Sancte3D/AMBIENT/field-ambience-current/docs/hardware/KICAD_BLUEPRINT.md

# KiCad Blueprint — Field Ambience (idiot-proof, step by step)

**Stand: r18.40 (2026-06-21).** This is the practical "what do I click, where,
in which order" guide. It assumes you have never laid out a PCB. Read top to
bottom once, then use it as a checklist.

> **THE ONE THING YOU MUST UNDERSTAND FIRST**
>
> **You do NOT draw the schematic.** It is generated by a Python script
> (`kicad/generate_kicad_project.py`). All ~80 components, every wire, every
> net name, and every footprint assignment already exist. You never place a
> resistor or draw a wire by hand in the schematic editor.
>
> Your real job is only two things:
> 1. **Open the project and run ERC** (electrical rule check) — confirm the
>    generated schematic is clean.
> 2. **Do the PCB layout** — there is no `.kicad_pcb` yet. This is the actual
>    hand-work: place footprints, route copper, run DRC, export Gerbers.
>
> So when you wonder "where do I connect what" — it's already connected. This
> doc shows you how to *read/verify* the connections (so you trust them) and
> then how to *physically lay them out*.

---

## 0. Install + open (5 minutes)

1. Install **KiCad 9** (kicad.org/download). Not 7, not 8 — the generator
   writes the KiCad-9 file format (`KICAD_VERSION_TAG = "20231120"`).
2. (Only if you ever change parts) regenerate the schematic:
   ```bash
   cd field-ambience-current/kicad
   python3 generate_kicad_project.py
   ```
   You normally DON'T need this — the `.kicad_sch` files are already committed.
3. Open **`field-ambience-current/kicad/field_ambience.kicad_pro`** in KiCad
   (File → Open Project, pick the `.kicad_pro`).
4. The Project window shows the schematic (`.kicad_sch`) and an empty PCB slot.

---

## 1. First-time library setup (do once)

The project uses three kinds of footprints. Two come bundled in the repo and
are already wired via `kicad/fp-lib-table`; the rest are KiCad's standard
libraries that ship with KiCad 9.

| Library | Where | Already configured? |
|---|---|---|
| KiCad standard (Package_QFP, Resistor_SMD, …) | ships with KiCad 9 | ✅ via your global fp-lib-table |
| `field_ambience` (6 custom footprints) | `kicad/libraries/field_ambience.pretty/` | ✅ via project `fp-lib-table` (`${KIPRJMOD}` path) |
| Keyswitch (Kailh/stabilizer) | `kicad/libraries/keyswitch-kicad-library/` | ✅ via project `fp-lib-table` |

**What to click once:**
- **Preferences → Manage Symbol Libraries** → tab "Project Specific Libraries"
  → confirm nothing is red. If KiCad asks to migrate libraries, accept.
- **Preferences → Manage Footprint Libraries** → tab "Project Specific
  Libraries" → you should see `field_ambience` (actively used everywhere,
  incl. the cell keyswitch SW1–5 as of r18.75), plus `Switch_Keyboard_Hotswap_Kailh`
  and `Mounting_Keyboard_Stabilizer` (vendored but currently unused — r18.74's
  hot-swap-socket approach was replaced by direct-solder in r18.75; harmless
  to leave registered). If any path is red, the `${KIPRJMOD}` variable isn't
  resolving — reopen via the `.kicad_pro`, not the `.kicad_sch`.

---

## 2. Schematic phase — what to DO and what NOT to do

### DO NOT
- ❌ draw wires
- ❌ place components
- ❌ change resistor values in the GUI (change them in the generator + re-run)
- ❌ "fix" anything by editing the `.kicad_sch` directly — the next generator
   run overwrites it. The generator is the source of truth.

### DO
1. Open the root schematic. You'll see **8 hierarchical sheets** (double-click
   a sheet box to go in, breadcrumb at top to come back):
   `power_tree`, `stm32h743`, `lcd`, `mcp`, `encoder`, `audio`, `battery`.
2. **Tools → Update Symbols from Library** (refreshes R/C/L/LED/GND symbols to
   your installed KiCad-9 versions — harmless, recommended).
3. **Inspect → Electrical Rules Checker → Run ERC.**
4. Compare the result against
   [`ERC_DRC_CHECKLIST.md`](ERC_DRC_CHECKLIST.md):
   - **0 errors** required.
   - Only the *intended* warnings listed there are allowed (power-pin-not-driven
     on the +5V bridge labels, PB3/SWO not connected, single MIDI_TX label,
     MCP reserve pins). Anything else must be understood before layout.
5. If ERC is clean per the checklist → schematic phase is DONE. Move to §4.

> Why bother if it's generated? Because the generator's structural checks
> (paren balance, 100/100 pin connectivity, hier↔root crossref) are NOT the
> same as KiCad's electrical check. The GUI ERC is the gate before layout
> (`PCB_LAYOUT_STATUS.md` blocker **B3**). It has never been run in a GUI yet —
> you are the first to do it.

---

## 3. Connection reference (so you can SEE what's connected to what)

You don't wire these — this is just the map, so when you look at the schematic
or route the board you know what each net is. Full detail: `SPEC_v0.7.md §5`.
Parts + order links: `BOM_MASTER.md`.

### 3.1 Block diagram (signal flow)

```
        USB-C (J1) ──► PTC F1 ──► TVS ──► +5V rail ──► TPS61089 boost (U8)+L1
            │                                  │
            │ D+/D-/CC (ESD via D1)            ├──► AP7361C LDO (U5) ──► +3V3 rail
            │                                  │
       BQ24074 power-path charger (U7, r19.18 ADR-0023) ◄── F2 PTC ◄── battery (J9, LiPo)
                                               │
   ┌───────────────────────── +3V3 ───────────┴───────────────────────┐
   │                                                                    │
   STM32H743 (U1, LQFP-100)                                             │
   │  ├─ SAI1 (I²S) ──► PCM5102A DAC (U3) ──► PAM8403 amp (U4) ──► SPK L/R (J6/J7)
   │  │                                            └─ Line-Out jack (J8, mutes spk)
   │  ├─ SPI1 ──────► ST7789 LCD (J3 header)
   │  ├─ I²C1 ──┬──► MCP23017 (U2) ──► 10 buttons (5 cell + 5 modifier) + jack-detect
   │  │         └──► PCA9685 (U6) ──► 15 LEDs + LCD backlight FET (Q2)
   │  ├─ TIM1/2/3/4 QEI ──► 4 encoders (EN1-EN4)
   │  ├─ ADC ──► BAT_SENSE (cells are digital on the MCP23017 now — r18.73)
   │  ├─ USART2 ──► MIDI TX (J9, DNP for now)
   │  └─ USB-OTG-FS (PA11/PA12) + SWD (J4 Tag-Connect)
   └────────────────────────────────────────────────────────────────────┘
```

### 3.2 STM32H743 pin map (the 30 used GPIOs)

| Net | Pin | Port | Goes to |
|---|---|---|---|
| I2S_LRCK | 3 | PE4 | PCM5102A pin 15 |
| I2S_BCK | 4 | PE5 | PCM5102A pin 13 |
| I2S_DOUT | 5 | PE6 | PCM5102A pin 14 |
| LCD_SCK | 29 | PA5 | LCD SCL |
| LCD_MOSI | 31 | PA7 | LCD SDA |
| LCD_CS | 30 | PA6 | LCD CSn |
| LCD_DC | 32 | PC4 | LCD D/C |
| LCD_RES | 33 | PC5 | LCD reset |
| I2C_SCL | 92 | PB6 | MCP23017 + PCA9685 (+ 4.7 kΩ pull-up to +3V3) |
| I2C_SDA | 93 | PB7 | MCP23017 + PCA9685 (+ 4.7 kΩ pull-up to +3V3) |
| MCP_INT | 7 | PC13 | MCP23017 INTA |
| DRIVE_A/B | 22/23 | PA0/PA1 | EN1 (TIM2) |
| BRIGHT_A/B | 63/64 | PC6/PC7 | EN2 (TIM3) |
| DISPLAY_A/B | 59/60 | PD12/PD13 | EN3 (TIM4) |
| VOL_A/B | 67/68 | PA8/PA9 | EN4 (TIM1) |
| DRIVE/BRIGHT/DISPLAY_SW | 97/98/2 | PE0/PE1/PE3 | encoder push switches (EN4_SW on MCP GPB5) |
| CELL1..5_BTN | MCP23017 GPA0–4 | (over I²C) | 5 cell tactile switches SW1–5 → GND (r18.73; PC0/PC1/PA4/PB0/PB1 now free) |
| BAT_SENSE | 25 | PA3 | 100k/100k divider off battery (ADC) |
| AMP_nSHDN | 53 | PB14 | PAM8403 /SHDN (10 kΩ pull-down) |
| AMP_nMUTE | 54 | PB15 | PAM8403 /MUTE (10 kΩ pull-down) |
| STATUS_LED | 55 | PD8 | heartbeat LED |
| MIDI_TX | 86 | PD5 | TRS jack (DNP) |
| USB_DM/DP | 70/71 | PA11/PA12 | USB-C data via D1 ESD |
| SWDIO/SWCLK | 72/76 | PA13/PA14 | J4 SWD |
| HSE | 12/13 | PH0/PH1 | 8 MHz crystal Y1 + 2× 27 pF |
| NRST / BOOT0 | 14 / 94 | — | reset / boot (BOOT0 1 kΩ pull-down + button) |

**Power pins (just connect to rails — no logic):** VDD (11,27,50,75,100)→+3V3,
VSS (10,26,49,74)→GND, VBAT(6)→+3V3, VDDA(21)→+3V3 via ferrite, VREF+(20)→VDDA,
VSSA(19)→GND, VCAP1/2 (48,73)→2.2 µF each to GND.

### 3.3 The resistor/cap values you'll see (already placed by generator)

| Where | Value | Why |
|---|---|---|
| I²C pull-ups (2×) | 4.7 kΩ 0603 | SDA/SCL to +3V3 |
| LED ballast (15×) | 390 Ω 0603 | each LED, +5V anode → LED → PCA9685 sink |
| BAT_SENSE divider | 100 kΩ + 100 kΩ 0603 | halves battery V into ADC range |
| BOOT0 pull-down | 1 kΩ 0603 | boots to flash, button overrides |
| AMP /SHDN, /MUTE pull-downs | 10 kΩ 0603 | amp boots OFF + muted (pop-free) |
| ~~Hall RC (per cell)~~ | — | removed r18.73 — cells are digital switches on the MCP23017 |
| HSE load caps | 2× 27 pF C0G 0603 | crystal |
| VDD decoupling (per pin) | 4.7 µF 0805 + 100 nF 0603 | 1 pair per VDD pin |
| VDDA filter | ferrite BLM18AG601 + 1 µF + 100 nF | analog isolation |
| VCAP1/VCAP2 | 2.2 µF X5R 0603 each | internal SMPS bulk |
| C_BULK / C_BULK2 | 470 µF tantal + 100 µF MLCC | boost output bulk |
| I²S series term (if used) | 33 Ω 0603 | — |

You change these by editing the generator, not the GUI. They're listed so you
recognise them on the board.

---

## 4. Footprints — already assigned, just verify

Every symbol already has a footprint (the generator sets it). You don't assign
them. To confirm:

- **Tools → Assign Footprints** (CvPcb) — opens the symbol↔footprint list.
  Everything should already be filled. Spot-check the custom ones:

| Ref | Footprint | Library |
|---|---|---|
| U1 STM32 | `Package_QFP:LQFP-100_14x14mm_P0.5mm` | KiCad std |
| U8 boost | `field_ambience:Texas_VQFN-HR-11_2x2.5mm_P0.5mm_RNR0011A` | custom |
| L1 inductor | `field_ambience:L_Sunlord_SWPA6045` | custom |
| Y1 crystal | `field_ambience:Crystal_HC49-US-SMD_ABLS` | custom |
| J8 audio jack | `field_ambience:Jack_3.5mm_PJ-320D_SMT` | custom |
| SW1-5 cells (real keyswitch, direct-solder, r18.75) | `field_ambience:SW_KailhChoc_CPG1350_THT_2P` | pulled from LCSC/EasyEDA for C400229 via `easyeda2kicad`, incl. 3D STEP — same method as this repo's other custom footprints |
| SW6-10 modifiers | `field_ambience:SW_TC1212-7.3_THT_4P` | custom (HX B3F-4055, C36498965) |
| SW11/SW_BOOT | `field_ambience:SW_TS1088_SMD` | custom |
| J1 USB-C | `Connector_USB:USB_C_Receptacle_HRO_TYPE-C-31-M-12` | KiCad std |

Full table: `BOM_MASTER.md` and `PCB_FOOTPRINT_RISK_AUDIT.md`. The audit also
tells you which ones are *mechanically critical* (must match the enclosure) —
read §6 of that file before placing them.

---

## 5. Schematic → PCB (the transfer — this CREATES the empty board)

1. From the schematic editor: **Tools → Open PCB Editor** (or from the project
   window, double-click the `.kicad_pcb` slot — KiCad offers to create it).
2. In the PCB editor: **Tools → Update PCB from Schematic** (hotkey **F8**).
3. Dialog appears — leave defaults, click **Update PCB**. Now ALL footprints
   appear in a pile off to the side, with thin "ratsnest" lines showing every
   connection from the schematic. **This is your wiring made physical** — you
   never drew it, the netlist carries it over.
4. Click **Close**. You now have an unrouted board.

> Re-run F8 any time the schematic changes — it syncs new parts/nets without
> destroying your placement.

---

## 6. Board setup (do this BEFORE placing/routing) — Tools → Board Setup

### 6.1 Layer stack-up (SPEC §9)
- **File → Board Setup → Board Stackup → Physical Stackup**: set **4 layers**.
- Assign: **F.Cu = Signal**, **In1.Cu = GND** (solid pour), **In2.Cu = +5V**
  (power), **B.Cu = Signal**. Board thickness **1.6 mm**.

### 6.2 Design Rules (Board Setup → Design Rules → Constraints)
JLCPCB 4-layer econ capabilities:
- Min track width: **0.15 mm** (set clearance default 0.15 mm too)
- Min via: **0.3 mm drill / 0.45 mm diameter** (annular ≥ 0.075 mm)
- Min hole-to-hole: 0.5 mm

### 6.3 Net classes (Board Setup → Net Classes) — set track widths
| Class | Track width | Apply to |
|---|---|---|
| Default (signal) | 0.25 mm | everything |
| Power | 0.5 mm | +3V3 |
| HighCurrent | 0.8 mm | +5V, VBAT, boost SW node, speaker outputs |
| GND | use the pour, not tracks | — |

(The generator's `.kicad_pro` already sets `copper_line_width = 0.2` as the
editor default; the net classes above override per-net where current needs it.)

---

## 7. Placement + routing order (the actual layout work)

Place in this order — group by sub-circuit, keep loops short:

1. **Fixed/mechanical first** (these are constrained by the enclosure — see
   `PCB_FOOTPRINT_RISK_AUDIT.md §6` + `mechanical/coordinates/`):
   USB-C (board edge), audio jack (board edge), LCD header, the 5 cell switches
   (SW1–5) on the 19 mm grid, 5 modifier buttons (SW6–10), 4
   encoders, battery connector, mounting holes.
2. **Power section**: USB-C → F1 → TPS61089 + L1 + bulk caps. Keep the boost
   loop (U8 ↔ L1 ↔ C_OUT) as tight as possible — this is the #1 power rule
   (SPEC §5.1, TI datasheet §10). Then the LDO.
3. **MCU + decoupling**: STM32 in the middle, each VDD's 4.7 µF+100 nF pair
   *right next to its pin*. Crystal Y1 + its 2 caps as close to PH0/PH1 as
   possible with a guard.
4. **Audio**: PCM5102A close to the MCU's SAI pins, its decoupling < 5 mm,
   single-star GND between audio and digital, ferrite beads in the speaker
   lines (SPEC §5.1 audio-layout-constraints — read those 5 points).
5. **I/O**: MCP23017, PCA9685, LEDs near their buttons/cells.

**Then route:**
- **Pour GND on In1.Cu** (Place → Add Filled Zone → pick GND net, draw over
  whole board). Pour **+5V on In2.Cu**. Right-click a zone → **Fill All Zones**
  (hotkey **B**) after routing.
- Route power (thick) first, then clocks/I²S, then the rest. Use the net-class
  widths from §6.3.
- Right-click a track → **Properties** to change width; right-click a pad →
  **Highlight Net** to see where it goes.

---

## 8. Verify + export (the order-ready gate)

1. **Inspect → Design Rules Checker → Run DRC.** Target per
   `ERC_DRC_CHECKLIST.md`: **0 errors, 0 clearance/mechanical/routing
   warnings.** Unconnected nets = forgotten routing.
2. **3D view (Alt+3)**: check nothing collides, parts sit where the enclosure
   expects. Compare against `mechanical/3d_models/MANIFEST.md` heights.
3. **1:1 paper print** of the board outline + cutouts, hold the real
   USB-C/jack/encoder/cells against it (audit §11).
4. **Export Gerbers**: File → Fabrication Outputs → Gerbers + Drill files.
5. **BOM + CPL** for JLC assembly: File → Fabrication Outputs → BOM, and the
   Placement (CPL) file. Cross-check LCSC numbers against `BOM_MASTER.md`.
6. In JLCPCB's web uploader: load Gerbers, then BOM+CPL, then **walk the
   assembly preview part by part** — look for flipped pin-1 markers and any
   "footprint not found". Pay attention to the 6 custom footprints.

---

## 9. Cheat-sheet — right-click / hotkeys you'll actually use

**Schematic editor:**
- `E` — edit properties of selected item
- Inspect → Electrical Rules Checker — the ERC
- Tools → Update Symbols from Library — refresh std symbols
- Tools → Assign Footprints (CvPcb) — view symbol↔footprint map

**PCB editor:**
- `F8` — Update PCB from Schematic (sync after any schematic change)
- `X` — start routing a track from a pad
- `B` — fill all zones (GND/power pours)
- `E` — edit selected track/footprint properties (width, layer)
- `M` — move, `R` — rotate, `F` — flip to other side
- `D` — drag track keeping connections
- right-click pad/track → **Highlight Net** — trace a connection visually
- right-click → **Properties** — change track width / via size
- `Alt+3` — 3D viewer
- Inspect → Design Rules Checker — the DRC

---

## 10. What is NOT done yet (so you know the edges)

- **No `.kicad_pcb` exists** — §5 creates it; everything in §6–8 is greenfield.
- **GUI-ERC never run** — you are the first (blocker B3).
- **TPS61089 layout** needs the TI datasheet §10 study before routing (audit §7).
- **LCD header pin order** must be checked against the actual Waveshare module
  you receive — vendor batches vary (audit §11).
- **Enclosure CAD** isn't final, so the mechanical-critical X/Y positions in
  `mechanical/coordinates/` may still move — confirm before you commit to edge
  placements.

---

### Where the truth lives (don't trust this doc over these)
- Connections / values / pins → `kicad/generate_kicad_project.py` + `SPEC_v0.7.md §5`
- Parts / order links / footprints → `BOM_MASTER.md`
- Footprint risk + mechanical-critical list → `PCB_FOOTPRINT_RISK_AUDIT.md`
- ERC/DRC pass criteria → `docs/hardware/ERC_DRC_CHECKLIST.md`
- Current overall state → `PROJECT_STATUS.md`
