Sancte3D/AMBIENT/field-ambience-current/docs/hardware/MECHANICAL_REQUIREMENTS.md

# Mechanical Requirements — Gehäuse & PCB-Constraints

Diese Datei listet **alle mechanisch-fixierten Bauteile** mit ihren
Constraint-Maßen + Gehäuse-Anforderungen, damit das Case-CAD (3D-Print) und
das PCB-Layout gleichzeitig entstehen können, ohne sich gegenseitig zu blocken.

Adressat: PCB-Designer (Bauteilplatzierung Schritt 7 des PCB-Workflows) +
3D-CAD-Designer (Gehäuse-Modellierung). Beide brauchen die selben Maße.

> **Status:** PROPOSED — die Maße sind aus Datenblättern + bestehenden ADRs
> abgeleitet. **UNVERIFIED**-Markierungen wo eine Datenblatt-Quelle fehlt.
> Bevor die Mechanik final ist, müssen die UNVERIFIED-Items mit dem realen
> Bauteil in der Hand bestätigt werden (Anti-Guess, CLAUDE.md).

---

## 0. Globale Constraints

| Constraint | Wert | Quelle |
|---|---|---|
| Gerät handheld, 1-Hand-Bedienung | ja | PROJECT_STATUS §2 |
| Max. PCB-Außenmaße | **TBD — User entscheidet** | hängt am Gehäuse-Form-Faktor |
| Vorgeschlagen: ~120 × 80 mm (Stack-Mate-OP-1-Klasse) | Vorschlag | basiert auf 4 Encoder + 5 Cells + Display + Speakers passen müssen |
| PCB-Dicke | 1,6 mm | ADR-0018 (JLCPCB Default 4-Layer) |
| Layer-Stack | 4-Layer | ADR-0018 |
| Mounting (Schraube) | M3 × 4 Eckbohrungen, Ø 3,2 mm Drill | Standard, Gehäuse muss Pillars/Standoffs liefern |
| Gehäuse-Material | 3D-Print PLA/PETG (Single-Color OP-1-Look) | Cost-Trade-Off, kein Alu-CNC (Cost) |
| Bottom-Plate abnehmbar | ja, für Service-Bohrungen `SW11` (Reset) + `SW_BOOT` (DFU) + Akku-JST-Zugang | ADR-0008/Service-Strategie |

---

## 1.0 External / visible components — case-design inventory

Everything that appears on an **outer surface** of the enclosure — i.e. what the
case must provide a window / cutout / hole / grille / slot for. Placement of most
of these is **your design**; this is the *inventory*, not a layout.

**Headline counts:**

- **Touch controls: 15** → 4 encoders + 5 cell keys + 5 modifier buttons + 1 power switch
- **Display: 1** window
- **Indicator LEDs: 23** (light points needing egress) → 5 modifier + 10 cell + 8 VU-meter
- **Ports: 3** → USB-C + line-out + MIDI
- **Speakers: 2** grilles
- **Bottom service: 2 pinholes + battery access + 4 screws**

### TOP face (primary UI)

| Component | Count | What it's for | Case needs |
|---|---|---|---|
| Display (Waveshare 1.9″ LCD 170×320) | 1 | the screen — worlds, params, meters | window = active area + 0.5 mm/side; must show the full active area |
| Push-encoders (ALPS EC11) + 3D-print knobs Ø19–20 mm | 4 | global params + a push function each | 4 shaft holes; knobs sit ~10 mm above the top plate |
| Cell keys (Kailh Choc V1, direct-solder, real keyswitch, digital trigger) + 3D-print caps | 5 | the playable keys (digital on/off; r18.75, ADR-0013 superseded — real ~3mm keyswitch travel, distinct feel from the modifier buttons) | 5 keyswitches, 19 mm pitch; ~15×15 mm switch envelope each; caps clip onto the Choc V1 stem |
| Modifier buttons (HX B3F-4055 tactile) + caps | 5 | Shift / Hold / Drone / Generate / Clear — deliberately a smaller/plainer feel than the cells | 5 button holes; caps clip onto the square head |
| Modifier LEDs (mono) | 5 | per-button status (Shift=yellow, Hold=green, other 3 white) | 5 light points — translucent cap / lightpipe / window |
| Cell LEDs (2 per cell: yellow + green) | 10 | cell hold-status (base / shift) | 10 light points — glow the keycap or a window per cell |
| VU-meter LEDs (white, in a row) | 8 | live audio level (OP-1-style) | 8 light points / a light-bar window; row position = your choice |

### SIDE faces (edges)

| Component | Count | What it's for | Case needs |
|---|---|---|---|
| USB-C (J1) | 1 | charging + USB-DFU firmware flash | edge cutout for the receptacle |
| Line-out 3.5 mm (J8) | 1 | audio out to headphones / mixer | 3.5 mm hole; opposite edge from the switching regulators |
| MIDI-out 3.5 mm (J10) | 1 | MIDI out (TRS Type A) | 3.5 mm hole |
| Power slide switch (SW_PWR) | 1 | on/off, side-actuated ("off but still charges") | side slot + your own slider cap, same-axis sliding (cap takes the force). ⚠ r18.85: ALPS SSSS811101 — body only 1.4 mm tall, stem window z ≈ 0–1.4 mm above PCB → slot + cap finger must reach near board level (old MST was 2.3–3.8 mm) |
| Speaker grilles | 2 | the two speakers | 2× Ø25–35 mm open area + dust mesh; ≥50 mm apart; sealed ~5 cm³ chamber behind each (critical for sound). Top or side — your choice |

### BOTTOM face

| Component | Count | What it's for | Case needs |
|---|---|---|---|
| Service pinholes | 2 | Reset (SW11) + BOOT0 (SW_BOOT), paperclip access | 2× ~Ø2 mm pinholes |
| Battery access | 1 | LiPo pouch (52×39×10 mm) + JST disconnect | removable bottom piece or slot/door |
| Mounting screws | 4 | hold top + bottom together | 4 corner bosses/standoffs, M3 (Ø3.2 mm) |
| Status LED (optional) | ≤2 | power / charge indicator (heartbeat + charger) | optional lightpipe to the bottom plate |

> The LED **egress method** (translucent caps vs lightpipes vs windows) is a
> design choice — the firmware just drives the LEDs. Speaker placement (top vs
> side) and the exact row/grid positions are also yours; the PCB puts the
> emitters where your case wants the light/sound to exit.

---

## 1. Mechanisch-fixierte Bauteile (must-place-first)

Diese Bauteile **müssen** vor allen anderen platziert sein — sie sind durch das
Gehäuse oder die Bedienflächen positionell fest.

### 1.1 Display `LCD-Modul` (Waveshare 1.9″ 170×320 ST7789V2)

| Maß | Wert | Quelle |
|---|---|---|
| Modul-PCB-Außenmaße (LxBxH) | ≈ 47,6 × 23,4 × 5,2 mm | **UNVERIFIED** — Waveshare-Doku nochmal prüfen |
| Active Area (LxB) | ≈ 39,1 × 21,2 mm | Waveshare 1.9″-Spec |
| 8-Pin-Header-Position | Lange Seite, Pin-Pitch 2,54 mm | siehe `J3` Pinout im Walkthrough §6 |
| Pin-Reihenfolge (gegen J3) | **UNVERIFIED — gegen geliefertes Modul prüfen** vor finaler Layout-Bestätigung | r18.22 Note |
| Gehäuse-Fenster-Cutout | Active Area + ≤ 1 mm Toleranz pro Seite (LxB ≈ 41 × 23 mm) | Standard |
| Tiefe vom PCB | 5,2 mm Modul-Höhe + ~3 mm J3-Pin-Header → **min. 8 mm Vertical-Clearance** zwischen PCB-Top und Gehäuse-Front-Innenseite | Stack-Up |
| **Display für diesen PCB-Rev EINGEFROREN auf 1.9″** (r18.64, User „1,9 zoll reicht safe") | verwende die 1.9″-Maße oben | nicht layout-blockierend |
| **ADR-0015 PROPOSED:** Pivot auf 2.0″ 240×320 → **Rev-B** | Maße noch zu verifizieren | BOM UNVERIFIED, kein Blocker mehr |

### 1.2 USB-C Connector `J1` (TYPE-C-31-M-12)

| Maß | Wert | Quelle |
|---|---|---|
| Body (LxBxH) | ≈ 7,3 × 8,9 × 3,2 mm | Datasheet |
| Lage | **An Gehäuse-Kante** (kürzeste USB-Buchse mit D+/D- Spec USB 2.0) | Standard-Constraint |
| Cutout im Gehäuse | 9 × 4 mm rechteckig (Schienen-Toleranz +0,2 mm) | herstellertypisch |
| PCB-Edge-Abstand vom Connector-Anschlag | 0 mm — Buchse muss bündig oder leicht aus dem Gehäuse heraus | Steckbarkeit |
| Footprint | `Connector_USB:USB_C_Receptacle_HRO_TYPE-C-31-M-12` | BOM §3 |
| Cycles-Klasse | ~5k Insertion-Cycles | r18.19 (akzeptiert) |

### 1.3 3.5 mm Audio-Jack `J8` (PJ-320D, mit Insertion-Detect)

| Maß | Wert | Quelle |
|---|---|---|
| Body (LxBxH) | ≈ 14,5 × 6,1 × 5,1 mm | EasyEDA-CAD vendored r18.19 |
| Lage | An Gehäuse-Kante (gegenüber oder seitlich von USB-C) | Bedienbarkeit |
| Cutout | Ø 6,5 mm Kreisbohrung + 14 mm Body-Schlitz | Standard 3,5 mm Klinke |
| Footprint | `field_ambience:Jack_3.5mm_PJ-320D_SMT` (Custom) | BOM §4 |
| Insertion-Detect-Pin → MCP23017 GPIO | für Auto-Mute der Speaker beim Einstecken | ADR-0007 |

### 1.4 Encoder × 4 `EN1..EN4` (ALPS EC11E18244AU)

| Maß | Wert | Quelle |
|---|---|---|
| Body (BxHxT) | 12 × 12 × 7,5 mm (Body, ohne Schaft) | ALPS-Datasheet |
| Schaftlänge | 20 mm (Flat-Shaft, "20 mm" Suffix B4) | ALPS-Datasheet |
| Cutout im Gehäuse (Top-Plate) | Ø 7,3 mm pro Encoder (Standard) | herstellertypisch |
| Knopf-Höhe über Top-Plate | ~10 mm (3D-gedruckte Knöpfe Ø 19–20 mm × 8–10 mm) | BOM §6 r18.21 |
| Pitch zwischen Encodern | ≥ 22 mm Center-to-Center (Daumen passt zwischen 2 Knöpfen) | ergonomisch |
| Anordnung 4× nebeneinander | Bündel oben oder seitlich, je nach Gehäuse-Konzept | User-Entscheidung |
| Mounting | Through-Hole, 5,1 mm hohe Lötseite — PCB-Underside-Clearance | Datasheet |

### 1.5 Cell-Switches × 5 `SW1..SW5` (Kailh Choc V1, direct-solder, ADR-0013 abgelöst)

> **r18.73 (ADR-0013 abgelöst):** Cells wurden digital am MCP23017 (HiChord-
> Batch-4+-Weg). **r18.74 (User-UX-Korrektur):** r18.73 hatte die Cells auf
> **dasselbe kleine THT-Tactile wie die Modifier** gesetzt (HX B3F-4055) — das
> macht die spielbaren Cells ununterscheidbar von simplen Modifier-Knöpfen und
> zerstört das "Tastatur/Keyboard"-Spielgefühl. Cells bekamen einen Kailh-Choc-
> Hot-Swap-Socket für echtes Tastengefühl.
>
> **r18.75 (User-Nachfrage "wie wird das gelötet?"):** der Hot-Swap-Socket aus
> r18.74 hatte **keine saubere Hersteller-/LCSC-Teilenummer** und hätte eine
> nicht offensichtliche Klein-SMD-Handlöttechnik gebraucht. **Fix:** der Kailh-
> Choc-V1-Switch (**CPG135001D01**) wird jetzt **direkt auf die Platine
> gelötet** — 2 THT-Beinchen durch 2 Löcher, von hinten verlötet, exakt dieselbe
> Technik wie bei jedem anderen Button/Connector in diesem Design. Kein Socket,
> keine Spezialtechnik mehr — dafür ist der Switch jetzt fest verlötet (nicht
> mehr tauschbar). Footprint + 3D-STEP direkt von LCSC/EasyEDA für dieses exakte
> Teil gezogen (`easyeda2kicad --full --lcsc_id=C400229`), vendored als
> `field_ambience:SW_KailhChoc_CPG1350_THT_2P`.

| Maß | Wert | Quelle |
|---|---|---|
| Switch-Envelope (LxB) | **15 × 15 mm** (Kailh-Choc-Standard) | Kailh-Herstellerangabe (mehrfach bestätigt in öffentlichen Quellen) |
| Hub (Travel) | **~3 mm** echter mechanischer Hub (Choc-Klasse) | Kailh-Choc-Spec |
| Stem | V1 ~3,4 mm (proprietär) | Kailh-Herstellerangabe — Cap-Stem-Interface danach designen |
| Pitch zwischen Cells | 19 mm aktuell — **⚠ OFFEN für Aron:** User will später 2–3 cm lange Caps; das kollidiert bei dieser Teilung mit dem Nachbar-Cell wenn links-rechts orientiert (siehe `mechanical_coordinates.md` §3.4 für die zwei Lösungswege + verfügbaren Platz) | Industrial-Design / PCB-Layout (Aron) |
| Mounting | **Direkt-Lötung, THT** — 2 elektrische Pins + 3 unbestückte Mechanik-Loecher (Switch-eigene Pegs geben seitliche Stabilität ohne Plate); **Plate optional** für mehr Steifigkeit bei häufigem Spielen | Generator (mcp_sheet, GPA0–GPA4); Footprint `field_ambience:SW_KailhChoc_CPG1350_THT_2P` |
| Cap | 3D-Druck-Cap clippt auf den Choc-V1-Stem (Ziel: 2–3 cm lang, s.o.) | Custom-CAD (User) |
| Switch-Sourcing | LCSC **C400229** (CPG135001D01, rot/linear) — reale, verifizierte Listung. ⚠ **r18.78: alle 3 Choc-V1-Farben bei LCSC aktuell 0 Lagerbestand** (auch C400230 braun/tactile, C400231 weiß/klicky — alle real, nur temporär ausverkauft). Kein Blocker: Switch wird handgelötet (nicht JLC-SMT-Linie), daher nicht auf LCSC-Bestand angewiesen — jede Choc-V1-Farbe von jedem Vendor (Kailh direkt, KBDfans, NovelKeys, AliExpress) passt in denselben Footprint | Feel/Farbe = freie Wahl, keine Schematic-Einschränkung |

### 1.6 Modifier-Buttons × 5 `SW6..SW10` (HX 12×12×7.3TPFT-B)

> **r18.65-FIX:** Diese Tabelle führte fälschlich den **TS-1088** (3,9×2,9 mm
> Service-Taster aus §1.9) als Modifier-Button. Quelle der Wahrheit (Generator
> Z. 4111) verbaut für SW6–SW10 den **HX 12×12×7.3TPFT-B** (C36498966),
> Custom-Footprint `field_ambience:SW_HX_12x12x7.3_SMD-4P`. Höhe daher **7,3 mm**
> statt der alten falschen ~2 mm — relevant fürs Top-Plate-Clearance.

| Maß | Wert | Quelle |
|---|---|---|
| Switch-Body (LxBxH) | **11,8 × 11,8 × 7,3 mm** (vertikaler Plunger oben) | Footprint-descr + LCSC C36498966 |
| Höhe über PCB | **7,3 mm** (Plunger-Spitze) → Vertical-Clearance Top-Plate | Datasheet |
| Pad-Pattern / Keep-out | 4× 2,5×1,5 mm Pads auf 7 mm-Pitch (X+Y); 11,8×11,8 mm Body-Keep-out | Generator FP_NOTE Z. 4118 |
| Cutout im Gehäuse | Plunger-Ø **UNVERIFIED — DS prüfen**; bei 3D-Print-Cap: per Cap | Anti-Guess |
| Cap-Höhe (optional 3D-Print über Top-Plate) | User-CAD | User |
| Pitch | ≥ 16 mm Center-to-Center (12 mm Body + Fingerabstand) | ergonomisch |
| Lage | Top-Plate, oberhalb/neben den Cells | User-Entscheidung |
| LED daneben | je 1 Modifier-LED neben dem Button (Walkthrough §4) | — |

### 1.7 Speaker × 2 `J7` (PUI AS04008PS 8 Ω 40 mm)

| Maß | Wert | Quelle |
|---|---|---|
| Driver-Durchmesser | 40 mm | PUI-Datasheet |
| Driver-Tiefe | ~5 mm | PUI-Datasheet |
| Gehäuse-Schallaustritt (Grill-Pattern) | Ø 25–35 mm offener Bereich + Dust-Mesh (ADR-0007) | ADR-0007 |
| **Akustische Kammer pro Speaker** | **min. ~5 cm³ luftdicht** hinter jedem Driver, kritisch für "nicht Plastik-Spielzeug"-Sound | Walkthrough §3 |
| Pitch zwischen Speakern | Stereo-Spreizung, ≥ 50 mm Center-to-Center | psycho-akustisch |
| Anschluss | 2-Pin-Header pro Speaker (BTL-Pärchen) | BOM §4 |

### 1.8 LiPo-Akku 2000 mAh `LiPo-Pouch`

| Maß | Wert | Quelle |
|---|---|---|
| Pouch-Maße (LxBxH) | 50 × 37 × 9,4 mm | r18.21 Spec |
| Lage | **Bottom-Case-Slot**, NICHT auf der PCB | BOM §3 |
| JST-PH-Stecker `J_BAT` | im Inneren erreichbar (für Lagerung-Trennung, ADR-0016) | ADR-0016 |
| Slot-Maße (Gehäuse) | 52 × 39 × 10 mm minimum (Akku + Kabel-Knick-Reserve) | Pouch + 5 % |

### 1.9 Service-Buchten (Bottom-Plate)

| Element | Loch-Position | Bedeutung |
|---|---|---|
| `SW11` Reset | kleines Loch in Bottom-Plate (Ø ~2 mm), Büroklammer-Zugang | manueller MCU-Reset |
| `SW_BOOT` BOOT0 | gleiches Pattern, neben `SW11` | USB-DFU-Flash (Long-Press = Sleep ab ADR-0016) |
| LiPo-JST-Zugang | Slot oder herausnehmbares Bottom-Plate-Stück | Lagerungs-Trennung |
| Status-LED-Sichtbarkeit (`STATUS_LED`, ein PCB-LED am MCU) | optional Lichtleiter ins Bottom-Plate | Power-Indicator |

---

## 2. Layout-Order-Vorgabe (für PCB-Designer)

In dieser Reihenfolge platzieren. *Erst diese Liste durch, dann kommt die
restliche elektrische Platzierung* (ADR-0018 Routing-Regeln).

1. **Display `J3`** — Top-Center oder Top-Edge je nach Gehäuse-Konzept
2. **USB-C `J1`** — Kante (links oder rechts)
3. **3.5 mm Jack `J8`** — andere Kante als `J1`, weg von Switching-Reglern
4. **5 Cell-Switches SW1–5 (Kailh-Choc-V1, direkt-gelötet, digital)** — Mittelbereich,
   Standard-MX-Pitch 19 mm, optional Plate darüber
5. **5 Modifier-Buttons + 5 Modifier-LEDs** — Top-Plate-Pattern
6. **4 Encoder** — Top-Plate-Reihe
7. **Speaker-Header × 2** — Flanken, Schallaustritt-Gehäuse-Öffnungen drüber
8. **LiPo-JST `J_BAT`** — Innen, neben Bottom-Plate-Zugang
9. **Service-Buttons `SW11` + `SW_BOOT`** — Bottom-Plate-Side
10. **Mounting-Bohrungen × 4** — Eckpunkte, M3 × 3,2 mm

---

## 3. Was beim Gehäuse-CAD beachten

- **Speaker-Kammern** = der mit Abstand wichtigste Punkt fürs Klangerlebnis
  (Walkthrough §3). Plane-CAD-Wände um jeden Driver, luftdicht (max 5 cm³).
- **Encoder-Schaft** kommt ~10 mm über die Top-Plate raus → die Knöpfe (eigene
  3D-Prints, Ø 19–20 mm × 8–10 mm) sitzen darauf.
- **Display-Fenster** = Active-Area + 0,5 mm Toleranz pro Seite. Bezel-Look
  optional, aber Cutout MUSS Active-Area komplett zeigen — ein abgeschnittener
  Pixel-Rand ist hässlich.
- **Cell-Plate** = entweder eine 2. PCB als Plate (FR-4 1,5 mm, 14 × 14 mm
  Cutouts) oder direkt in den Gehäuse-Top-3D-Print gefräst.
- **Bezel + Front-Symmetrie**: User-Geschmack, aber Encoder-Knöpfe links neben
  Display, Cells unter Display sind ergonomisch ok.

---

## 3b. Thermik & Lüftung — **keine Lüftungsschlitze nötig**

Gesamt-Verlustleistung ~1,5–2,2 W über das ganze Board → sehr niedrige
Flächendichte, passiv über PCB + Gehäuse abführbar (Innentemp-Ziel < 50 °C,
SCHEMATIC_WALKTHROUGH). Vergleichbare Geräte (OP-1 Field & Co.) sind komplett
dicht. **Keine Schlitze** — bräche den Look + ließe Staub rein.

Wärme-Budget (real):

- **MCU** STM32H743 0,4–0,6 W (LQFP-100 ~1 W passiv → unkritisch, U1-Review).
- **LDO** AP7361C ~0,5–0,6 W (5V→3,3V-Drop × MCU-Strom) → **heißester Punkt**.
- **Charger** BQ24074 (r19.18): Power-Path-Linearstufe, worst case ~(5V−4,2V)×0,89A ≈ 0,7 W **nur beim Laden** (transient; QFN-EP braucht Kupferflaeche).
- **Boost** TPS61089 + L1 ~0,2–0,3 W nur im Akkubetrieb.

Layout-Vorgaben statt Vents:

1. **LDO**: Kupferfläche + Thermal-Vias drunter; nicht thermisch isolieren.
2. **Charger nicht neben/unter den Akku** — Gerät lädt im Aus weiter → kein
   Airflow im geschlossenen Gehäuse.
3. **LiPo thermisch von LDO/Charger/Boost trennen** (Abstand). Der eigentliche
   Punkt ist nicht „Chip überhitzt", sondern „Akku nicht mitheizen"
   (Lebensdauer + Sicherheit). Akku sitzt ohnehin im Bottom-Case-Slot (§1.8) →
   Hotspots oben halten.
4. Bonus: die 4-Layer-GND/Power-Planes (ADR-0018) wirken als Wärme-Spreader.
5. Falls je ein Hotspot zu warm wird: Thermal-Pad IC → Gehäuse-Innenwand
   (Gehäuse als Heatsink) — dichter + eleganter als Schlitze.

---

## 4. UNVERIFIED-Liste (zu klären vor PCB-Bestellung)

1. **PCB-Außenmaße** — User-Entscheidung treffen
2. **LCD-Modul-Pin-Order** (Waveshare-Vendor-Variation) gegen tatsächlich
   geliefertes Modul (PCB_FOOTPRINT_RISK_AUDIT §6)
3. **2.0″-Display-Pivot-Maße** falls ADR-0015 D1 angenommen wird
4. **Encoder-Pitch + Knopf-Design** — abhängig vom Layout-Konzept
5. **Akustik-Kammer-Volumen** — empirisch im 3D-Druck-Prototyp ermitteln,
   nicht aus Datasheet (Driver-Performance hängt vom konkreten Plastikteil ab)

---

## 5. Related

- ADR-0011 — Enclosure-Thickness
- ADR-0013 — Cell-Magnetic-Hall (Position-Constraint Hall ↔ Magnet)
- ADR-0015 — 2.0″-Display-Pivot (PROPOSED, betrifft Position-Maße)
- ADR-0016 — Power & Sleep (Service-Buchten + JST-Zugang)
- ADR-0018 — PCB Layer-Stack (4-Layer, 1,6 mm)
- SCHEMATIC_WALKTHROUGH.md — Bauteile-Liste + Refdesigns + Funktion
- `PCB_FOOTPRINT_RISK_AUDIT.md` — alle MECH_CRITICAL-Footprints + offene
  Verifikationen
- KICAD_BLUEPRINT.md — Layout-Workflow-Anleitung
