Sancte3D/AMBIENT/field-ambience-current/docs/hardware/AI_READY_SCHEMATIC_STANDARD.md

# Rule: AI-Ready PCB Schematic Standard

**Status: BINDING (r18.41, 2026-06-21).** Applies to every create / review /
modify action on any PCB schematic in this repo. Referenced as a hard rule
from the repo-root `CLAUDE.md` so it loads into every session.

When creating, reviewing, or modifying any PCB schematic, always structure it
so that both a human engineer and an AI system can understand it without
guessing.

## Core Rule

The schematic must be treated as **machine-readable design data**, not only as
a visual drawing. Every component, net, sheet, symbol, footprint, and
functional block must be explicit, named consistently, and traceable.

> In THIS project the schematic is generated by
> `kicad/generate_kicad_project.py`. "Modifying the schematic" therefore means
> **editing the generator**, never hand-editing `.kicad_sch`. All standards
> below are enforced in the generator's per-component / per-net code.

## Scope — don't over-detail; nail the buildable core

The goal is a schematic that can actually be **built** and understood, not a
maximally annotated one. Prioritise accordingly:

**MUST-HAVE for every part / net (the schematic is not buildable without these):**
1. **Correct reference designator + descriptive name**
2. **Value** (R/C/L value, or the part's function)
3. **Footprint** (the exact one for the real package)
4. **Connectivity** — what connects to what, with which pin (this is the whole
   point: anyone, human or AI, must be able to read where each net goes)

**WHERE SENSIBLE (add when it matters for that part, skip the noise):**
- Full metadata (MPN, supplier PN, ratings, tolerance, lifecycle, datasheet)
  → essential on ICs / connectors / power parts; minimal on jellybean passives.
- Title-block author/notes, dedicated test points, exhaustive NC annotation
  → useful, not blockers. Add for critical nets, don't drown the sheet.

So: a 10 kΩ 0603 needs name + value + footprint + where its two ends connect —
not a paragraph. An IC or connector needs the full treatment (pinout verified,
package exact, orientation clear).

## Required Standards

### 1. Clean functional blocks
Split the schematic into logical sections, each with a clear title + purpose:
Power Input & Regulation · MCU / Processor Core · Audio / Sensor / Interface ·
Communication Interfaces · Display / UI Controls · Debug / Programming ·
Connectors · Mechanical / Mounting.

### 2. Consistent net naming
- Descriptive names, not random pin names: `3V3_IO`, `5V_USB`, `VBAT`,
  `MCU_RESET_N`, `SPI_MOSI`, `SPI_MISO`, `SPI_SCK`, `DISPLAY_CS`, `ENC_A`,
  `ENC_B`, `AUDIO_L_OUT`, `AUDIO_R_OUT`.
- **`_N` suffix for active-low** (e.g. `AMP_SHDN_N`, not `nSHDN`).
- **`_P` / `_N` for differential pairs.**
- No spaces, slashes, unclear abbreviations, or inconsistent capitalisation.

### 3. Complete component metadata
Each component includes, where possible: Manufacturer Part Number ·
Manufacturer Name · Supplier Part Number (LCSC / DigiKey / Mouser) · Package ·
Footprint · Value · Voltage / current / power rating · Tolerance (where
relevant) · Lifecycle status (if known) · Datasheet link / source reference.

### 4. Verified symbol-to-footprint mapping
Never assume a footprint is correct just because it exists. For every critical
component: check symbol pin numbers vs datasheet; check footprint pad numbers
vs datasheet; check polarity / pin 1 / orientation / notch / diode direction /
connector orientation; check the exact package variant (not "roughly"); if
JLC/LCSC assembly is intended, verify the exact LCSC part and exact footprint
map to the same physical package.

### 5. Standard, unique reference designators
`R` resistor · `C` capacitor · `U` IC · `J` connector · `L` inductor ·
`D` diode · `Q` transistor/MOSFET · `TP` test point · `Y` crystal/oscillator ·
`FB` ferrite bead · `SW`/`S` switch/button. Every designator unique and stable
across revisions.

### 6. Labels instead of long wires
Signal flow left→right; power top→bottom; related parts close together; long
crossing wires replaced with net labels; no visual spaghetti.

### 7. Title blocks + revision context
Every sheet: project name · sheet title · sheet number · revision · date ·
author/reviewer · short change notes if relevant.

### 8. Mark all intentional no-connects
No pin ambiguous. Unused IC pins marked NC only if the datasheet allows.
Unused inputs tied high/low where required. Enable, boot, reset, mode,
address, config pins always explicitly handled.

### 9. Explicit power design
Always show: input voltage range · power rails · regulators · required
input/output caps from datasheet · decoupling caps near ICs · current
capacity · protection circuits where needed · ground domains if analog /
digital / power ground are separated.

### 10. Test + debug access
Useful test points + programming/debug headers: `TP_3V3`, `TP_GND`,
`TP_RESET`, `TP_I2C_SCL`, `TP_I2C_SDA`, `SWDIO`, `SWCLK`, `UART_TX`, `UART_RX`.

## Claude Behavior Rule

When reviewing a schematic, do not only check if it "looks correct." Check if
it is **AI-readable, manufacturable, and verifiable.** For every issue report:
**what is wrong · why it matters · what could fail** (PCB layout, JLC
assembly, firmware, or debugging) **· how to fix it · severity** (critical /
important / minor).

## Do Not Guess

If a footprint, pinout, datasheet, package, polarity, connector orientation,
or supplier part cannot be verified, mark it exactly:

```
UNVERIFIED — NEEDS HUMAN CHECK
```

Never pretend a footprint is safe unless symbol, datasheet, package, and
footprint have been matched directly.

---

## Current project compliance snapshot (r18.41)

Honest mapping of this standard onto the repo as it stands. ✅ meets · 🟡
partial / gap · 🔴 missing.

| # | Standard | State | Notes / gap |
|---|---|---|---|
| 1 | Functional blocks | ✅ | 8 hierarchical sheets (power_tree, stm32h743, lcd, mcp, encoder, audio, battery + root). Each is a titled block. |
| 2 | Net naming | 🟡 | Mostly descriptive (`I2S_LRCK`, `LCD_SCK`, `CELL1_SENSE`). **Gap: active-low uses `nSHDN`/`nMUTE` prefix instead of the `_N` suffix this standard mandates.** Also `NRST` has no separator. Fix = rename in generator to `AMP_SHDN_N`, `AMP_MUTE_N`, `MCU_RESET_N`. Low risk (cosmetic + consistency), do on next generator pass. |
| 3 | Component metadata | ✅ | Generator sets MPN + Manufacturer + LCSC + Footprint + Value per part; `BOM_MASTER.md` is the sourcing view. Ratings/tolerance present on critical parts, sparse on jellybean passives (acceptable). |
| 4 | Symbol↔footprint verified | 🟡 | `PCB_FOOTPRINT_RISK_AUDIT.md` classifies every part and flags what still needs check. **9 PACKAGE_SAFE ICs need a one-pass GUI-ERC pin-map check; not yet done (no KiCad GUI in this env).** Those carry the equivalent of UNVERIFIED until that pass. |
| 5 | Reference designators | ✅ | Standard prefixes, generator assigns deterministically + uniquely. |
| 6 | Labels not spaghetti | ✅ | Hierarchical sheets + net labels by construction; generator places, not freehand. |
| 7 | Title blocks + revision | 🟡 | Sheets are titled; **explicit per-sheet title-block revision/date/author fields not all populated.** Add to generator's sheet headers. |
| 8 | No-connects explicit | 🟡 | Reserve pins carry intentional dangling labels (documented in `ERC_DRC_CHECKLIST.md`); BOOT0/NRST/EN handled. **Full NC audit is part of the pending GUI-ERC.** |
| 9 | Power design explicit | ✅ | Power tree sheet: USB-C → F1 → TPS61089 + L1 → LDO; per-pin decoupling; VDDA ferrite; protection (PTC, TVS, ESD). Ground-domain star point specified (SPEC §5.1). |
| 10 | Test/debug access | 🟡 | SWD via J4 Tag-Connect (`SWDIO`/`SWCLK`) present. **Dedicated `TP_*` test points (3V3/GND/RESET/I2C) not yet placed.** Add as 1 mm Cu test pads in the generator before layout. |

**Open standard-driven actions** (folded into the engine/PCB backlog):
- Rename active-low nets to `_N` suffix (std #2) — generator edit.
- Populate per-sheet title-block revision/date/author (std #7).
- Add `TP_3V3 / TP_GND / TP_RESET / TP_I2C_SCL / TP_I2C_SDA` test pads (std #10).
- Close the GUI-ERC pin-map + NC audit (std #4, #8) — the existing layout
  blocker B3, needs KiCad GUI (user-side).

These are tracked here rather than fixed blind; #2, #7, #10 are safe generator
edits and can be batched into the next schematic regeneration.

---

### Where the truth lives
- Net names / pins / values → `kicad/generate_kicad_project.py` + `SPEC_v0.7.md §5`
- Parts / metadata / supplier → `BOM_MASTER.md`
- Symbol↔footprint risk + UNVERIFIED list → `PCB_FOOTPRINT_RISK_AUDIT.md`
- ERC/DRC pass criteria → `docs/hardware/ERC_DRC_CHECKLIST.md`
- Step-by-step layout workflow → `docs/hardware/KICAD_BLUEPRINT.md`
