Sancte3D/AMBIENT/field-ambience-current/PCB_LAYOUT_STATUS.md

# PCB-Layout-Status — Field Ambience

**Stand: 2026-06-11 (v0.7-r18.9)**

## Kurzfassung

**Es existiert KEIN `.kicad_pcb`. Keine Gerber, keine BOM/CPL-Exports, keine Bestellung.** Der Schaltplan ist auf STM32H743 migriert (r18.5) und in r18.6 mit allen verfügbaren öffentlichen Datenblatt-Quellen verifiziert. Layout (= NATIVE_PORT_PLAN Step 13 **Phase 6**) ist bewusst noch nicht gestartet: davor stehen **GUI-ERC + die Pinmap-/Power-Konsistenz-Fixes** (das Phase-5-Profiling-Gate ist per ADR-0005 gestrichen, s.u. — alter Stand korrigiert).

## Was fertig ist

### r18.5 (Schematic-Migration)
- 8 Sheets generiert, paren-balanced, 100/100 STM32-Pins angebunden, Hier↔Root-Crossref 7/7 PASS
- STM32H743VIT6-Symbol gegen offizielle KiCad-Lib + DS12110 verifiziert (52/52 belegte Pins)
- Komplette Support-Schaltung (HSE, VCAP, VDD-Bank, VDDA-Filter, BOOT0/NRST, SWD, BAT-Teiler, Status-LED)
- LCD-Sheet mit ST7789 + Backlight-Pfad (PCA9685 → 2N7002)

### r18.6 (Engineering-Verifikation, dieser Commit)
- 🟢 **B-LDO geschlossen**: Symbol/Verdrahtung/Variante auf **AP7361C-33Y5-13** umgestellt — User-verifiziertes SOT-89-5-Pinout (1=EN, 2=GND, 3=ADJ/NC, 4=IN, 5=OUT) aus Diodes-DS via mouser.de/datasheet/3/175/1/AP7361.pdf. Die r18.5-Annahme war FALSCH (hätte IN/OUT/EN vertauscht). LCSC **C460397**. Falsche Kandidatur C150719 verworfen (= SOT-223, falsches Package). Cin/Cout 4.7 µF X5R 0603 (DS-empfohlen).
- 🟢 **B-F1 geschlossen**: TPS61089RNR-Pinout im Symbol stimmt mit TI Pin-Functions Table 6-1 (Rev C) überein (1=FSW, 2=VCC, 3=FB, 4=COMP, 5=GND, 6=VOUT, 7=EN, 8=ILIM, 9=VIN, 10=BOOT, 11=SW). Footprint-Name auf RNR0011A 2.0×2.5 mm VQFN-HR umgestellt. Falsches RNSR-PDF → `datasheets/legacy/`.
- 🟢 **B-F2 teilweise geschlossen**: Encoder ist EC11J1525402, **LCSC C209762** (JLCPCB-verifiziert), SMD 15/30 mit Push-Switch. Status **NRND** (ALPS markiert „Not Recommended for New Designs") — als `Status`-Property + ADR-Hinweis. Prototype-OK, Serie braucht eigene Entscheidung.
- 🟢 **B-SW12 geschlossen**: Custom-Footprint `field_ambience:SW_HX_12x12x7.3_SMD-4P` (`libraries/field_ambience.pretty/`), basierend auf User-verifizierten LCSC-Daten (C36498966: SMD-4P, 11.8×11.8 mm, 7.3 mm Höhe, SPST, 250 gf, 12 V/50 mA, 100 k Zyklen). 5 Symbole jetzt mit korrektem FP. `fp-lib-table` erweitert.
- 🟢 **B-TBD geschlossen**: 4× TBD-VERIFY-Caps gefüllt — VCAP `C24539`, VDD-Bulk `C45783`, HSE-22 pF C0G `C1804`, 2N7002 `C8545`. Alle mit `VERIFY-STOCK`-Property statt blanker LCSC-Nr.
- 🟢 **MIDI geklärt**: nicht „fehlend" sondern OFFENE DESIGN-ENTSCHEIDUNG (5 Achsen) — ADR-0004. Generator-Text-Note im STM32-Sheet aktualisiert.
- 🟢 **ERC/DRC-Checkliste**: `docs/hardware/ERC_DRC_CHECKLIST.md` mit bewussten Warnungen + Manufacturing-Gates.

## Verbleibende Blocker (r18.7: Phase-5-Gate gestrichen)

| # | Sev | Was | Was genau zu tun |
|---|---|---|---|
| B3 | 🟠 | KiCad-GUI-ERC | Einmal in KiCad 9 öffnen, ERC laufen lassen (kicad-cli aktuell nicht in der Umgebung verfügbar). Erwartete Warnungen / verbotene Warnungen siehe ERC_DRC_CHECKLIST.md |
| **SCH-1** | 🟠 | **Power-Aus beim Aufbau einzeichnen** | `U_PWR`+`SW_PWR`+`R_PWR_PD`+`C_PWR_SW`. **Pin-Ebene-Drop-in-Spec in ADR-0016** (VIN/VOUT/ON/Reroute komplett) + `SW_PWR`-Footprint `field_ambience:SW_MST-12D18_SlideSwitch_RA` im Repo. ~10 min einzeichnen + ERC. (Noch nicht im alten Generator.) |
| ~~SCH-2~~ | ✅ | ~~Button SMD→THT~~ | **RESOLVED r18.68:** Generator + `jlc_bom.csv` nutzen jetzt **C2845240 (THT)** + Footprint `field_ambience:SW_TC1212-7.3_THT_4P` (Pads 1,1 = Top-Kante, 2,2 = Bottom-Kante, per HX-Konvention). Pad-Gruppierung bei GUI-ERC bestätigen |
| ~~B-FP~~ | ✅ | ~~Footprint-Land-Pattern-Verifikation~~ | **r18.14: 0 offene Punkte** (EC11J-Blocker via Teil-Retire ADR-0012 gelöst, TS-1088-FP EasyEDA-verifiziert) — Details FP_VERIFY_LOG.md |
| ~~SRC~~ | ✅ | ~~Sourcing-IDs~~ | **Alle 58 LCSC verifiziert, NO-LCSC-Liste leer** (r18.68). MIDI-220Ω=**C22962**, TPS22918=**C131941** (war fälschlich C68913), Button=**C2845240**, Slide=**C49023766**, Header=C124375/C124383 |
| ~~ADR-0004~~ | ✅ | ~~MIDI-Design~~ | **RESOLVED r18.67:** MIDI-Out als 3,5-mm-TRS **J10** implementiert (Type A, 3,3 V/CA-033), im Schaltbild verdrahtet (MIDI_TX/PD5 → 2× 220 Ω → Tip/Ring) |
| Mech | 🟠 | Mechanical Coordinates Update | `../mechanical/coordinates/mechanical_coordinates.md` reflektiert noch Pico-Ära; vor Layout-Start für STM32-LQFP-100 + neue Frontpanel-Komponenten neu fixieren |
| ~~GATE~~ | ~~🔴~~ | ~~Phase-5-Profiling~~ | **ADR-0005: übersprungen** (2026-06-11). Layout darf vor Profiling starten; Firmware-Migration läuft parallel |
| GATE | 🟢 | Phase 6 Layout | nach Gate 2+3 sauber. Stack-Up Sig/GND/+5V/Sig (SPEC §9), JLC-4-Lagen-Profil |

## Verifikations-Log

- 2026-06-11 r18.5: Struktur-Validierung PASS (paren-balance 10/10, 100/100 MCU-Pins, Crossref 7/7)
- 2026-06-11 r18.6: nach LDO-Pinout-Korrektur und Footprint-/MPN-Updates: alle Skript-Checks wiederholt, PASS
- 2026-06-11 r18.9: Cell-FSR-ADC (5 Pins) + 15-LED-Topologie: alle Skript-Checks PASS (100/100 Pins, 15 LEDs, Crossref 7/7)

## Manufacturing-Readiness

Vorher (r18.5): 2.5/10. Jetzt (r18.7): **5.5/10** — Schematic ist nicht nur strukturell, sondern jetzt auch elektrisch verifiziert (LDO-Bestücker-Killer ist weg). Der Weg auf 7: GUI-ERC + Encoder-FP (Custom) + Mechanical-Update. Auf 9-10: Layout + DRC + JLC.
