Sancte3D/AMBIENT/field-ambience-current/kicad/audio.kicad_sch

## KiCad design field-ambience-current/kicad/audio.kicad_sch (2026-07-21)

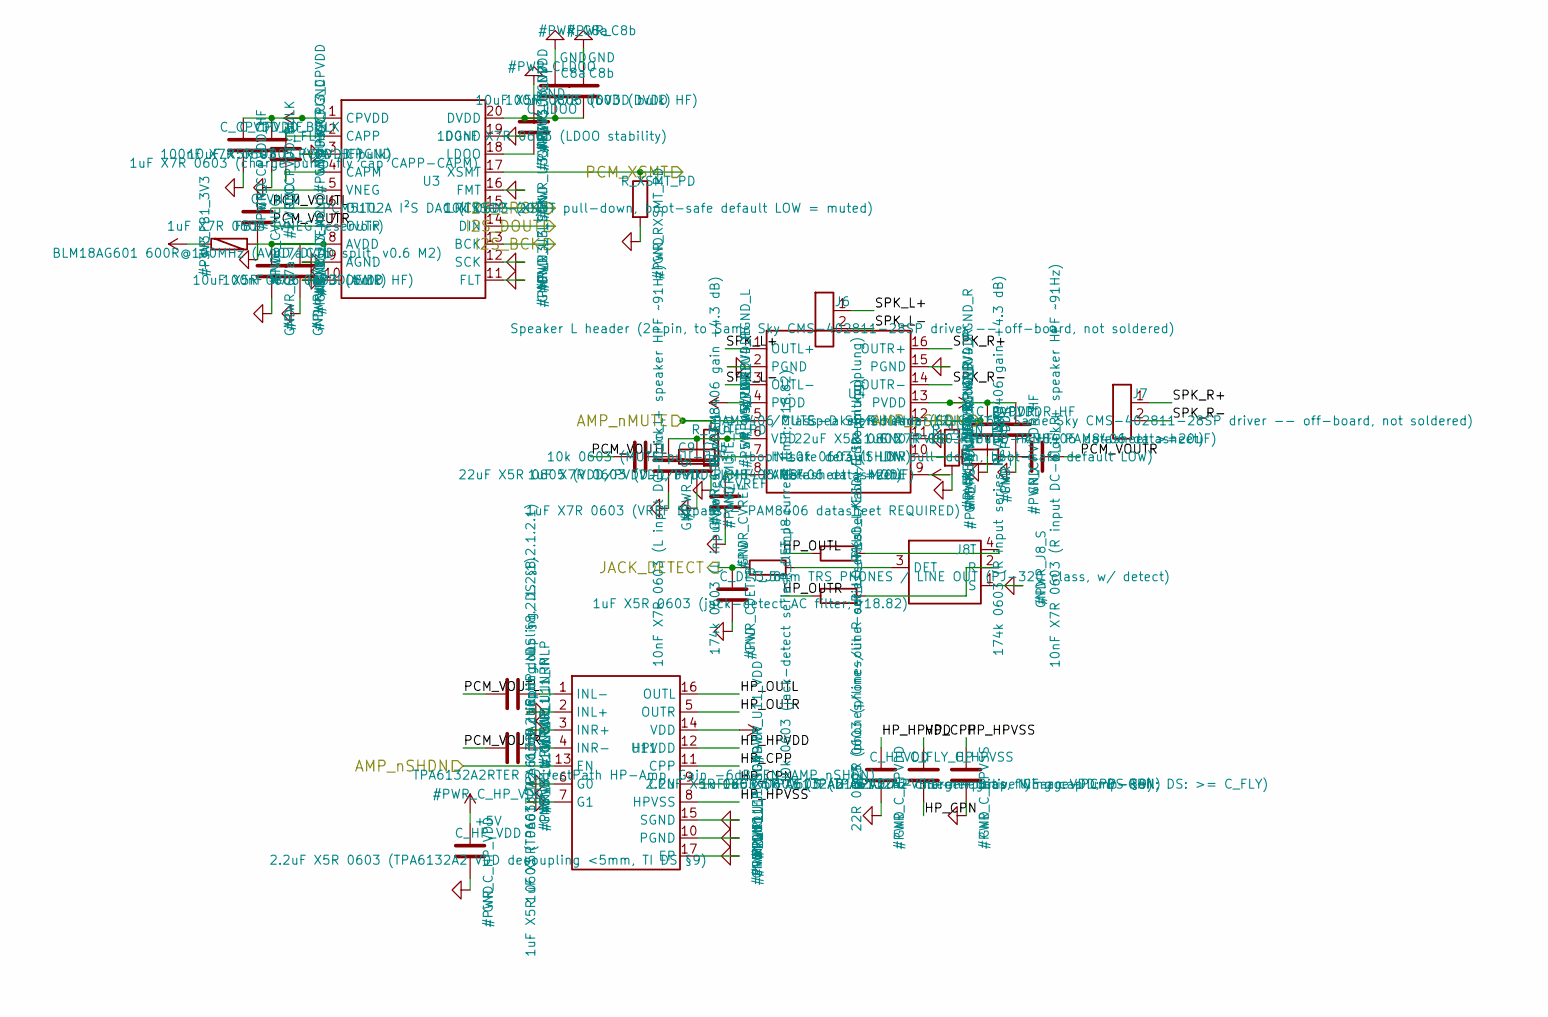
[picture p8: schematic audio.kicad_sch]

Parts:
C7a: 10uF X5R 0805 (AVDD bulk); C_0805_2012Metric; MPN CL21A106KAYNNNE; LCSC C15850
C7b: 100nF X7R 0603 (AVDD HF); C_0603_1608Metric; MPN CC0603KRX7R9BB104; LCSC C14663
C8a: 10uF X5R 0805 (DVDD bulk); C_0805_2012Metric; MPN CL21A106KAYNNNE; LCSC C15850
C8b: 100nF X7R 0603 (DVDD HF); C_0603_1608Metric; MPN CC0603KRX7R9BB104; LCSC C14663
C9: 22uF X5R 0805 (VDD/PVDD-L bulk, PAM8406 datasheet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; C_0805_2012Metric; MPN CL21A226MAQNNNE; LCSC C45783
C9b: 1uF X7R 0603 (VDD/PVDD-L HF, PAM8406 datasheet); C_0603_1608Metric; MPN CL10A105KB8NNNC; LCSC C15849
C_CPVDD_BULK: 10uF X5R 0805 (CPVDD bulk); C_0805_2012Metric; MPN CL21A106KAYNNNE; LCSC C15850
C_CPVDD_HF: 100nF X7R 0603 (CPVDD HF); C_0603_1608Metric; MPN CC0603KRX7R9BB104; LCSC C14663
C_DET_J8: 1uF X5R 0603 (jack-detect AC filter; r18.82); C_0603_1608Metric; MPN CL10A105KB8NNNC; LCSC C15849
C_FLY: 1uF X7R 0603 (charge pump fly cap CAPP-CAPM); C_0603_1608Metric; MPN CL10A105KB8NNNC; LCSC C15849
C_FLY_HP: 1uF X5R 0603 (TPA6132A2 charge-pump flying cap CP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; C_0603_1608Metric; MPN CL10A105KB8NNNC; LCSC C15849
C_HPVDD: 2.2uF X5R 0603 (TPA6132A2 HPVDD — interner Bias, 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; C_0603_1608Metric; MPN CL10A225KP8NNNC; LCSC C1607
C_HPVSS: 1uF X5R 0603 (TPA6132A2 HPVSS — negative Charge-P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; C_0603_1608Metric; MPN CL10A105KB8NNNC; LCSC C15849
C_HP_INL: 1uF X5R 0603 (TPA6132A2 input coupling, DS §8.2.1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; C_0603_1608Metric; MPN CL10A105KB8NNNC; LCSC C15849
C_HP_INR: 1uF X5R 0603 (TPA6132A2 input coupling, DS §8.2.1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; C_0603_1608Metric; MPN CL10A105KB8NNNC; LCSC C15849
C_HP_VDD: 2.2uF X5R 0603 (TPA6132A2 VDD decoupling <5mm, TI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; C_0603_1608Metric; MPN CL10A225KP8NNNC; LCSC C1607
C_LDOO: 100nF X7R 0603 (LDOO stability); C_0603_1608Metric; MPN CC0603KRX7R9BB104; LCSC C14663
C_PVDDR: 22uF X5R 0805 (PVDD-R bulk, PAM8406 datasheet >=2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; C_0805_2012Metric; MPN CL21A226MAQNNNE; LCSC C45783
C_PVDDR_HF: 1uF X7R 0603 (PVDD-R HF, PAM8406 datasheet); C_0603_1608Metric; MPN CL10A105KB8NNNC; LCSC C15849
C_VNEG: 1uF X7R 0603 (VNEG reservoir); C_0603_1608Metric; MPN CL10A105KB8NNNC; LCSC C15849
C_VREF: 1uF X7R 0603 (VREF bypass - PAM8406 datasheet REQ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; C_0603_1608Metric; MPN CL10A105KB8NNNC; LCSC C15849
C_in_L: 10nF X7R 0603 (L input DC-block + speaker HPF ~91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; C_0603_1608Metric; MPN 0603B103K500NT; LCSC C57112
C_in_R: 10nF X7R 0603 (R input DC-block + speaker HPF ~91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; C_0603_1608Metric; MPN 0603B103K500NT; LCSC C57112
FB1: BLM18AG601 600R@100MHz (AVDD/DVDD split, v0.6 M2); L_0603_1608Metric; MPN BLM18AG601SN1D; LCSC C19330
J6: Speaker L header (2-pin, to Same Sky CMS-402811-2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; PinHeader_1x02_P2.54mm_Vertical; MPN 1x2 2.54mm pin header (the on-board con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; LCSC C124375
J7: Speaker R header (2-pin, to Same Sky CMS-402811-2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; PinHeader_1x02_P2.54mm_Vertical; MPN 1x2 2.54mm pin header (the on-board con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; LCSC C124375
J8: 3.5mm TRS PHONES / LINE OUT (PJ-320 class, w/ det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; Jack_3.5mm_PJ-320D_SMT; MPN PJ-320D (3.5mm TRS w/ switch); LCSC C431535
R_DET_J8: 10k 0603 (jack-detect series, clamp-current limit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; R_0603_1608Metric; MPN 0603WAF1002T5E; LCSC C25804
R_LO_L: 22R 0603 (phones/line-out L series — Kabel/ESD-En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; R_0603_1608Metric; MPN 0603WAF220JT5E; LCSC C23345
R_LO_R: 22R 0603 (phones/line-out R series — Kabel/ESD-En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; R_0603_1608Metric; MPN 0603WAF220JT5E; LCSC C23345
R_MUTE_PD: 10k 0603 (MUTE pull-down, boot-safe default LOW); R_0603_1608Metric; MPN 0603WAF1002T5E; LCSC C25804
R_SHDN_PD: 10k 0603 (SHDN pull-down, boot-safe default LOW); R_0603_1608Metric; MPN 0603WAF1002T5E; LCSC C25804
R_VOL_L: 174k 0603 (L input series RI, PAM8406 gain +4.3 d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; R_0603_1608Metric; MPN 0603WAF1743T5E; LCSC C22890
R_VOL_R: 174k 0603 (R input series RI, PAM8406 gain +4.3 d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; R_0603_1608Metric; MPN 0603WAF1743T5E; LCSC C22890
R_XSMT_PD: 10k 0603 (XSMT pull-down, boot-safe default LOW =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; R_0603_1608Metric; MPN 0603WAF1002T5E; LCSC C25804
U3: PCM5102A I²S DAC (TSSOP-20); TSSOP-20_4.4x6.5mm_P0.65mm; MPN PCM5102APWR; LCSC C107671
U4: PAM8406 Class-D Stereo Amp (SOIC-16); SOIC-16_3.9x9.9mm_P1.27mm; MPN PAM8406DR; LCSC C86270
U11: TPA6132A2RTER (DirectPath HP-Amp, Gain -6dB, EN=A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; QFN-16-1EP_3x3mm_P0.5mm_EP1.7x1.7mm; MPN TPA6132A2RTER; LCSC C69901

Connections:
+3V3: C8a.1, C8b.1, C_CPVDD_BULK.1, C_CPVDD_HF.1, FB1.2, U3.1 (CPVDD), U3.20 (DVDD)
+5V: C9.1, C9b.1, C_HP_VDD.1, C_PVDDR.1, C_PVDDR_HF.1, U4.4 (PVDD), U4.6 (VDD), U4.9 (MODE), U4.13 (PVDD), U11.14 (VDD)
AMP_nMUTE: R_MUTE_PD.1, U4.5 (/MUTE)
AMP_nSHDN: R_SHDN_PD.1, U4.12 (/SHDN), U11.13 (EN)
GND: C7a.2, C7b.2, C8a.2, C8b.2, C9.2, C9b.2, C_CPVDD_BULK.2, C_CPVDD_HF.2, C_DET_J8.2, C_HPVDD.2, C_HPVSS.2, C_HP_VDD.2, C_LDOO.2, C_PVDDR.2, C_PVDDR_HF.2, C_VNEG.2, C_VREF.2, J8.1 (S), R_MUTE_PD.2, R_SHDN_PD.2, R_XSMT_PD.2, U3.3 (CPGND), U3.9 (AGND), U3.10 (DEMP), U3.11 (FLT), U3.12 (SCK), U3.16 (FMT), U3.19 (DGND), U4.2 (PGND), U4.11 (GND), U4.15 (PGND), U11.2 (INL+), U11.3 (INR+), U11.6 (G0), U11.7 (G1), U11.10 (PGND), U11.15 (SGND), U11.17 (EP)
HP_CPN: C_FLY_HP.2, U11.9 (CPN)
HP_CPP: C_FLY_HP.1, U11.11 (CPP)
HP_HPVDD: C_HPVDD.1, U11.12 (HPVDD)
HP_HPVSS: C_HPVSS.1, U11.8 (HPVSS)
HP_OUTL: R_LO_L.1, U11.16 (OUTL)
HP_OUTR: R_LO_R.1, U11.5 (OUTR)
I2S_BCK: U3.13 (BCK)
I2S_DOUT: U3.14 (DIN)
I2S_LRCK: U3.15 (LRCK)
JACK_DETECT: C_DET_J8.1, R_DET_J8.1
unnamed: C7a.1, C7b.1, FB1.1, U3.8 (AVDD)
unnamed: C_FLY.1, U3.2 (CAPP)
unnamed: C_FLY.2, U3.4 (CAPM)
unnamed: C_HP_INL.2, U11.1 (INL-)
unnamed: C_HP_INR.2, U11.4 (INR-)
unnamed: C_LDOO.1, U3.18 (LDOO)
unnamed: C_VNEG.1, U3.5 (VNEG)
unnamed: C_VREF.1, U4.8 (VREF)
unnamed: C_in_L.2, R_VOL_L.1
unnamed: C_in_R.1, R_VOL_R.2
unnamed: J8.2 (R), R_LO_R.2
unnamed: J8.3 (DET), R_DET_J8.2
unnamed: J8.4 (T), R_LO_L.2
unnamed: R_VOL_L.2, U4.7 (INL)
unnamed: R_VOL_R.1, U4.10 (INR)
PCM_VOUTL: C_HP_INL.1, C_in_L.1, U3.6 (OUTL)
PCM_VOUTR: C_HP_INR.1, C_in_R.2, U3.7 (OUTR)
PCM_XSMT: R_XSMT_PD.1, U3.17 (XSMT)
SPK_L+: J6.1, U4.1 (OUTL+)
SPK_L-: J6.2, U4.3 (OUTL-)
SPK_R+: J7.1, U4.16 (OUTR+)
SPK_R-: J7.2, U4.14 (OUTR-)
