Sancte3D/AMBIENT/field-ambience-current/kicad/battery.kicad_sch

## KiCad design field-ambience-current/kicad/battery.kicad_sch (2026-07-21)

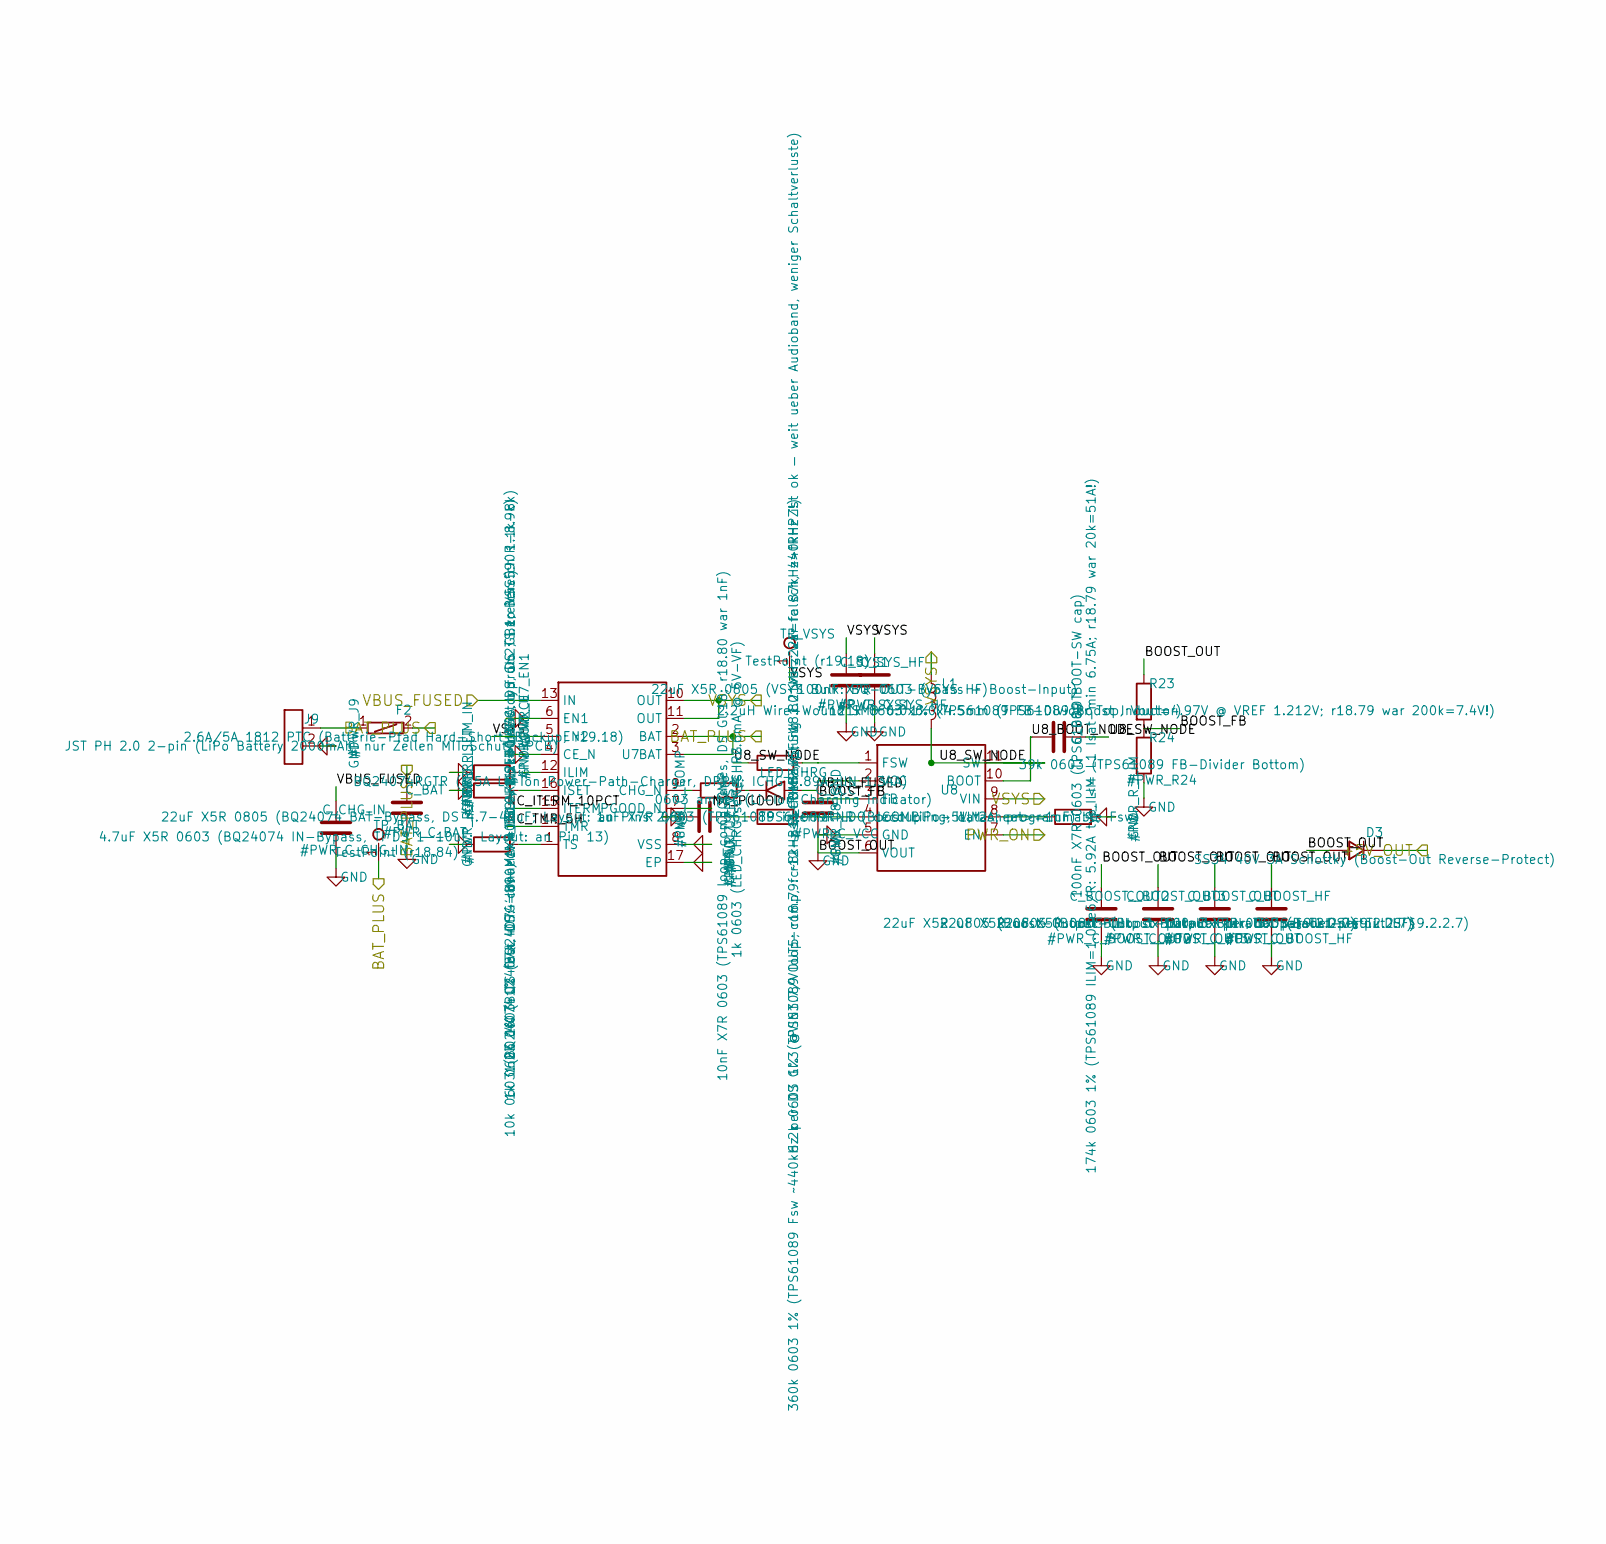
[picture p9: schematic battery.kicad_sch]

Parts:
C_BAT: 22uF X5R 0805 (BQ24074 BAT-Bypass, DS 4.7-47uF; L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; C_0805_2012Metric; MPN CL21A226MAQNNNE; LCSC C45783
C_BOOST_HF: 100nF X7R 0603 (Boost-Output HF); C_0603_1608Metric; MPN CC0603KRX7R9BB104; LCSC C14663
C_BOOST_OUT, C_BOOST_OUT2, C_BOOST_OUT3: 22uF X5R 0805 (Boost-Output Bulk, 3x parallel per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; C_0805_2012Metric; MPN CL21A226MAQNNNE; LCSC C45783
C_BOOT: 100nF X7R 0603 (TPS61089 BOOT-SW cap); C_0603_1608Metric; MPN CC0603KRX7R9BB104; LCSC C14663
C_CHG_IN: 4.7uF X5R 0603 (BQ24074 IN-Bypass, TI DS 1-10uF; 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; C_0603_1608Metric; MPN GRM188R61A475KE15D; LCSC C46653
C_COMP: 10nF X7R 0603 (TPS61089 loop-comp series, DS Gl.1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; C_0603_1608Metric; MPN 0603B103K500NT; LCSC C57112
C_SYS1: 22uF X5R 0805 (VSYS Bulk: BQ-OUT-Bypass + Boost-I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; C_0805_2012Metric; MPN CL21A226MAQNNNE; LCSC C45783
C_SYS_HF: 100nF X7R 0603 (VSYS HF); C_0603_1608Metric; MPN CC0603KRX7R9BB104; LCSC C14663
C_VCC: 1uF X7R 0603 (TPS61089 internal LDO decoupling, d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; C_0603_1608Metric; MPN CL10A105KB8NNNC; LCSC C15849
D3: SS34 40V 3A Schottky (Boost-Out Reverse-Protect); D_SMA; MPN SS34; LCSC C8678
F2: 2.6A/5A 1812 PTC (Batterie-Pfad Hard-Short-Backup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; Fuse_1812_4532Metric; MPN SMD1812P260TF/16; LCSC C438899
J9: JST PH 2.0 2-pin (LiPo Battery 2000mAh, nur Zelle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; JST_PH_S2B-PH-SM4-TB_1x02-1MP_P2.00mm_Horizontal; MPN S2B-PH-SM4-TB(LF)(SN); LCSC C295747
L1: 2.2uH Wire-Wound SMD 6.0x6.0x4.5mm (TPS61089 Boos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; L_Sunlord_SWPA6045; MPN SWPA6045S2R2NT; LCSC C36500
LED_CHRG: 0603 amber (Li-Ion Charging indicator); LED_0603_1608Metric; MPN XL-1608UOC-06; LCSC C965800
R23: 121k 0603 1% (TPS61089 FB-Divider Top, Vout=4.97V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; R_0603_1608Metric; MPN 0603WAF1213T5E; LCSC C25809
R24: 39k 0603 (TPS61089 FB-Divider Bottom); R_0603_1608Metric; MPN 0603WAF3902T5E; LCSC C23153
R_CHRG: 1k 0603 (LED_CHRG series, ~2.6mA @ 5V-VF); R_0603_1608Metric; MPN 0603WAF1001T5E; LCSC C21190
R_COMP: 6.2k 0603 1% (TPS61089 loop-comp, fc~8kHz<=fRHPZ/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; R_0603_1608Metric; MPN 0603WAF6201T5E; LCSC C4260
R_FSW: 360k 0603 1% (TPS61089 Fsw ~440kHz per DS Gl.3 @V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; R_0603_1608Metric; MPN 0603WAF3603T5E; LCSC C23146
R_ILIM: 174k 0603 1% (TPS61089 ILIM=1.03e6/R: 5.92A typ, 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; R_0603_1608Metric; MPN 0603WAF1743T5E; LCSC C22890
R_ILIM_IN: 1.2k 0603 1% (BQ24074 IIN-MAX=1610/1.2k=1.34A typ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; R_0603_1608Metric; MPN RC0603FR-071K2L; LCSC C114605
R_ISET: 1k 0603 1% (BQ24074 ICHG=890/1k=0.89A typ ≈0.45C,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; R_0603_1608Metric; MPN 0603WAF1001T5E; LCSC C21190
R_TS: 10k 0603 (BQ24074 TS fest, DS: 'connect a 10-k fi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; R_0603_1608Metric; MPN 0603WAF1002T5E; LCSC C25804
TP_BAT: TestPoint (r18.84); TestPoint_Pad_D1.5mm
TP_VSYS: TestPoint (r19.18); TestPoint_Pad_D1.5mm
U7: BQ24074RGTR (1.5A Li-Ion Power-Path-Charger, DPPM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; QFN-16-1EP_3x3mm_P0.5mm_EP1.7x1.7mm; MPN BQ24074RGTR; LCSC C54313
U8: TPS61089RNR (Boost LiPo→5V, 2A, programmable Fsw); Texas_VQFN-HR-11_2x2.5mm_P0.5mm_RNR0011A; MPN TPS61089RNR; LCSC C165129

Connections:
+5V_OUT: D3.1 (K)
BAT_PLUS: C_BAT.1, F2.2, TP_BAT.1, U7.2 (BAT), U7.3 (BAT)
BOOST_FB: R23.2, R24.1, U8.3 (FB)
BOOST_OUT: C_BOOST_HF.1, C_BOOST_OUT.1, C_BOOST_OUT2.1, C_BOOST_OUT3.1, D3.2 (A), R23.1, U8.6 (VOUT)
GND: C_BAT.2, C_BOOST_HF.2, C_BOOST_OUT.2, C_BOOST_OUT2.2, C_BOOST_OUT3.2, C_CHG_IN.2, C_COMP.1, C_SYS1.2, C_SYS_HF.2, C_VCC.2, J9.2, R24.2, R_ILIM.2, R_ILIM_IN.1, R_ISET.1, R_TS.1, U7.4 (CE_N), U7.6 (EN1), U7.8 (VSS), U7.17 (EP), U8.5 (GND)
NC_ITERM_10PCT: U7.15 (ITERM)
NC_PGOOD: U7.7 (PGOOD_N)
NC_TMR_5H: U7.14 (TMR)
unnamed: C_COMP.2, R_COMP.1
unnamed: C_VCC.1, U8.2 (VCC)
unnamed: F2.1, J9.1
unnamed: LED_CHRG.1 (K), R_CHRG.2
unnamed: R_CHRG.1, U7.9 (CHG_N)
unnamed: R_COMP.2, U8.4 (COMP)
unnamed: R_FSW.2, U8.1 (FSW)
unnamed: R_ILIM.1, U8.8 (ILIM)
unnamed: R_ILIM_IN.2, U7.12 (ILIM)
unnamed: R_ISET.2, U7.16 (ISET)
unnamed: R_TS.2, U7.1 (TS)
PWR_ON: U8.7 (EN)
U8_BOOT_NODE: C_BOOT.1, U8.10 (BOOT)
U8_SW_NODE: C_BOOT.2, L1.2, R_FSW.1, U8.11 (SW)
VBUS_FUSED: C_CHG_IN.1, LED_CHRG.2 (A), U7.13 (IN)
VSYS: C_SYS1.1, C_SYS_HF.1, L1.1, TP_VSYS.1, U7.5 (EN2), U7.10 (OUT), U7.11 (OUT), U8.9 (VIN)
