Sancte3D/AMBIENT/field-ambience-current/kicad/encoder.kicad_sch

## KiCad design field-ambience-current/kicad/encoder.kicad_sch (2026-07-21)

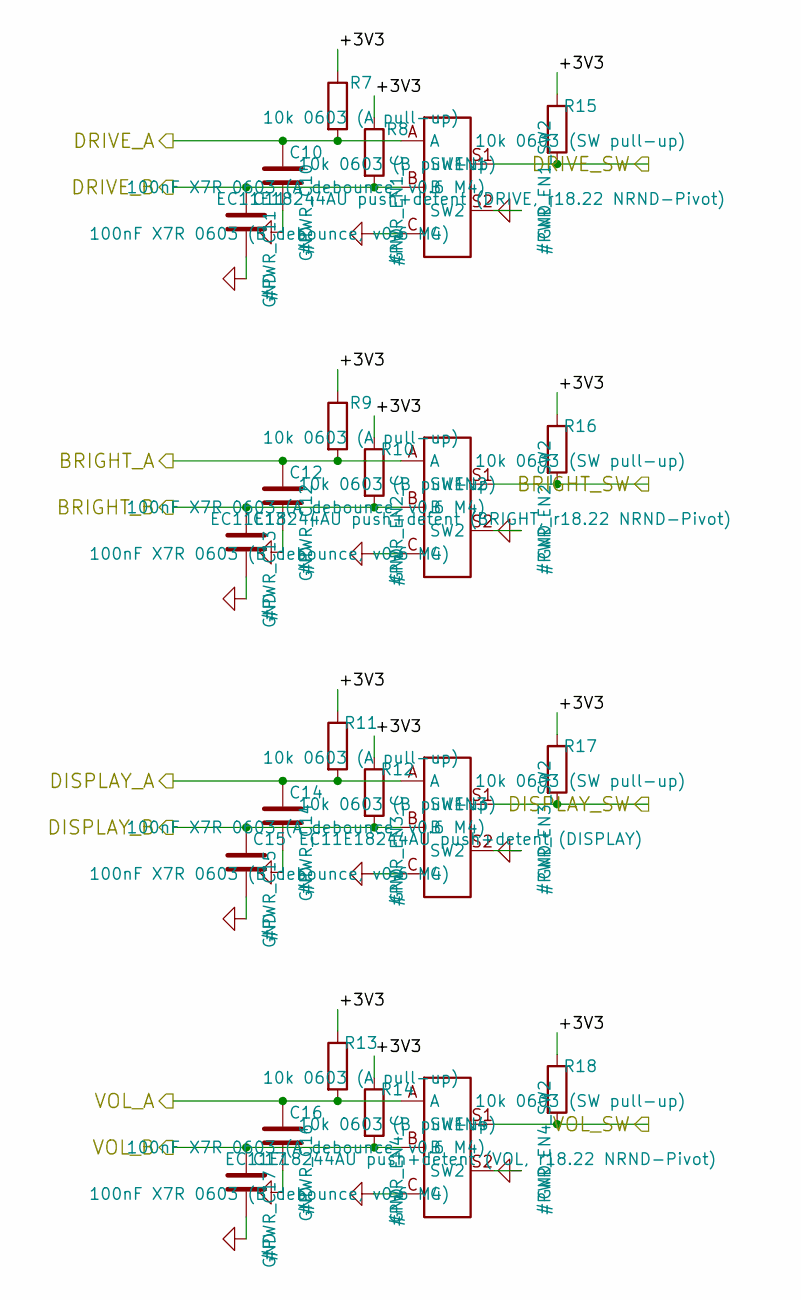
[picture p10: schematic encoder.kicad_sch]

Parts:
C10, C12, C14, C16: 100nF X7R 0603 (A debounce, v0.6 M4); C_0603_1608Metric; MPN CC0603KRX7R9BB104; LCSC C14663
C11, C13, C15, C17: 100nF X7R 0603 (B debounce, v0.6 M4); C_0603_1608Metric; MPN CC0603KRX7R9BB104; LCSC C14663
EN1: EC11E18244AU push+detent (DRIVE, r18.22 NRND-Pivo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; RotaryEncoder_Alps_EC11E-Switch_Vertical_H20mm; MPN EC11E18244AU (ALPS EC11E, 18 Pulse, 36 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; LCSC C202365
EN2: EC11E18244AU push+detent (BRIGHT, r18.22 NRND-Piv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; RotaryEncoder_Alps_EC11E-Switch_Vertical_H20mm; MPN EC11E18244AU (ALPS EC11E, 18 Pulse, 36 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; LCSC C202365
EN3: EC11E18244AU push+detent (DISPLAY); RotaryEncoder_Alps_EC11E-Switch_Vertical_H20mm; MPN EC11E18244AU (ALPS EC11E, 18 Pulse, 36 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; LCSC C202365
EN4: EC11E18244AU push+detent (VOL, r18.22 NRND-Pivot); RotaryEncoder_Alps_EC11E-Switch_Vertical_H20mm; MPN EC11E18244AU (ALPS EC11E, 18 Pulse, 36 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; LCSC C202365
R7, R9, R11, R13: 10k 0603 (A pull-up); R_0603_1608Metric; MPN 0603WAF1002T5E; LCSC C25804
R8, R10, R12, R14: 10k 0603 (B pull-up); R_0603_1608Metric; MPN 0603WAF1002T5E; LCSC C25804
R15, R16, R17, R18: 10k 0603 (SW pull-up); R_0603_1608Metric; MPN 0603WAF1002T5E; LCSC C25804

Connections:
+3V3: R7.1, R8.1, R9.1, R10.1, R11.1, R12.1, R13.1, R14.1, R15.1, R16.1, R17.1, R18.1
BRIGHT_A: C12.1, EN2.A, R9.2
BRIGHT_B: C13.1, EN2.B, R10.2
BRIGHT_SW: EN2.S1 (SW1), R16.2
DISPLAY_A: C14.1, EN3.A, R11.2
DISPLAY_B: C15.1, EN3.B, R12.2
DISPLAY_SW: EN3.S1 (SW1), R17.2
DRIVE_A: C10.1, EN1.A, R7.2
DRIVE_B: C11.1, EN1.B, R8.2
DRIVE_SW: EN1.S1 (SW1), R15.2
GND: C10.2, C11.2, C12.2, C13.2, C14.2, C15.2, C16.2, C17.2, EN1.C, EN1.S2 (SW2), EN2.C, EN2.S2 (SW2), EN3.C, EN3.S2 (SW2), EN4.C, EN4.S2 (SW2)
VOL_A: C16.1, EN4.A, R13.2
VOL_B: C17.1, EN4.B, R14.2
VOL_SW: EN4.S1 (SW1), R18.2
