Sancte3D/AMBIENT/field-ambience-current/kicad/lcd.kicad_sch

## KiCad design field-ambience-current/kicad/lcd.kicad_sch (2026-07-21)

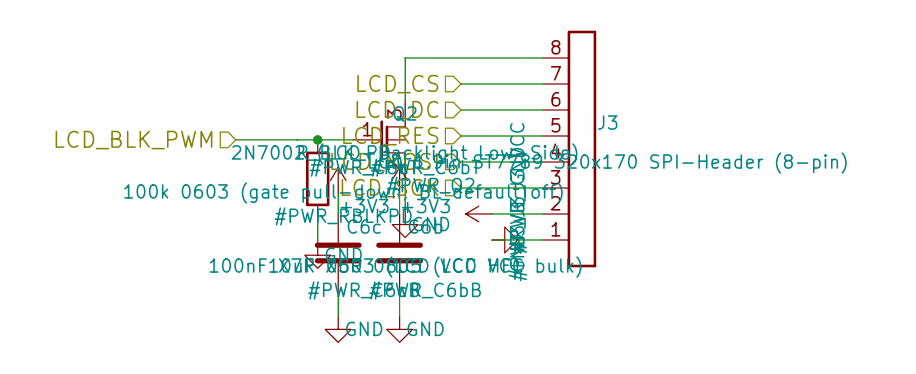
[picture p11: schematic lcd.kicad_sch]

Parts:
C6b: 10uF X5R 0805 (LCD VCC bulk); C_0805_2012Metric; MPN CL21A106KAYNNNE; LCSC C15850
C6c: 100nF X7R 0603 (LCD VCC HF); C_0603_1608Metric; MPN CC0603KRX7R9BB104; LCSC C14663
J3: LCD 1.9in ST7789 320x170 SPI-Header (8-pin); PinHeader_1x08_P2.54mm_Vertical; MPN 1x8 2.54mm pin header (the on-board con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; LCSC C124383
Q2: 2N7002 (LCD-Backlight Low-Side); SOT-23; MPN 2N7002,215; LCSC C8545
R_BLK_PD: 100k 0603 (gate pull-down, BL default off); R_0603_1608Metric; MPN 0603WAF1002T5E; LCSC C25804

Connections:
+3V3: C6b.1, C6c.1, J3.2
GND: C6b.2, C6c.2, J3.1, Q2.2 (S), R_BLK_PD.2
LCD_BLK_PWM: Q2.1 (G), R_BLK_PD.1
LCD_CS: J3.7
LCD_DC: J3.6
LCD_MOSI: J3.4
LCD_RES: J3.5
LCD_SCK: J3.3
unnamed: J3.8, Q2.3 (D)
