Sancte3D/AMBIENT/field-ambience-current/kicad/mcp.kicad_sch

## KiCad design field-ambience-current/kicad/mcp.kicad_sch (2026-07-21)

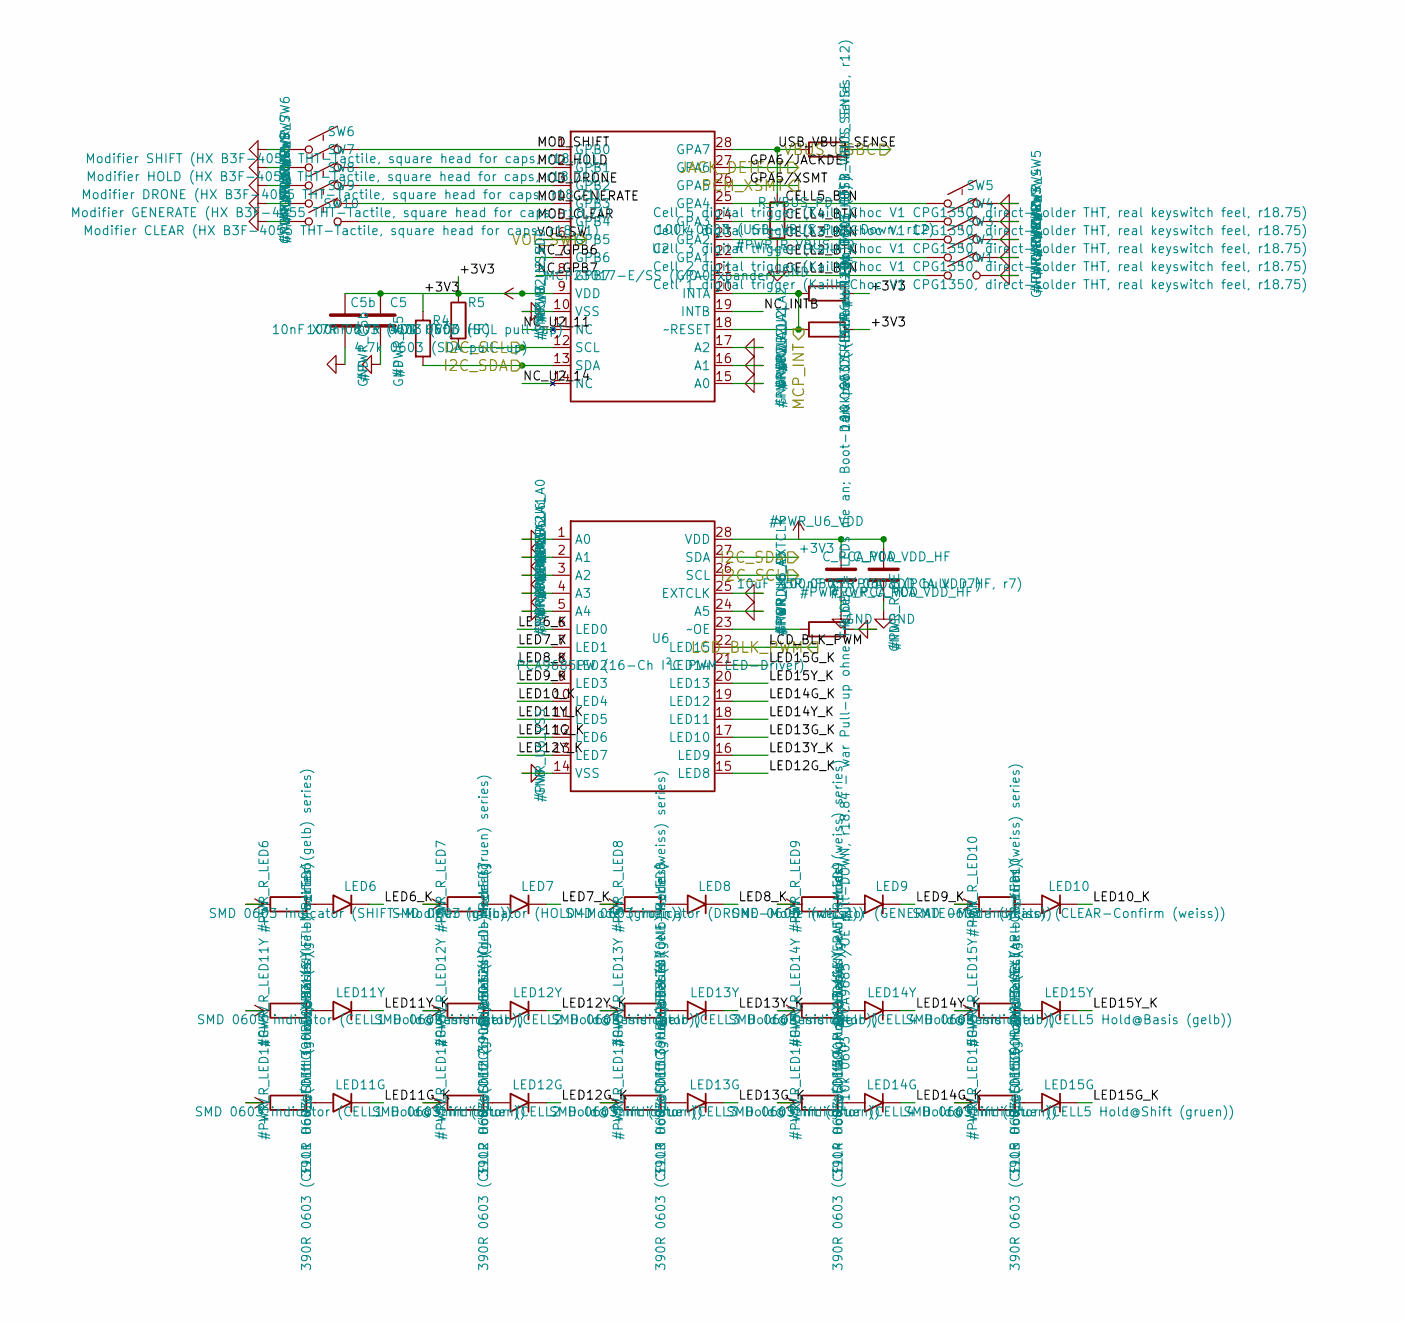
[picture p12: schematic mcp.kicad_sch]

Parts:
C5: 100nF X7R 0603 (VDD HF); C_0603_1608Metric; MPN CC0603KRX7R9BB104; LCSC C14663
C5b: 10nF X7R 0603 (VDD HF²); C_0603_1608Metric; MPN 0603B103K500NT; LCSC C57112
C_PCA_VDD: 10uF X5R 0805 (PCA VDD bulk, r7); C_0805_2012Metric; MPN CL21A106KAYNNNE; LCSC C15850
C_PCA_VDD_HF: 100nF X7R 0603 (PCA VDD HF, r7); C_0603_1608Metric; MPN CC0603KRX7R9BB104; LCSC C14663
LED6: SMD 0603 indicator (SHIFT-Modifier (gelb)); LED_0603_1608Metric; MPN KT-0603Y (Hubei KENTO, yellow 0603, Vf 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; LCSC C2287
LED7: SMD 0603 indicator (HOLD-Mode (gruen)); LED_0603_1608Metric; MPN KT-0603G (Hubei KENTO, pure green 525nm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; LCSC C12624
LED8: SMD 0603 indicator (DRONE-Mode (weiss)); LED_0603_1608Metric; MPN XL-1608UWC-04 (warm-white 0603); LCSC C965808
LED9: SMD 0603 indicator (GENERATE-Mode (weiss)); LED_0603_1608Metric; MPN XL-1608UWC-04 (warm-white 0603); LCSC C965808
LED10: SMD 0603 indicator (CLEAR-Confirm (weiss)); LED_0603_1608Metric; MPN XL-1608UWC-04 (warm-white 0603); LCSC C965808
LED11G: SMD 0603 indicator (CELL1 Hold@Shift (gruen)); LED_0603_1608Metric; MPN KT-0603G (Hubei KENTO, pure green 525nm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; LCSC C12624
LED11Y: SMD 0603 indicator (CELL1 Hold@Basis (gelb)); LED_0603_1608Metric; MPN KT-0603Y (Hubei KENTO, yellow 0603, Vf 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; LCSC C2287
LED12G: SMD 0603 indicator (CELL2 Hold@Shift (gruen)); LED_0603_1608Metric; MPN KT-0603G (Hubei KENTO, pure green 525nm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; LCSC C12624
LED12Y: SMD 0603 indicator (CELL2 Hold@Basis (gelb)); LED_0603_1608Metric; MPN KT-0603Y (Hubei KENTO, yellow 0603, Vf 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; LCSC C2287
LED13G: SMD 0603 indicator (CELL3 Hold@Shift (gruen)); LED_0603_1608Metric; MPN KT-0603G (Hubei KENTO, pure green 525nm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; LCSC C12624
LED13Y: SMD 0603 indicator (CELL3 Hold@Basis (gelb)); LED_0603_1608Metric; MPN KT-0603Y (Hubei KENTO, yellow 0603, Vf 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; LCSC C2287
LED14G: SMD 0603 indicator (CELL4 Hold@Shift (gruen)); LED_0603_1608Metric; MPN KT-0603G (Hubei KENTO, pure green 525nm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; LCSC C12624
LED14Y: SMD 0603 indicator (CELL4 Hold@Basis (gelb)); LED_0603_1608Metric; MPN KT-0603Y (Hubei KENTO, yellow 0603, Vf 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; LCSC C2287
LED15G: SMD 0603 indicator (CELL5 Hold@Shift (gruen)); LED_0603_1608Metric; MPN KT-0603G (Hubei KENTO, pure green 525nm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; LCSC C12624
LED15Y: SMD 0603 indicator (CELL5 Hold@Basis (gelb)); LED_0603_1608Metric; MPN KT-0603Y (Hubei KENTO, yellow 0603, Vf 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; LCSC C2287
R4: 4.7k 0603 (SDA pull-up); R_0603_1608Metric; MPN 0603WAF4701T5E; LCSC C23162
R5: 4.7k 0603 (SCL pull-up); R_0603_1608Metric; MPN 0603WAF4701T5E; LCSC C23162
R6: 10k 0603 (RESET pull-up); R_0603_1608Metric; MPN 0603WAF1002T5E; LCSC C25804
R20: 10k 0603 (INTA pull-up, v0.6 H3); R_0603_1608Metric; MPN 0603WAF1002T5E; LCSC C25804
R_LED6: 390R 0603 (SHIFT-Modifier (gelb) series); R_0603_1608Metric; MPN 0603WAF3900T5E; LCSC C23151
R_LED7: 390R 0603 (HOLD-Mode (gruen) series); R_0603_1608Metric; MPN 0603WAF3900T5E; LCSC C23151
R_LED8: 390R 0603 (DRONE-Mode (weiss) series); R_0603_1608Metric; MPN 0603WAF3900T5E; LCSC C23151
R_LED9: 390R 0603 (GENERATE-Mode (weiss) series); R_0603_1608Metric; MPN 0603WAF3900T5E; LCSC C23151
R_LED10: 390R 0603 (CLEAR-Confirm (weiss) series); R_0603_1608Metric; MPN 0603WAF3900T5E; LCSC C23151
R_LED11G: 390R 0603 (CELL1 Hold@Shift (gruen) series); R_0603_1608Metric; MPN 0603WAF3900T5E; LCSC C23151
R_LED11Y: 390R 0603 (CELL1 Hold@Basis (gelb) series); R_0603_1608Metric; MPN 0603WAF3900T5E; LCSC C23151
R_LED12G: 390R 0603 (CELL2 Hold@Shift (gruen) series); R_0603_1608Metric; MPN 0603WAF3900T5E; LCSC C23151
R_LED12Y: 390R 0603 (CELL2 Hold@Basis (gelb) series); R_0603_1608Metric; MPN 0603WAF3900T5E; LCSC C23151
R_LED13G: 390R 0603 (CELL3 Hold@Shift (gruen) series); R_0603_1608Metric; MPN 0603WAF3900T5E; LCSC C23151
R_LED13Y: 390R 0603 (CELL3 Hold@Basis (gelb) series); R_0603_1608Metric; MPN 0603WAF3900T5E; LCSC C23151
R_LED14G: 390R 0603 (CELL4 Hold@Shift (gruen) series); R_0603_1608Metric; MPN 0603WAF3900T5E; LCSC C23151
R_LED14Y: 390R 0603 (CELL4 Hold@Basis (gelb) series); R_0603_1608Metric; MPN 0603WAF3900T5E; LCSC C23151
R_LED15G: 390R 0603 (CELL5 Hold@Shift (gruen) series); R_0603_1608Metric; MPN 0603WAF3900T5E; LCSC C23151
R_LED15Y: 390R 0603 (CELL5 Hold@Basis (gelb) series); R_0603_1608Metric; MPN 0603WAF3900T5E; LCSC C23151
R_OE: 10k 0603 (PCA9685 /OE pull-DOWN, r18.84 — war Pul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; R_0603_1608Metric; MPN 0603WAF1002T5E; LCSC C25804
R_VBUS_PD: 100k 0603 (USB-VBUS Pull-Down, r12); R_0603_1608Metric; MPN 0603WAF1003T5E; LCSC C25803
R_VBUS_SENSE: 10k 0603 (USB-VBUS Series, r12); R_0603_1608Metric; MPN 0603WAF1002T5E; LCSC C25804
SW1: Cell 1 digital trigger (Kailh Choc V1 CPG1350, di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; SW_KailhChoc_CPG1350_THT_2P; MPN CPG135001D01 (Kailh Choc V1, red/linear); LCSC C400229
SW2: Cell 2 digital trigger (Kailh Choc V1 CPG1350, di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; SW_KailhChoc_CPG1350_THT_2P; MPN CPG135001D01 (Kailh Choc V1, red/linear); LCSC C400229
SW3: Cell 3 digital trigger (Kailh Choc V1 CPG1350, di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; SW_KailhChoc_CPG1350_THT_2P; MPN CPG135001D01 (Kailh Choc V1, red/linear); LCSC C400229
SW4: Cell 4 digital trigger (Kailh Choc V1 CPG1350, di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; SW_KailhChoc_CPG1350_THT_2P; MPN CPG135001D01 (Kailh Choc V1, red/linear); LCSC C400229
SW5: Cell 5 digital trigger (Kailh Choc V1 CPG1350, di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; SW_KailhChoc_CPG1350_THT_2P; MPN CPG135001D01 (Kailh Choc V1, red/linear); LCSC C400229
SW6: Modifier SHIFT (HX B3F-4055 THT-Tactile, square h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; SW_TC1212-7.3_THT_4P; MPN HX B3F-4055-Y; LCSC C36498965
SW7: Modifier HOLD (HX B3F-4055 THT-Tactile, square he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; SW_TC1212-7.3_THT_4P; MPN HX B3F-4055-Y; LCSC C36498965
SW8: Modifier DRONE (HX B3F-4055 THT-Tactile, square h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; SW_TC1212-7.3_THT_4P; MPN HX B3F-4055-Y; LCSC C36498965
SW9: Modifier GENERATE (HX B3F-4055 THT-Tactile, squar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; SW_TC1212-7.3_THT_4P; MPN HX B3F-4055-Y; LCSC C36498965
SW10: Modifier CLEAR (HX B3F-4055 THT-Tactile, square h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; SW_TC1212-7.3_THT_4P; MPN HX B3F-4055-Y; LCSC C36498965
U2: MCP23017-E/SS (I/O-Expander); SSOP-28_5.3x10.2mm_P0.65mm; MPN MCP23017-E/SS; LCSC C506653
U6: PCA9685PW (16-Ch I²C PWM LED-Driver); TSSOP-28_4.4x9.7mm_P0.65mm; MPN PCA9685PW,118; LCSC C2678753

Connections:
+3V3: C5.1, C5b.1, C_PCA_VDD.1, C_PCA_VDD_HF.1, R4.1, R5.1, R6.2, R20.2, U2.9 (VDD), U6.28 (VDD)
+5V: R_LED6.1, R_LED7.1, R_LED8.1, R_LED9.1, R_LED10.1, R_LED11G.1, R_LED11Y.1, R_LED12G.1, R_LED12Y.1, R_LED13G.1, R_LED13Y.1, R_LED14G.1, R_LED14Y.1, R_LED15G.1, R_LED15Y.1
CELL1_BTN: SW1.1, U2.21 (GPA0)
CELL2_BTN: SW2.1, U2.22 (GPA1)
CELL3_BTN: SW3.1, U2.23 (GPA2)
CELL4_BTN: SW4.1, U2.24 (GPA3)
CELL5_BTN: SW5.1, U2.25 (GPA4)
GND: C5.2, C5b.2, C_PCA_VDD.2, C_PCA_VDD_HF.2, R_OE.2, R_VBUS_PD.2, SW1.2, SW2.2, SW3.2, SW4.2, SW5.2, SW6.1, SW7.1, SW8.1, SW9.1, SW10.1, U2.10 (VSS), U2.15 (A0), U2.16 (A1), U2.17 (A2), U6.1 (A0), U6.2 (A1), U6.3 (A2), U6.4 (A3), U6.5 (A4), U6.14 (VSS), U6.24 (A5), U6.25 (EXTCLK)
GPA5/XSMT: U2.26 (GPA5)
GPA6/JACKDET: U2.27 (GPA6)
I2C_SCL: R5.2, U2.12 (SCL), U6.26 (SCL)
I2C_SDA: R4.2, U2.13 (SDA), U6.27 (SDA)
LCD_BLK_PWM: U6.22 (LED15)
LED6_K: LED6.1 (K), U6.6 (LED0)
LED7_K: LED7.1 (K), U6.7 (LED1)
LED8_K: LED8.1 (K), U6.8 (LED2)
LED9_K: LED9.1 (K), U6.9 (LED3)
LED10_K: LED10.1 (K), U6.10 (LED4)
LED11G_K: LED11G.1 (K), U6.12 (LED6)
LED11Y_K: LED11Y.1 (K), U6.11 (LED5)
LED12G_K: LED12G.1 (K), U6.15 (LED8)
LED12Y_K: LED12Y.1 (K), U6.13 (LED7)
LED13G_K: LED13G.1 (K), U6.17 (LED10)
LED13Y_K: LED13Y.1 (K), U6.16 (LED9)
LED14G_K: LED14G.1 (K), U6.19 (LED12)
LED14Y_K: LED14Y.1 (K), U6.18 (LED11)
LED15G_K: LED15G.1 (K), U6.21 (LED14)
LED15Y_K: LED15Y.1 (K), U6.20 (LED13)
MCP_INT: R20.1, U2.20 (INTA)
MOD_CLEAR: SW10.2, U2.5 (GPB4)
MOD_DRONE: SW8.2, U2.3 (GPB2)
MOD_GENERATE: SW9.2, U2.4 (GPB3)
MOD_HOLD: SW7.2, U2.2 (GPB1)
MOD_SHIFT: SW6.2, U2.1 (GPB0)
NC_GPB6: U2.7 (GPB6)
NC_GPB7: U2.8 (GPB7)
NC_INTB: U2.19 (INTB)
NC_U2_11: U2.11 (NC)
NC_U2_14: U2.14 (NC)
unnamed: LED6.2 (A), R_LED6.2
unnamed: LED7.2 (A), R_LED7.2
unnamed: LED8.2 (A), R_LED8.2
unnamed: LED9.2 (A), R_LED9.2
unnamed: LED10.2 (A), R_LED10.2
unnamed: LED11G.2 (A), R_LED11G.2
unnamed: LED11Y.2 (A), R_LED11Y.2
unnamed: LED12G.2 (A), R_LED12G.2
unnamed: LED12Y.2 (A), R_LED12Y.2
unnamed: LED13G.2 (A), R_LED13G.2
unnamed: LED13Y.2 (A), R_LED13Y.2
unnamed: LED14G.2 (A), R_LED14G.2
unnamed: LED14Y.2 (A), R_LED14Y.2
unnamed: LED15G.2 (A), R_LED15G.2
unnamed: LED15Y.2 (A), R_LED15Y.2
unnamed: R6.1, U2.18 (~RESET)
unnamed: R_OE.1, U6.23 (~OE)
USB_VBUS_SENSE: R_VBUS_PD.1, R_VBUS_SENSE.1, U2.28 (GPA7)
VBUS_USBC: R_VBUS_SENSE.2
VOL_SW: U2.6 (GPB5)
