Sancte3D/AMBIENT/field-ambience-current/kicad/power_tree.kicad_sch

## KiCad design field-ambience-current/kicad/power_tree.kicad_sch (2026-07-21)

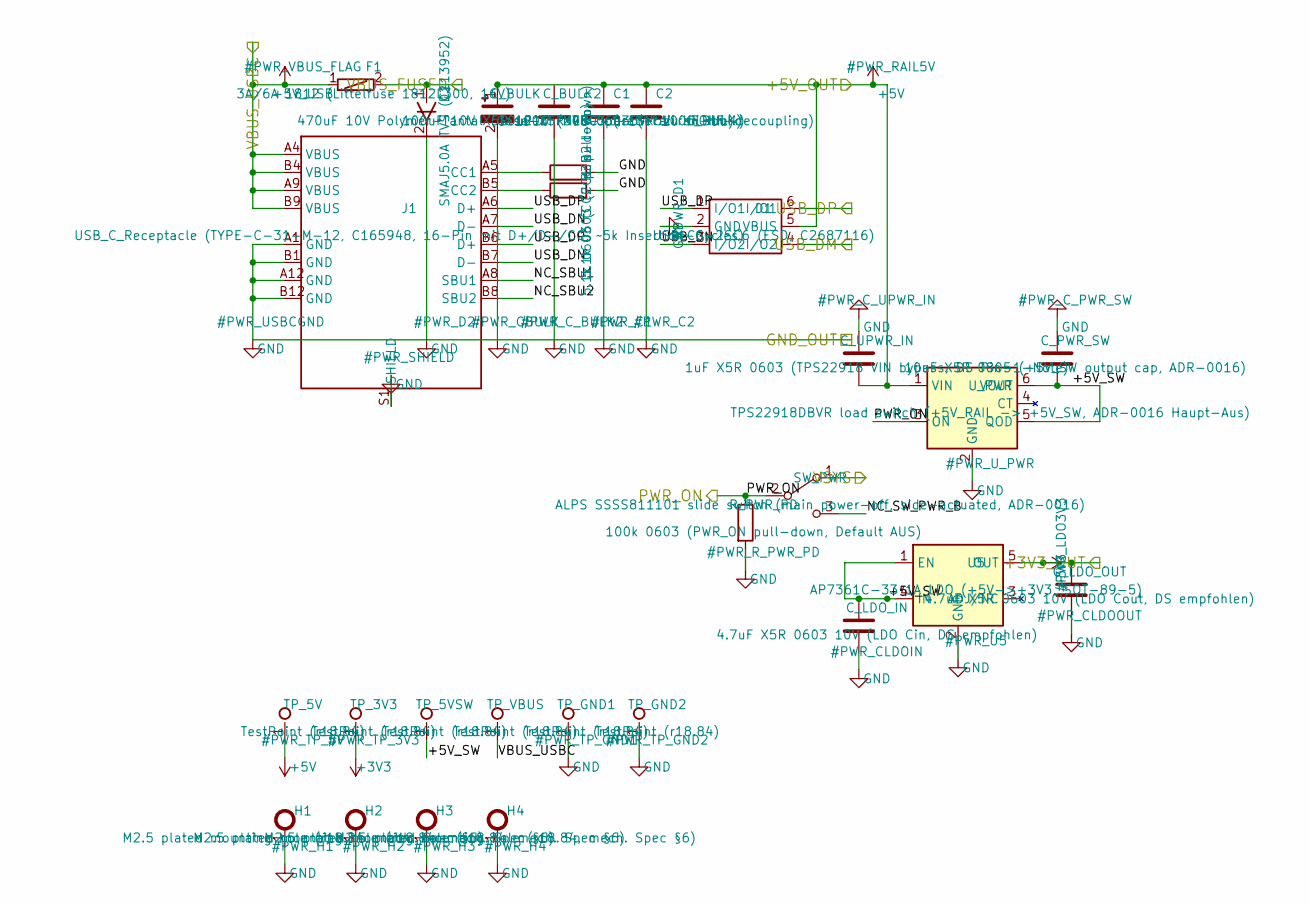
[picture p13: schematic power_tree.kicad_sch]

Parts:
C1: 10uF X5R 0805 (+5V rail HF-bulk); C_0805_2012Metric; MPN CL21A106KAYNNNE (Samsung, 25V X5R); LCSC C15850
C2: 100nF X7R 0603 (+5V rail HF-decoupling); C_0603_1608Metric; MPN CC0603KRX7R9BB104 (Yageo, 50V X7R); LCSC C14663
C_BULK: 470uF 10V Polymer-Tantal (Case-E 7343-43, ESR 100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; CP_Tantalum_Case-E_EIA-7343-43_Reflow; MPN TPSE477K010R0100 (Kyocera AVX, Polymer-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; LCSC C444831
C_BULK2: 100uF 10V X5R 1210 (MLCC parallel zu C_BULK); C_1210_3225Metric; MPN CL32A107MPVNNNE (Samsung, 100uF 10V X5R); LCSC C23742
C_LDO_IN: 4.7uF X5R 0603 10V (LDO Cin, DS empfohlen); C_0603_1608Metric; MPN GRM188R61A475KE15D; LCSC C46653
C_LDO_OUT: 4.7uF X5R 0603 10V (LDO Cout, DS empfohlen); C_0603_1608Metric; MPN GRM188R61A475KE15D; LCSC C46653
C_PWR_SW: 10uF X5R 0805 (+5V_SW output cap, ADR-0016); C_0805_2012Metric; MPN CL21A106KAYNNNE; LCSC C15850
C_UPWR_IN: 1uF X5R 0603 (TPS22918 VIN bypass, DS Pin-1-Note); C_0603_1608Metric; MPN CL10A105KB8NNNC; LCSC C15849
D1: USBLC6-2SC6 (ESD, C2687116); SOT-23-6; MPN USBLC6-2SC6; LCSC C2687116
D2: SMAJ5.0A TVS (C113952); D_SMA; MPN SMAJ5.0A; LCSC C113952
F1: 3A/6A 1812 (Littelfuse 1812L300, 16V); Fuse_1812_4532Metric; MPN 1812L300/16GR; LCSC C18198349
H1, H2, H3, H4: M2.5 plated mounting hole (r18.84, mech. Spec §6); MountingHole_2.7mm_M2.5_Pad
J1: USB_C_Receptacle (TYPE-C-31-M-12, C165948, 16-Pin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; USB_C_Receptacle_HRO_TYPE-C-31-M-12; MPN TYPE-C-31-M-12; LCSC C165948
R2: 5.1k 0603 (CC1 pull-down); R_0603_1608Metric; MPN 0603WAF5101T5E; LCSC C23186
R3: 5.1k 0603 (CC2 pull-down); R_0603_1608Metric; MPN 0603WAF5101T5E; LCSC C23186
R_PWR_PD: 100k 0603 (PWR_ON pull-down, Default AUS); R_0603_1608Metric; MPN 0603WAF1003T5E; LCSC C25803
SW_PWR: ALPS SSSS811101 slide switch (main power-off, sid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; SW_ALPS-SSSS811101_SlideSwitch_SMD; MPN SSSS811101; LCSC C109335
TP_3V3, TP_5V, TP_5VSW: TestPoint (r18.84); TestPoint_Pad_D1.5mm
TP_GND1, TP_GND2: TestPoint (r18.84); TestPoint_Pad_D1.5mm
TP_VBUS: TestPoint (r18.84); TestPoint_Pad_D1.5mm
U5: AP7361C-33 1A LDO (+5V->+3V3, SOT-89-5); SOT-89-5; MPN AP7361C-33Y5-13; LCSC C460397
U_PWR: TPS22918DBVR load switch (+5V_RAIL -> +5V_SW, ADR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; SOT-23-6; MPN TPS22918DBVR; LCSC C131941

Connections:
+3V3: C_LDO_OUT.1, TP_3V3.1, U5.5 (OUT)
+5V: C1.1, C2.1, C_BULK.1, C_UPWR_IN.1, D1.5 (VBUS), TP_5V.1, U_PWR.1 (VIN)
+5V_SW: C_LDO_IN.1, C_PWR_SW.1, TP_5VSW.1, U5.1 (EN), U5.4 (IN), U_PWR.5 (QOD), U_PWR.6 (VOUT)
+5V_USB: F1.1, J1.A4 (VBUS), J1.A9 (VBUS), J1.B4 (VBUS), J1.B9 (VBUS)
GND: C1.2, C2.2, C_BULK.2, C_BULK2.2, C_LDO_IN.2, C_LDO_OUT.2, C_PWR_SW.2, C_UPWR_IN.2, D1.2 (GND), D2.2 (A), H1.1, H2.1, H3.1, H4.1, J1.A1 (GND), J1.A12 (GND), J1.B1 (GND), J1.B12 (GND), J1.S1 (SHIELD), R2.2, R3.2, R_PWR_PD.2, TP_GND1.1, TP_GND2.1, U5.2 (GND), U_PWR.2 (GND)
NC_SBU1: J1.A8 (SBU1)
NC_SBU2: J1.B8 (SBU2)
NC_SW_PWR_B: SW_PWR.3 (B)
unnamed: J1.A5 (CC1), R2.1
unnamed: J1.B5 (CC2), R3.1
PWR_ON: R_PWR_PD.1, SW_PWR.2 (COM), U_PWR.3 (ON)
USB_DM: D1.4 (I/O2)
USB_DN: D1.3 (I/O2), J1.A7 (D-), J1.B7 (D-)
USB_DP: D1.1 (I/O1), D1.6 (I/O1), J1.A6 (D+), J1.B6 (D+)
VBUS_FUSED: D2.1 (K), F1.2
VBUS_USBC: TP_VBUS.1
VSYS: SW_PWR.1 (A)
