Sancte3D/AMBIENT/field-ambience-current/kicad/stm32h743.kicad_sch

## KiCad design field-ambience-current/kicad/stm32h743.kicad_sch (2026-07-21)

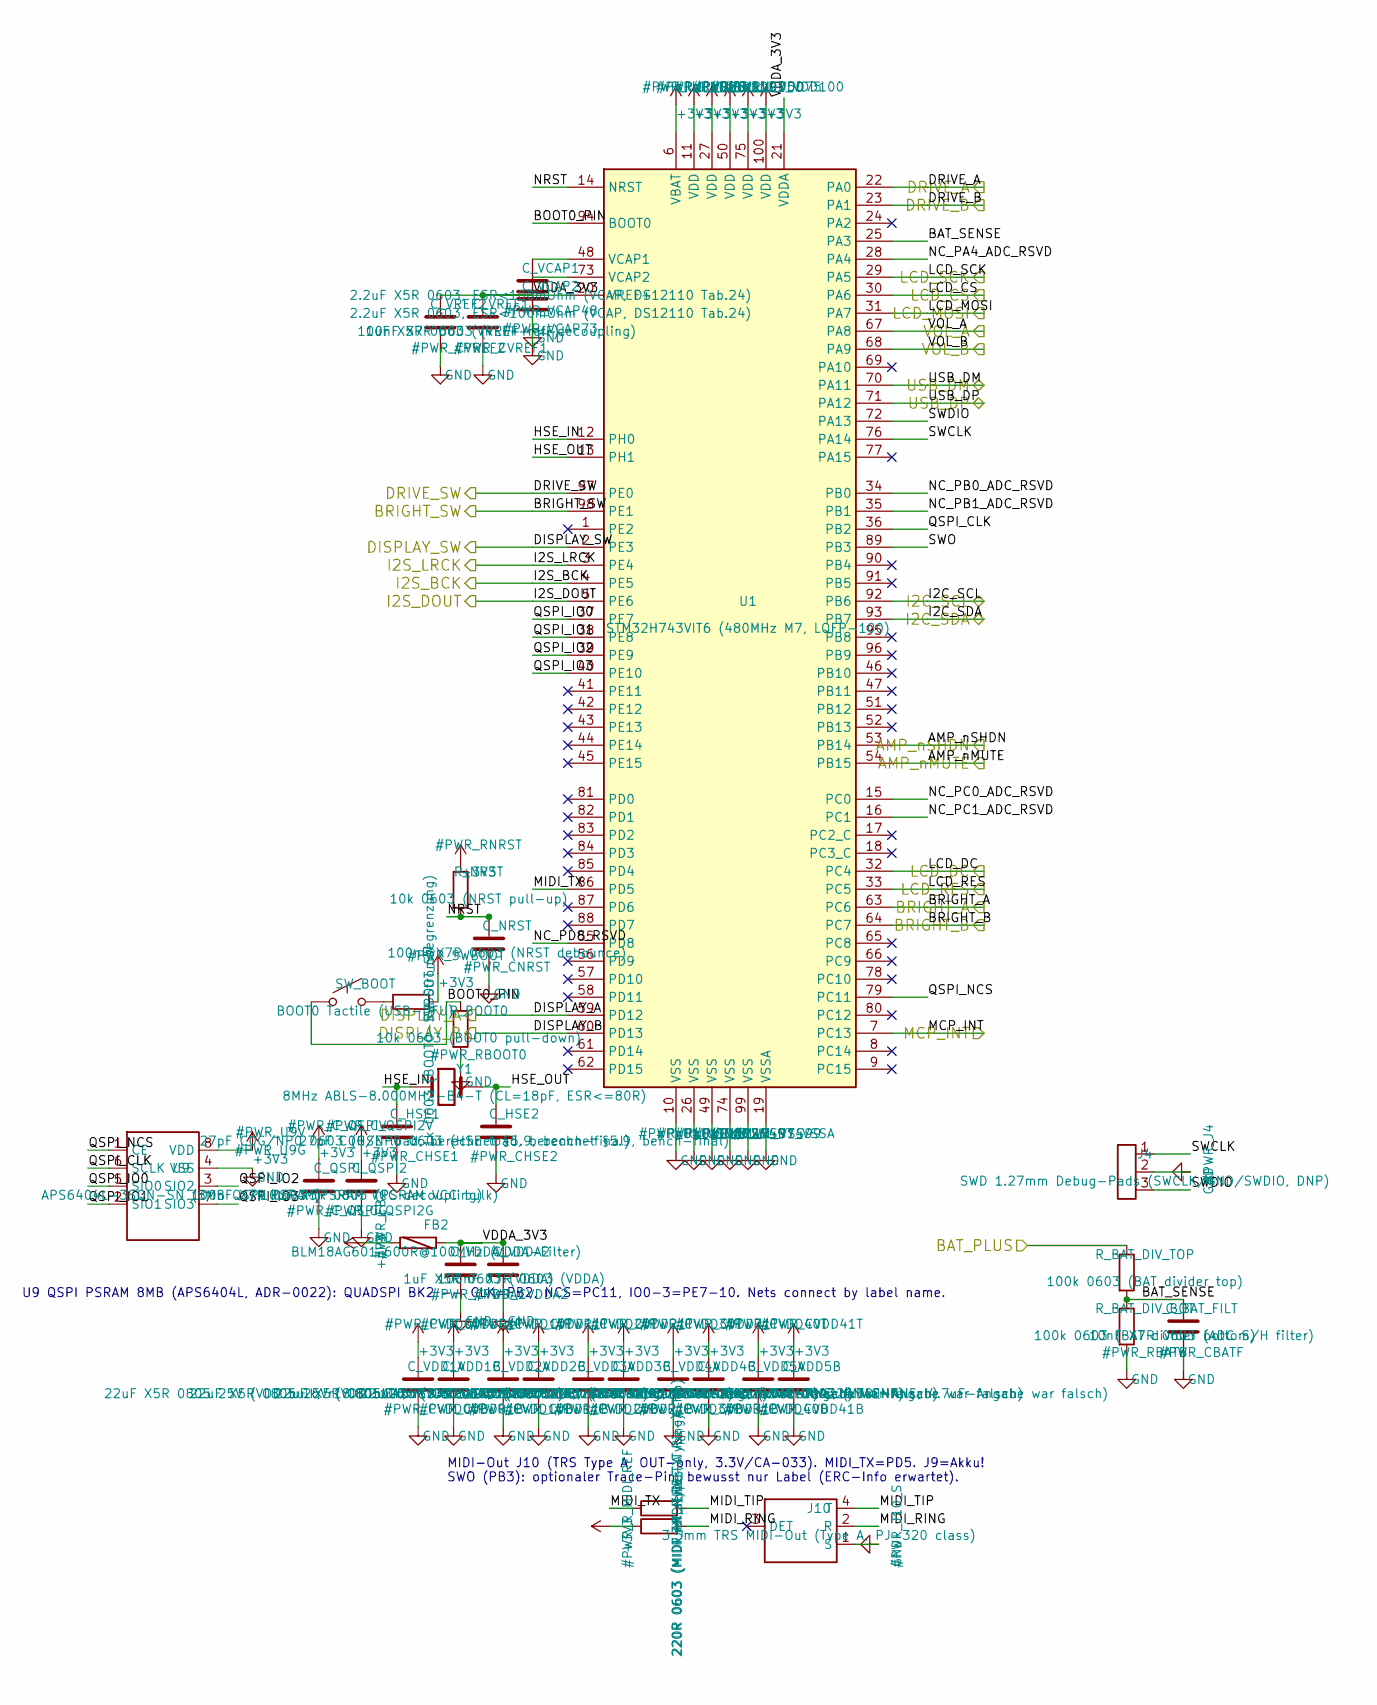
[picture p14: schematic stm32h743.kicad_sch]

Parts:
C_BAT_FILT: 10nF X7R 0603 (ADC S/H filter); C_0603_1608Metric; MPN 0603B103K500NT; LCSC C57112
C_HSE1, C_HSE2: 27pF C0G/NP0 0603 (HSE load, berechnet §5.9, benc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; C_0603_1608Metric; MPN CC0603JRNPO9BN270; LCSC C107045
C_NRST: 100nF X7R 0603 (NRST debounce); C_0603_1608Metric; MPN CC0603KRX7R9BB104; LCSC C14663
C_QSPI: 100nF X7R 0603 (PSRAM VCC decoupling); C_0603_1608Metric; MPN CC0603KRX7R9BB104; LCSC C14663
C_QSPI2: 10uF X5R 0805 (PSRAM VCC bulk); C_0805_2012Metric; MPN CL21A106KAYNNNE; LCSC C15850
C_VCAP1, C_VCAP2: 2.2uF X5R 0603, ESR<100mOhm (VCAP, DS12110 Tab.24); C_0603_1608Metric; MPN CL10A225KO8NNNC; LCSC C23630
C_VDD1A, C_VDD2A, C_VDD3A, C_VDD4A, C_VDD5A: 22uF X5R 0805 25V (VDD bulk; r18.80: C45783=CL21A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; C_0805_2012Metric; MPN CL21A226MAQNNNE; LCSC C45783
C_VDD1B, C_VDD2B, C_VDD3B, C_VDD4B, C_VDD5B: 100nF X7R 0603 (VDD HF); C_0603_1608Metric; MPN CC0603KRX7R9BB104; LCSC C14663
C_VDDA1: 1uF X5R 0603 (VDDA); C_0603_1608Metric; MPN CL10A105KB8NNNC; LCSC C15849
C_VDDA2: 100nF X7R 0603 (VDDA); C_0603_1608Metric; MPN CC0603KRX7R9BB104; LCSC C14663
C_VREF1: 1uF X5R 0603 (VREF+ ref-decoupling); C_0603_1608Metric; MPN CL10A105KB8NNNC; LCSC C15849
C_VREF2: 100nF X7R 0603 (VREF+ HF); C_0603_1608Metric; MPN CC0603KRX7R9BB104; LCSC C14663
FB2: BLM18AG601 600R@100MHz (VDDA-Filter); L_0603_1608Metric; MPN BLM18AG601SN1D; LCSC C19330
J4: SWD 1.27mm Debug-Pads (SWCLK/GND/SWDIO, DNP); PinHeader_1x03_P1.27mm_Vertical
J10: 3.5mm TRS MIDI-Out (Type A, PJ-320 class); Jack_3.5mm_PJ-320D_SMT; MPN PJ-320D (3.5mm TRS w/ switch); LCSC C431535
R_BAT_DIV_BOT: 100k 0603 (BAT divider bottom); R_0603_1608Metric; MPN 0603WAF1002T5E; LCSC C25804
R_BAT_DIV_TOP: 100k 0603 (BAT divider top); R_0603_1608Metric; MPN 0603WAF1002T5E; LCSC C25804
R_BOOT0: 10k 0603 (BOOT0 pull-down); R_0603_1608Metric; MPN 0603WAF1002T5E; LCSC C25804
R_BOOT_SW: 1k 0603 (BOOT0-SW Strombegrenzung); R_0603_1608Metric; MPN 0603WAF1001T5E; LCSC C21190
R_MIDI_REF: 220R 0603 (MIDI ref, Type-A Ring); R_0603_1608Metric; MPN 0603WAF2200T5E (220R 0603); LCSC C22962
R_MIDI_TX: 220R 0603 (MIDI TX series, Type-A Tip); R_0603_1608Metric; MPN 0603WAF2200T5E (220R 0603); LCSC C22962
R_NRST: 10k 0603 (NRST pull-up); R_0603_1608Metric; MPN 0603WAF1002T5E; LCSC C25804
SW_BOOT: BOOT0 Tactile (USB-DFU); SW_TS1088_SMD; MPN TS-1088-AR02016; LCSC C720477
U1: STM32H743VIT6 (480MHz M7, LQFP-100); LQFP-100_14x14mm_P0.5mm; MPN STM32H743VIT6; LCSC C114409
U9: APS6404L-3SQN-SN (8MB QSPI PSRAM); SOIC-8_3.9x4.9mm_P1.27mm; MPN APS6404L-3SQN-SN; LCSC C3028887
Y1: 8MHz ABLS-8.000MHZ-B4-T (CL=18pF, ESR<=80R); Crystal_HC49-US-SMD_ABLS; MPN ABLS-8.000MHZ-B4-T; LCSC C596838

Connections:
+3V3: C_QSPI.1, C_QSPI2.1, C_VDD1A.1, C_VDD1B.1, C_VDD2A.1, C_VDD2B.1, C_VDD3A.1, C_VDD3B.1, C_VDD4A.1, C_VDD4B.1, C_VDD5A.1, C_VDD5B.1, FB2.1, R_BOOT_SW.2, R_MIDI_REF.1, R_NRST.1, U1.6 (VBAT), U1.11 (VDD), U1.27 (VDD), U1.50 (VDD), U1.75 (VDD), U1.100 (VDD), U9.8 (VDD)
AMP_nMUTE: U1.54 (PB15)
AMP_nSHDN: U1.53 (PB14)
BAT_PLUS: R_BAT_DIV_TOP.1
BAT_SENSE: C_BAT_FILT.1, R_BAT_DIV_BOT.1, R_BAT_DIV_TOP.2, U1.25 (PA3)
BOOT0_PIN: R_BOOT0.1, SW_BOOT.1, U1.94 (BOOT0)
BRIGHT_A: U1.63 (PC6)
BRIGHT_B: U1.64 (PC7)
BRIGHT_SW: U1.98 (PE1)
DISPLAY_A: U1.59 (PD12)
DISPLAY_B: U1.60 (PD13)
DISPLAY_SW: U1.2 (PE3)
DRIVE_A: U1.22 (PA0)
DRIVE_B: U1.23 (PA1)
DRIVE_SW: U1.97 (PE0)
GND: C_BAT_FILT.2, C_HSE1.2, C_HSE2.2, C_NRST.2, C_QSPI.2, C_QSPI2.2, C_VCAP1.2, C_VCAP2.2, C_VDD1A.2, C_VDD1B.2, C_VDD2A.2, C_VDD2B.2, C_VDD3A.2, C_VDD3B.2, C_VDD4A.2, C_VDD4B.2, C_VDD5A.2, C_VDD5B.2, C_VDDA1.2, C_VDDA2.2, C_VREF1.2, C_VREF2.2, J4.2, J10.1 (S), R_BAT_DIV_BOT.2, R_BOOT0.2, U1.10 (VSS), U1.19 (VSSA), U1.26 (VSS), U1.49 (VSS), U1.74 (VSS), U1.99 (VSS), U9.4 (VSS)
HSE_IN: C_HSE1.1, U1.12 (PH0), Y1.1
HSE_OUT: C_HSE2.1, U1.13 (PH1), Y1.2
I2C_SCL: U1.92 (PB6)
I2C_SDA: U1.93 (PB7)
I2S_BCK: U1.4 (PE5)
I2S_DOUT: U1.5 (PE6)
I2S_LRCK: U1.3 (PE4)
LCD_CS: U1.30 (PA6)
LCD_DC: U1.32 (PC4)
LCD_MOSI: U1.31 (PA7)
LCD_RES: U1.33 (PC5)
LCD_SCK: U1.29 (PA5)
MCP_INT: U1.7 (PC13)
MIDI_RING: J10.2 (R), R_MIDI_REF.2
MIDI_TIP: J10.4 (T), R_MIDI_TX.2
MIDI_TX: R_MIDI_TX.1, U1.86 (PD5)
NC_PA4_ADC_RSVD: U1.28 (PA4)
NC_PB0_ADC_RSVD: U1.34 (PB0)
NC_PB1_ADC_RSVD: U1.35 (PB1)
NC_PC0_ADC_RSVD: U1.15 (PC0)
NC_PC1_ADC_RSVD: U1.16 (PC1)
NC_PD8_RSVD: U1.55 (PD8)
NRST: C_NRST.1, R_NRST.2, U1.14 (NRST)
unnamed: C_VCAP1.1, U1.48 (VCAP1)
unnamed: C_VCAP2.1, U1.73 (VCAP2)
unnamed: R_BOOT_SW.1, SW_BOOT.2
QSPI_CLK: U1.36 (PB2), U9.6 (SCLK)
QSPI_IO0: U1.37 (PE7), U9.5 (SIO0)
QSPI_IO1: U1.38 (PE8), U9.2 (SIO1)
QSPI_IO2: U1.39 (PE9), U9.3 (SIO2)
QSPI_IO3: U1.40 (PE10), U9.7 (SIO3)
QSPI_NCS: U1.79 (PC11), U9.1 (CE)
SWCLK: J4.1, U1.76 (PA14)
SWDIO: J4.3, U1.72 (PA13)
SWO: U1.89 (PB3)
USB_DM: U1.70 (PA11)
USB_DP: U1.71 (PA12)
VDDA_3V3: C_VDDA1.1, C_VDDA2.1, C_VREF1.1, C_VREF2.1, FB2.2, U1.20 (VREF+), U1.21 (VDDA)
VOL_A: U1.67 (PA8)
VOL_B: U1.68 (PA9)

Notes on the sheet:
MIDI-Out J10 (TRS Type A, OUT-only, 3.3V/CA-033). MIDI_TX=PD5. J9=Akku!
SWO (PB3): optionaler Trace-Pin, bewusst nur Label (ERC-Info erwartet).
U9 QSPI PSRAM 8MB (APS6404L, ADR-0022): QUADSPI BK2 -- CLK=PB2, NCS=PC11, IO0-3=PE7-10. Nets connect by label name.
