Sancte3D/AMBIENT/field-ambience-current/kicad/generate_kicad_project.py

"""
KiCad-9 Projekt-Generator für Field Ambience PCB SPEC v0.6.

Reproduzierbar regenerierbar bei Spec-Änderungen. Erzeugt:
  - field_ambience.kicad_pro      (Projekt-JSON)
  - field_ambience.kicad_sch      (Root-Schematic mit hierarchischen Sheet-Refs)
  - power_tree.kicad_sch          (Sheet 1: USB-C -> F1 -> Bulk -> +5V/+3V3 Rail)

Stand: Sheet 1 implementiert. Sheets 2-7 (Pico, OLED, MCP23017, Encoder,
Audio, Pi-Header) als next-Step erweitern. UUIDs deterministisch aus
sha1(seed) abgeleitet damit Re-Generierung stabile IDs gibt.
"""

from __future__ import annotations

import hashlib
import json
import uuid
from pathlib import Path

OUT_DIR = Path(__file__).resolve().parent
PROJECT_NAME = "field_ambience"
KICAD_VERSION_TAG = "20231120"  # KiCad 9 schematic format tag
GENERATOR = '(generator "kicad_python") (generator_version "9.0")'


def det_uuid(seed: str) -> str:
    """Deterministic UUID v4-shaped from sha1(seed) for stable re-runs."""
    h = hashlib.sha1(seed.encode()).hexdigest()
    return f"{h[0:8]}-{h[8:12]}-4{h[13:16]}-a{h[17:20]}-{h[20:32]}"


def kicad_pro() -> str:
    """Minimal KiCad 9 .kicad_pro project file (JSON)."""
    pro = {
        "board": {
            "design_settings": {
                "defaults": {
                    "board_outline_line_width": 0.05,
                    "copper_line_width": 0.2,
                    "copper_text_size_h": 1.5,
                    "copper_text_size_v": 1.5,
                    "copper_text_thickness": 0.3,
                },
            },
        },
        "boards": [],
        "cvpcb": {"equivalence_files": []},
        "erc": {
            "erc_exclusions": [],
            "meta": {"version": 0},
            "pin_map": [],
            "rule_severities": {
                "bus_definition_conflict": "error",
                "bus_entry_needed": "error",
                "bus_to_bus_conflict": "error",
                "bus_to_net_conflict": "error",
                "different_unit_footprint": "error",
                "different_unit_net": "error",
                "duplicate_reference": "error",
                "duplicate_sheet_names": "error",
                "endpoint_off_grid": "warning",
                "extra_units": "error",
                "global_label_dangling": "warning",
                "hier_label_mismatch": "error",
                "label_dangling": "error",
                "lib_symbol_issues": "warning",
                "missing_bidi_pin": "warning",
                "missing_input_pin": "warning",
                "missing_power_pin": "error",
                "missing_unit": "warning",
                "multiple_net_names": "warning",
                "net_not_bus_member": "warning",
                "no_connect_connected": "warning",
                "no_connect_dangling": "warning",
                "pin_not_connected": "error",
                "pin_not_driven": "error",
                "pin_to_pin": "warning",
                "power_pin_not_driven": "error",
                "similar_labels": "warning",
                "simulation_model_issue": "ignore",
                "unannotated": "error",
                "unit_value_mismatch": "error",
                "unresolved_variable": "error",
                "wire_dangling": "error",
            },
        },
        "libraries": {"pinned_footprint_libs": [], "pinned_symbol_libs": []},
        "meta": {"filename": f"{PROJECT_NAME}.kicad_pro", "version": 1},
        "net_settings": {
            "classes": [
                {
                    "bus_width": 12,
                    "clearance": 0.2,
                    "diff_pair_gap": 0.25,
                    "diff_pair_via_gap": 0.25,
                    "diff_pair_width": 0.2,
                    "line_style": 0,
                    "microvia_diameter": 0.3,
                    "microvia_drill": 0.1,
                    "name": "Default",
                    "pcb_color": "rgba(0, 0, 0, 0.000)",
                    "schematic_color": "rgba(0, 0, 0, 0.000)",
                    "track_width": 0.25,
                    "via_diameter": 0.6,
                    "via_drill": 0.3,
                    "wire_width": 6,
                }
            ],
            "meta": {"version": 3},
            "net_colors": None,
            "netclass_assignments": None,
            "netclass_patterns": [],
        },
        "pcbnew": {"page_layout_descr_file": ""},
        "schematic": {
            "annotate_start_num": 0,
            "drawing": {
                "dashed_lines_dash_length_ratio": 12.0,
                "dashed_lines_gap_length_ratio": 3.0,
                "default_line_thickness": 6.0,
                "default_text_size": 50.0,
                "field_names": [],
                "intersheets_ref_own_page": False,
                "intersheets_ref_prefix": "",
                "intersheets_ref_short": False,
                "intersheets_ref_show": False,
                "intersheets_ref_suffix": "",
                "junction_size_choice": 3,
                "label_size_ratio": 0.375,
                "operating_point_overlay_i_precision": 3,
                "operating_point_overlay_i_range": "~A",
                "operating_point_overlay_v_precision": 3,
                "operating_point_overlay_v_range": "~V",
                "overbar_offset_ratio": 1.23,
                "pin_symbol_size": 25.0,
                "text_offset_ratio": 0.15,
            },
            "legacy_lib_dir": "",
            "legacy_lib_list": [],
            "meta": {"version": 1},
            "net_format_name": "",
            "page_layout_descr_file": "",
            "plot_directory": "",
            "spice_current_sheet_as_root": False,
            "spice_external_command": "spice \"%I\"",
            "spice_model_current_sheet_as_root": True,
            "spice_save_all_currents": False,
            "spice_save_all_voltages": False,
            "spice_save_all_dissipations": False,
            "subpart_first_id": 65,
            "subpart_id_separator": 0,
        },
        "sheets": [
            [det_uuid("root_sheet"), "Root"],
            [det_uuid("sheet_power_tree"), "PowerTree"],
            [det_uuid("sheet_stm32"), "STM32H743"],
            [det_uuid("sheet_lcd"), "LCD"],
            [det_uuid("sheet_mcp"), "MCP23017"],
            [det_uuid("sheet_encoder"), "Encoders"],
            [det_uuid("sheet_audio"), "Audio"],
            [det_uuid("sheet_battery"), "Battery"],
        ],
        "text_variables": {},
    }
    return json.dumps(pro, indent=2)


# ----------------------------------------------------------------------------
# Inline symbol library — minimale, eigenständige Symbol-Definitionen
# damit das Schematic ohne externe KiCad-Bibliotheken parst + öffnet.
# Im KiCad-GUI später via "Update Symbol Library Links" auf Standard-Libs neu
# verlinken.
# ----------------------------------------------------------------------------

LIB_SYMBOLS = r"""
    (symbol "Power:+5V" (power) (pin_names (offset 0)) (in_bom yes) (on_board yes)
      (property "Reference" "#PWR" (at 0 -3.81 0)
        (effects (font (size 1.27 1.27)) hide))
      (property "Value" "+5V" (at 0 3.556 0)
        (effects (font (size 1.27 1.27))))
      (property "Footprint" "" (at 0 0 0) (effects (font (size 1.27 1.27)) hide))
      (property "Datasheet" "" (at 0 0 0) (effects (font (size 1.27 1.27)) hide))
      (symbol "Power:+5V_0_1"
        (polyline (pts (xy -0.762 1.27) (xy 0 2.54)) (stroke (width 0) (type default)) (fill (type none)))
        (polyline (pts (xy 0 0) (xy 0 2.54)) (stroke (width 0) (type default)) (fill (type none)))
        (polyline (pts (xy 0 2.54) (xy 0.762 1.27)) (stroke (width 0) (type default)) (fill (type none))))
      (symbol "Power:+5V_1_1"
        (pin power_in line (at 0 0 90) (length 0) hide
          (name "+5V" (effects (font (size 1.27 1.27))))
          (number "1" (effects (font (size 1.27 1.27)))))))
    (symbol "Power:GND" (power) (pin_names (offset 0)) (in_bom yes) (on_board yes)
      (property "Reference" "#PWR" (at 0 -6.35 0)
        (effects (font (size 1.27 1.27)) hide))
      (property "Value" "GND" (at 0 -3.81 0)
        (effects (font (size 1.27 1.27))))
      (property "Footprint" "" (at 0 0 0) (effects (font (size 1.27 1.27)) hide))
      (property "Datasheet" "" (at 0 0 0) (effects (font (size 1.27 1.27)) hide))
      (symbol "Power:GND_0_1"
        (polyline (pts (xy 0 0) (xy 0 -1.27) (xy 1.27 -1.27) (xy 0 -2.54) (xy -1.27 -1.27) (xy 0 -1.27))
          (stroke (width 0) (type default)) (fill (type none))))
      (symbol "Power:GND_1_1"
        (pin power_in line (at 0 0 270) (length 0) hide
          (name "GND" (effects (font (size 1.27 1.27))))
          (number "1" (effects (font (size 1.27 1.27)))))))
    (symbol "Power:VBUS" (power) (pin_names (offset 0)) (in_bom yes) (on_board yes)
      (property "Reference" "#PWR" (at 0 -3.81 0)
        (effects (font (size 1.27 1.27)) hide))
      (property "Value" "VBUS" (at 0 3.556 0)
        (effects (font (size 1.27 1.27))))
      (property "Footprint" "" (at 0 0 0) (effects (font (size 1.27 1.27)) hide))
      (property "Datasheet" "" (at 0 0 0) (effects (font (size 1.27 1.27)) hide))
      (symbol "Power:VBUS_0_1"
        (polyline (pts (xy -0.762 1.27) (xy 0 2.54)) (stroke (width 0) (type default)) (fill (type none)))
        (polyline (pts (xy 0 0) (xy 0 2.54)) (stroke (width 0) (type default)) (fill (type none)))
        (polyline (pts (xy 0 2.54) (xy 0.762 1.27)) (stroke (width 0) (type default)) (fill (type none))))
      (symbol "Power:VBUS_1_1"
        (pin power_in line (at 0 0 90) (length 0) hide
          (name "VBUS" (effects (font (size 1.27 1.27))))
          (number "1" (effects (font (size 1.27 1.27)))))))
    (symbol "Device:R" (pin_numbers hide) (pin_names (offset 0)) (in_bom yes) (on_board yes)
      (property "Reference" "R" (at 2.032 0 90) (effects (font (size 1.27 1.27))))
      (property "Value" "R" (at 0 0 90) (effects (font (size 1.27 1.27))))
      (property "Footprint" "" (at -1.778 0 90) (effects (font (size 1.27 1.27)) hide))
      (property "Datasheet" "~" (at 0 0 0) (effects (font (size 1.27 1.27)) hide))
      (symbol "Device:R_0_1"
        (rectangle (start -1.016 -2.54) (end 1.016 2.54)
          (stroke (width 0.254) (type default)) (fill (type none))))
      (symbol "Device:R_1_1"
        (pin passive line (at 0 3.81 270) (length 1.27)
          (name "~" (effects (font (size 1.27 1.27))))
          (number "1" (effects (font (size 1.27 1.27)))))
        (pin passive line (at 0 -3.81 90) (length 1.27)
          (name "~" (effects (font (size 1.27 1.27))))
          (number "2" (effects (font (size 1.27 1.27)))))))
    (symbol "Device:C" (pin_numbers hide) (pin_names (offset 0.254)) (in_bom yes) (on_board yes)
      (property "Reference" "C" (at 0.635 2.54 0) (effects (font (size 1.27 1.27))))
      (property "Value" "C" (at 0.635 -2.54 0) (effects (font (size 1.27 1.27))))
      (property "Footprint" "" (at 0.9652 -3.81 0) (effects (font (size 1.27 1.27)) hide))
      (property "Datasheet" "~" (at 0 0 0) (effects (font (size 1.27 1.27)) hide))
      (symbol "Device:C_0_1"
        (polyline (pts (xy -2.032 -0.762) (xy 2.032 -0.762))
          (stroke (width 0.508) (type default)) (fill (type none)))
        (polyline (pts (xy -2.032 0.762) (xy 2.032 0.762))
          (stroke (width 0.508) (type default)) (fill (type none))))
      (symbol "Device:C_1_1"
        (pin passive line (at 0 3.81 270) (length 2.794)
          (name "~" (effects (font (size 1.27 1.27))))
          (number "1" (effects (font (size 1.27 1.27)))))
        (pin passive line (at 0 -3.81 90) (length 2.794)
          (name "~" (effects (font (size 1.27 1.27))))
          (number "2" (effects (font (size 1.27 1.27)))))))
    (symbol "Device:CP" (pin_names (offset 0.254)) (in_bom yes) (on_board yes)
      (property "Reference" "C" (at 0.9525 2.54 0) (effects (font (size 1.27 1.27))))
      (property "Value" "C_Polarized" (at 0.9525 -2.54 0) (effects (font (size 1.27 1.27))))
      (property "Footprint" "" (at 2.54 -3.81 0) (effects (font (size 1.27 1.27)) hide))
      (property "Datasheet" "~" (at 0 0 0) (effects (font (size 1.27 1.27)) hide))
      (symbol "Device:CP_0_1"
        (rectangle (start -2.286 -0.508) (end 2.286 -1.524)
          (stroke (width 0) (type default)) (fill (type outline)))
        (polyline (pts (xy -2.032 0.762) (xy 2.032 0.762))
          (stroke (width 0.508) (type default)) (fill (type none)))
        (polyline (pts (xy -1.778 2.286) (xy -1.778 1.524))
          (stroke (width 0.3048) (type default)) (fill (type none)))
        (polyline (pts (xy -1.397 1.905) (xy -2.159 1.905))
          (stroke (width 0.3048) (type default)) (fill (type none))))
      (symbol "Device:CP_1_1"
        (pin passive line (at 0 3.81 270) (length 2.794)
          (name "~" (effects (font (size 1.27 1.27))))
          (number "1" (effects (font (size 1.27 1.27)))))
        (pin passive line (at 0 -3.81 90) (length 2.794)
          (name "~" (effects (font (size 1.27 1.27))))
          (number "2" (effects (font (size 1.27 1.27)))))))
    (symbol "Device:Polyfuse" (pin_names (offset 0.254) hide) (in_bom yes) (on_board yes)
      (property "Reference" "F" (at 0 2.794 0) (effects (font (size 1.27 1.27))))
      (property "Value" "Polyfuse" (at 0 -2.794 0) (effects (font (size 1.27 1.27))))
      (property "Footprint" "" (at 0 0 0) (effects (font (size 1.27 1.27)) hide))
      (property "Datasheet" "~" (at 0 0 0) (effects (font (size 1.27 1.27)) hide))
      (symbol "Device:Polyfuse_0_1"
        (rectangle (start -2.54 -0.762) (end 2.54 0.762)
          (stroke (width 0.254) (type default)) (fill (type none)))
        (polyline (pts (xy -1.524 -0.508) (xy 1.524 0.508))
          (stroke (width 0.254) (type default)) (fill (type none))))
      (symbol "Device:Polyfuse_1_1"
        (pin passive line (at -3.81 0 0) (length 1.27)
          (name "~" (effects (font (size 1.27 1.27))))
          (number "1" (effects (font (size 1.27 1.27)))))
        (pin passive line (at 3.81 0 180) (length 1.27)
          (name "~" (effects (font (size 1.27 1.27))))
          (number "2" (effects (font (size 1.27 1.27)))))))
    (symbol "Device:D_TVS" (pin_names (offset 0.254) hide) (in_bom yes) (on_board yes)
      (property "Reference" "D" (at 0 2.794 0) (effects (font (size 1.27 1.27))))
      (property "Value" "D_TVS" (at 0 -2.794 0) (effects (font (size 1.27 1.27))))
      (property "Footprint" "" (at 0 0 0) (effects (font (size 1.27 1.27)) hide))
      (property "Datasheet" "~" (at 0 0 0) (effects (font (size 1.27 1.27)) hide))
      (symbol "Device:D_TVS_0_1"
        (polyline (pts (xy 0 -1.27) (xy 0 1.27))
          (stroke (width 0.254) (type default)) (fill (type none)))
        (polyline (pts (xy -1.27 -1.27) (xy 1.27 0) (xy -1.27 1.27))
          (stroke (width 0.254) (type default)) (fill (type none))))
      (symbol "Device:D_TVS_1_1"
        (pin passive line (at -3.81 0 0) (length 2.54)
          (name "K" (effects (font (size 1.27 1.27))))
          (number "1" (effects (font (size 1.27 1.27)))))
        (pin passive line (at 3.81 0 180) (length 2.54)
          (name "A" (effects (font (size 1.27 1.27))))
          (number "2" (effects (font (size 1.27 1.27)))))))
    (symbol "Connector:USB_C_Receptacle" (in_bom yes) (on_board yes)
      (property "Reference" "J" (at 0 17.78 0) (effects (font (size 1.27 1.27))))
      (property "Value" "USB_C_Receptacle" (at 0 15.24 0) (effects (font (size 1.27 1.27))))
      (property "Footprint" "" (at 0 0 0) (effects (font (size 1.27 1.27)) hide))
      (property "Datasheet" "https://www.usb.org/" (at 0 0 0) (effects (font (size 1.27 1.27)) hide))
      (symbol "Connector:USB_C_Receptacle_0_1"
        (rectangle (start -12.7 12.7) (end 12.7 -22.86)
          (stroke (width 0.254) (type default)) (fill (type none))))
      (symbol "Connector:USB_C_Receptacle_1_1"
        (pin power_in line (at -15.24 10.16 0) (length 2.54)
          (name "VBUS" (effects (font (size 1.27 1.27))))
          (number "A4" (effects (font (size 1.27 1.27)))))
        (pin power_in line (at -15.24 7.62 0) (length 2.54)
          (name "VBUS" (effects (font (size 1.27 1.27))))
          (number "B4" (effects (font (size 1.27 1.27)))))
        (pin power_in line (at -15.24 5.08 0) (length 2.54)
          (name "VBUS" (effects (font (size 1.27 1.27))))
          (number "A9" (effects (font (size 1.27 1.27)))))
        (pin power_in line (at -15.24 2.54 0) (length 2.54)
          (name "VBUS" (effects (font (size 1.27 1.27))))
          (number "B9" (effects (font (size 1.27 1.27)))))
        (pin bidirectional line (at 15.24 7.62 180) (length 2.54)
          (name "CC1" (effects (font (size 1.27 1.27))))
          (number "A5" (effects (font (size 1.27 1.27)))))
        (pin bidirectional line (at 15.24 5.08 180) (length 2.54)
          (name "CC2" (effects (font (size 1.27 1.27))))
          (number "B5" (effects (font (size 1.27 1.27)))))
        (pin bidirectional line (at 15.24 2.54 180) (length 2.54)
          (name "D+" (effects (font (size 1.27 1.27))))
          (number "A6" (effects (font (size 1.27 1.27)))))
        (pin bidirectional line (at 15.24 0 180) (length 2.54)
          (name "D-" (effects (font (size 1.27 1.27))))
          (number "A7" (effects (font (size 1.27 1.27)))))
        (pin bidirectional line (at 15.24 -2.54 180) (length 2.54)
          (name "D+" (effects (font (size 1.27 1.27))))
          (number "B6" (effects (font (size 1.27 1.27)))))
        (pin bidirectional line (at 15.24 -5.08 180) (length 2.54)
          (name "D-" (effects (font (size 1.27 1.27))))
          (number "B7" (effects (font (size 1.27 1.27)))))
        (pin bidirectional line (at 15.24 -7.62 180) (length 2.54)
          (name "SBU1" (effects (font (size 1.27 1.27))))
          (number "A8" (effects (font (size 1.27 1.27)))))
        (pin bidirectional line (at 15.24 -10.16 180) (length 2.54)
          (name "SBU2" (effects (font (size 1.27 1.27))))
          (number "B8" (effects (font (size 1.27 1.27)))))
        (pin power_in line (at -15.24 -2.54 0) (length 2.54)
          (name "GND" (effects (font (size 1.27 1.27))))
          (number "A1" (effects (font (size 1.27 1.27)))))
        (pin power_in line (at -15.24 -5.08 0) (length 2.54)
          (name "GND" (effects (font (size 1.27 1.27))))
          (number "B1" (effects (font (size 1.27 1.27)))))
        (pin power_in line (at -15.24 -7.62 0) (length 2.54)
          (name "GND" (effects (font (size 1.27 1.27))))
          (number "A12" (effects (font (size 1.27 1.27)))))
        (pin power_in line (at -15.24 -10.16 0) (length 2.54)
          (name "GND" (effects (font (size 1.27 1.27))))
          (number "B12" (effects (font (size 1.27 1.27)))))
        (pin power_in line (at 0 -25.4 90) (length 2.54)
          (name "SHIELD" (effects (font (size 1.27 1.27))))
          (number "S1" (effects (font (size 1.27 1.27)))))))
    (symbol "Power_Protection:USBLC6-2SC6" (in_bom yes) (on_board yes)
      (property "Reference" "D" (at 0 7.62 0) (effects (font (size 1.27 1.27))))
      (property "Value" "USBLC6-2SC6" (at 0 5.08 0) (effects (font (size 1.27 1.27))))
      (property "Footprint" "Package_TO_SOT_SMD:SOT-23-6" (at 0 0 0) (effects (font (size 1.27 1.27)) hide))
      (property "Datasheet" "https://www.st.com/resource/en/datasheet/usblc6-2.pdf" (at 0 0 0) (effects (font (size 1.27 1.27)) hide))
      (symbol "Power_Protection:USBLC6-2SC6_0_1"
        (rectangle (start -5.08 3.81) (end 5.08 -3.81)
          (stroke (width 0.254) (type default)) (fill (type none))))
      (symbol "Power_Protection:USBLC6-2SC6_1_1"
        (pin bidirectional line (at -7.62 2.54 0) (length 2.54)
          (name "I/O1" (effects (font (size 1.27 1.27))))
          (number "1" (effects (font (size 1.27 1.27)))))
        (pin power_in line (at -7.62 0 0) (length 2.54)
          (name "GND" (effects (font (size 1.27 1.27))))
          (number "2" (effects (font (size 1.27 1.27)))))
        (pin bidirectional line (at -7.62 -2.54 0) (length 2.54)
          (name "I/O2" (effects (font (size 1.27 1.27))))
          (number "3" (effects (font (size 1.27 1.27)))))
        (pin bidirectional line (at 7.62 -2.54 180) (length 2.54)
          (name "I/O2" (effects (font (size 1.27 1.27))))
          (number "4" (effects (font (size 1.27 1.27)))))
        (pin power_in line (at 7.62 0 180) (length 2.54)
          (name "VBUS" (effects (font (size 1.27 1.27))))
          (number "5" (effects (font (size 1.27 1.27)))))
        (pin bidirectional line (at 7.62 2.54 180) (length 2.54)
          (name "I/O1" (effects (font (size 1.27 1.27))))
          (number "6" (effects (font (size 1.27 1.27)))))))
    (symbol "Power:+3V3" (power) (pin_names (offset 0)) (in_bom yes) (on_board yes)
      (property "Reference" "#PWR" (at 0 -3.81 0)
        (effects (font (size 1.27 1.27)) hide))
      (property "Value" "+3V3" (at 0 3.556 0)
        (effects (font (size 1.27 1.27))))
      (property "Footprint" "" (at 0 0 0) (effects (font (size 1.27 1.27)) hide))
      (property "Datasheet" "" (at 0 0 0) (effects (font (size 1.27 1.27)) hide))
      (symbol "Power:+3V3_0_1"
        (polyline (pts (xy -0.762 1.27) (xy 0 2.54)) (stroke (width 0) (type default)) (fill (type none)))
        (polyline (pts (xy 0 0) (xy 0 2.54)) (stroke (width 0) (type default)) (fill (type none)))
        (polyline (pts (xy 0 2.54) (xy 0.762 1.27)) (stroke (width 0) (type default)) (fill (type none))))
      (symbol "Power:+3V3_1_1"
        (pin power_in line (at 0 0 90) (length 0) hide
          (name "+3V3" (effects (font (size 1.27 1.27))))
          (number "1" (effects (font (size 1.27 1.27)))))))
    (symbol "Device:LED" (pin_numbers hide) (pin_names (offset 1.016) hide) (in_bom yes) (on_board yes)
      (property "Reference" "D" (at 0 2.54 0) (effects (font (size 1.27 1.27))))
      (property "Value" "LED" (at 0 -2.54 0) (effects (font (size 1.27 1.27))))
      (property "Footprint" "" (at 0 0 0) (effects (font (size 1.27 1.27)) hide))
      (property "Datasheet" "~" (at 0 0 0) (effects (font (size 1.27 1.27)) hide))
      (symbol "Device:LED_0_1"
        (polyline (pts (xy -1.27 -1.27) (xy -1.27 1.27))
          (stroke (width 0.254) (type default)) (fill (type none)))
        (polyline (pts (xy -1.27 0) (xy 1.27 1.27) (xy 1.27 -1.27) (xy -1.27 0))
          (stroke (width 0.254) (type default)) (fill (type none))))
      (symbol "Device:LED_1_1"
        (pin passive line (at -3.81 0 0) (length 2.54)
          (name "K" (effects (font (size 1.27 1.27))))
          (number "1" (effects (font (size 1.27 1.27)))))
        (pin passive line (at 3.81 0 180) (length 2.54)
          (name "A" (effects (font (size 1.27 1.27))))
          (number "2" (effects (font (size 1.27 1.27)))))))
    (symbol "Switch:SW_Push" (pin_numbers hide) (pin_names (offset 1.016) hide) (in_bom yes) (on_board yes)
      (property "Reference" "SW" (at 1.27 2.54 0) (effects (font (size 1.27 1.27))))
      (property "Value" "SW_Push" (at 0 -1.524 0) (effects (font (size 1.27 1.27))))
      (property "Footprint" "" (at 0 0 0) (effects (font (size 1.27 1.27)) hide))
      (property "Datasheet" "~" (at 0 0 0) (effects (font (size 1.27 1.27)) hide))
      (symbol "Switch:SW_Push_0_1"
        (circle (center -2.032 0) (radius 0.508) (stroke (width 0) (type default)) (fill (type none)))
        (polyline (pts (xy 0 1.27) (xy 0 2.032)) (stroke (width 0) (type default)) (fill (type none)))
        (polyline (pts (xy -2.032 1.27) (xy 2.032 3.302)) (stroke (width 0) (type default)) (fill (type none)))
        (circle (center 2.032 0) (radius 0.508) (stroke (width 0) (type default)) (fill (type none))))
      (symbol "Switch:SW_Push_1_1"
        (pin passive line (at -5.08 0 0) (length 2.54)
          (name "1" (effects (font (size 1.27 1.27))))
          (number "1" (effects (font (size 1.27 1.27)))))
        (pin passive line (at 5.08 0 180) (length 2.54)
          (name "2" (effects (font (size 1.27 1.27))))
          (number "2" (effects (font (size 1.27 1.27)))))))
    (symbol "Connector:Conn_01x03" (pin_names (offset 1.016) hide) (in_bom yes) (on_board yes)
      (property "Reference" "J" (at 0 5.08 0) (effects (font (size 1.27 1.27))))
      (property "Value" "Conn_01x03" (at 0 -5.08 0) (effects (font (size 1.27 1.27))))
      (property "Footprint" "" (at 0 0 0) (effects (font (size 1.27 1.27)) hide))
      (property "Datasheet" "~" (at 0 0 0) (effects (font (size 1.27 1.27)) hide))
      (symbol "Connector:Conn_01x03_0_1"
        (rectangle (start -1.27 3.81) (end 1.27 -3.81)
          (stroke (width 0.254) (type default)) (fill (type none))))
      (symbol "Connector:Conn_01x03_1_1"
        (pin passive line (at 3.81 2.54 180) (length 2.54)
          (name "Pin_1" (effects (font (size 1.27 1.27))))
          (number "1" (effects (font (size 1.27 1.27)))))
        (pin passive line (at 3.81 0 180) (length 2.54)
          (name "Pin_2" (effects (font (size 1.27 1.27))))
          (number "2" (effects (font (size 1.27 1.27)))))
        (pin passive line (at 3.81 -2.54 180) (length 2.54)
          (name "Pin_3" (effects (font (size 1.27 1.27))))
          (number "3" (effects (font (size 1.27 1.27)))))))
""".strip()


def _pico2_lib_symbol() -> str:
    """Build the MCU:Pico2 40-pin module symbol inline.

    Pin layout matches RP2350 / Pico 2 module 2.54mm header:
      Left  pins 1..20  (top→bottom)
      Right pins 40..21 (top→bottom)
    """
    pins_left = [
        (1, "GP0", "bidirectional"),
        (2, "GP1", "bidirectional"),
        (3, "GND", "power_in"),
        (4, "GP2", "bidirectional"),
        (5, "GP3", "bidirectional"),
        (6, "GP4", "bidirectional"),
        (7, "GP5", "bidirectional"),
        (8, "GND", "power_in"),
        (9, "GP6", "bidirectional"),
        (10, "GP7", "bidirectional"),
        (11, "GP8", "bidirectional"),
        (12, "GP9", "bidirectional"),
        (13, "GND", "power_in"),
        (14, "GP10", "bidirectional"),
        (15, "GP11", "bidirectional"),
        (16, "GP12", "bidirectional"),
        (17, "GP13", "bidirectional"),
        (18, "GND", "power_in"),
        (19, "GP14", "bidirectional"),
        (20, "GP15", "bidirectional"),
    ]
    # Right side numbered top-down 40..21:
    pins_right = [
        (40, "VBUS", "power_in"),
        (39, "VSYS", "power_in"),
        (38, "GND", "power_in"),
        (37, "3V3_EN", "input"),
        (36, "3V3_OUT", "power_out"),
        (35, "ADC_VREF", "input"),
        (34, "GP28", "bidirectional"),
        (33, "AGND", "power_in"),
        (32, "GP27", "bidirectional"),
        (31, "GP26", "bidirectional"),
        (30, "RUN", "input"),
        (29, "GP22", "bidirectional"),
        (28, "GND", "power_in"),
        (27, "GP21", "bidirectional"),
        (26, "GP20", "bidirectional"),
        (25, "GP19", "bidirectional"),
        (24, "GP18", "bidirectional"),
        (23, "GND", "power_in"),
        (22, "GP17", "bidirectional"),
        (21, "GP16", "bidirectional"),
    ]
    # 20 pins per side × 2.54mm spacing centered on y=0
    y_top = 24.13  # = (20-1)*2.54/2
    rect_top = y_top + 2.54
    rect_bot = -y_top - 2.54
    out = ['    (symbol "MCU:Pico2" (in_bom yes) (on_board yes)']
    out.append('      (property "Reference" "U" (at 0 31.75 0) (effects (font (size 1.27 1.27))))')
    out.append('      (property "Value" "Raspberry_Pi_Pico2" (at 0 29.21 0) (effects (font (size 1.27 1.27))))')
    out.append('      (property "Footprint" "" (at 0 0 0) (effects (font (size 1.27 1.27)) hide))')
    out.append('      (property "Datasheet" "https://datasheets.raspberrypi.com/picow/pico-2-datasheet.pdf" (at 0 0 0) (effects (font (size 1.27 1.27)) hide))')
    out.append('      (symbol "MCU:Pico2_0_1"')
    out.append(f'        (rectangle (start -15 {rect_top}) (end 15 {rect_bot})')
    out.append('          (stroke (width 0.254) (type default)) (fill (type none))))')
    out.append('      (symbol "MCU:Pico2_1_1"')
    # left-side pins
    for idx, (num, name, ptype) in enumerate(pins_left):
        y = y_top - idx * 2.54
        out.append(
            f'        (pin {ptype} line (at -17.54 {y:.3f} 0) (length 2.54)\n'
            f'          (name "{name}" (effects (font (size 1.27 1.27))))\n'
            f'          (number "{num}" (effects (font (size 1.27 1.27)))))'
        )
    # right-side pins
    for idx, (num, name, ptype) in enumerate(pins_right):
        y = y_top - idx * 2.54
        out.append(
            f'        (pin {ptype} line (at 17.54 {y:.3f} 180) (length 2.54)\n'
            f'          (name "{name}" (effects (font (size 1.27 1.27))))\n'
            f'          (number "{num}" (effects (font (size 1.27 1.27)))))'
        )
    out.append('        )')
    out.append('      )')
    return "\n".join(out)


def _stm32h743_lib_symbol() -> str:
    """STM32H743VIT6 LQFP-100 — Pin-Daten 1:1 aus der offiziellen KiCad-Lib
    (KiCad/kicad-symbols MCU_ST_STM32H7, Symbol STM32H743VITx; generiert aus
    ST-CubeMX-Daten) und gegen SPEC v0.7 §5 / DS12110 Rev 5 Table 8 doppelt
    verifiziert: alle 52 in der SPEC belegten Zuordnungen stimmen überein."""
    out = []
    # r18.80 AUDIT-FIX (KRITISCH): lib_symbols-Name MUSS die Library-Nickname
    # tragen ("MCU:STM32H743VIT6") — die platzierte Instanz referenziert
    # lib_id "MCU:STM32H743VIT6", und KiCad matcht exakt gegen den
    # lib_symbols-Eintrag. Ohne Prefix konnte KiCad das MCU-Symbol nicht
    # aufloesen (U1 ohne Pins, kein Netlist-Export fuer den gesamten MCU).
    out.append('    (symbol "MCU:STM32H743VIT6" (pin_names (offset 0.508)) (in_bom yes) (on_board yes)')
    out.append('      (property "Reference" "U" (at 0 0 0) (effects (font (size 1.27 1.27))))')
    out.append('      (property "Value" "STM32H743VIT6" (at 0 -2.54 0) (effects (font (size 1.27 1.27)) hide))')
    out.append('      (symbol "STM32H743VIT6_0_1"')
    out.append('        (rectangle (start -17.78 63.5) (end 17.78 -66.04) (stroke (width 0.254) (type default)) (fill (type background)))')
    out.append('      )')
    out.append('      (symbol "STM32H743VIT6_1_1"')
    out.append('        (pin bidirectional line (at -22.86 12.7 0) (length 5.08)')
    out.append('          (name "PE2" (effects (font (size 1.27 1.27))))')
    out.append('          (number "1" (effects (font (size 1.27 1.27)))))')
    out.append('        (pin bidirectional line (at -22.86 10.16 0) (length 5.08)')
    out.append('          (name "PE3" (effects (font (size 1.27 1.27))))')
    out.append('          (number "2" (effects (font (size 1.27 1.27)))))')
    out.append('        (pin bidirectional line (at -22.86 7.62 0) (length 5.08)')
    out.append('          (name "PE4" (effects (font (size 1.27 1.27))))')
    out.append('          (number "3" (effects (font (size 1.27 1.27)))))')
    out.append('        (pin bidirectional line (at -22.86 5.08 0) (length 5.08)')
    out.append('          (name "PE5" (effects (font (size 1.27 1.27))))')
    out.append('          (number "4" (effects (font (size 1.27 1.27)))))')
    out.append('        (pin bidirectional line (at -22.86 2.54 0) (length 5.08)')
    out.append('          (name "PE6" (effects (font (size 1.27 1.27))))')
    out.append('          (number "5" (effects (font (size 1.27 1.27)))))')
    out.append('        (pin power_in line (at -7.62 68.58 270) (length 5.08)')
    out.append('          (name "VBAT" (effects (font (size 1.27 1.27))))')
    out.append('          (number "6" (effects (font (size 1.27 1.27)))))')
    out.append('        (pin bidirectional line (at 22.86 -58.42 180) (length 5.08)')
    out.append('          (name "PC13" (effects (font (size 1.27 1.27))))')
    out.append('          (number "7" (effects (font (size 1.27 1.27)))))')
    out.append('        (pin bidirectional line (at 22.86 -60.96 180) (length 5.08)')
    out.append('          (name "PC14" (effects (font (size 1.27 1.27))))')
    out.append('          (number "8" (effects (font (size 1.27 1.27)))))')
    out.append('        (pin bidirectional line (at 22.86 -63.5 180) (length 5.08)')
    out.append('          (name "PC15" (effects (font (size 1.27 1.27))))')
    out.append('          (number "9" (effects (font (size 1.27 1.27)))))')
    out.append('        (pin power_in line (at -7.62 -71.12 90) (length 5.08)')
    out.append('          (name "VSS" (effects (font (size 1.27 1.27))))')
    out.append('          (number "10" (effects (font (size 1.27 1.27)))))')
    out.append('        (pin power_in line (at -5.08 68.58 270) (length 5.08)')
    out.append('          (name "VDD" (effects (font (size 1.27 1.27))))')
    out.append('          (number "11" (effects (font (size 1.27 1.27)))))')
    out.append('        (pin input line (at -22.86 25.4 0) (length 5.08)')
    out.append('          (name "PH0" (effects (font (size 1.27 1.27))))')
    out.append('          (number "12" (effects (font (size 1.27 1.27)))))')
    out.append('        (pin input line (at -22.86 22.86 0) (length 5.08)')
    out.append('          (name "PH1" (effects (font (size 1.27 1.27))))')
    out.append('          (number "13" (effects (font (size 1.27 1.27)))))')
    out.append('        (pin input line (at -22.86 60.96 0) (length 5.08)')
    out.append('          (name "NRST" (effects (font (size 1.27 1.27))))')
    out.append('          (number "14" (effects (font (size 1.27 1.27)))))')
    out.append('        (pin bidirectional line (at 22.86 -25.4 180) (length 5.08)')
    out.append('          (name "PC0" (effects (font (size 1.27 1.27))))')
    out.append('          (number "15" (effects (font (size 1.27 1.27)))))')
    out.append('        (pin bidirectional line (at 22.86 -27.94 180) (length 5.08)')
    out.append('          (name "PC1" (effects (font (size 1.27 1.27))))')
    out.append('          (number "16" (effects (font (size 1.27 1.27)))))')
    out.append('        (pin bidirectional line (at 22.86 -30.48 180) (length 5.08)')
    out.append('          (name "PC2_C" (effects (font (size 1.27 1.27))))')
    out.append('          (number "17" (effects (font (size 1.27 1.27)))))')
    out.append('        (pin bidirectional line (at 22.86 -33.02 180) (length 5.08)')
    out.append('          (name "PC3_C" (effects (font (size 1.27 1.27))))')
    out.append('          (number "18" (effects (font (size 1.27 1.27)))))')
    out.append('        (pin power_in line (at 5.08 -71.12 90) (length 5.08)')
    out.append('          (name "VSSA" (effects (font (size 1.27 1.27))))')
    out.append('          (number "19" (effects (font (size 1.27 1.27)))))')
    out.append('        (pin bidirectional line (at -22.86 45.72 0) (length 5.08)')
    out.append('          (name "VREF+" (effects (font (size 1.27 1.27))))')
    out.append('          (number "20" (effects (font (size 1.27 1.27)))))')
    out.append('        (pin power_in line (at 7.62 68.58 270) (length 5.08)')
    out.append('          (name "VDDA" (effects (font (size 1.27 1.27))))')
    out.append('          (number "21" (effects (font (size 1.27 1.27)))))')
    out.append('        (pin bidirectional line (at 22.86 60.96 180) (length 5.08)')
    out.append('          (name "PA0" (effects (font (size 1.27 1.27))))')
    out.append('          (number "22" (effects (font (size 1.27 1.27)))))')
    out.append('        (pin bidirectional line (at 22.86 58.42 180) (length 5.08)')
    out.append('          (name "PA1" (effects (font (size 1.27 1.27))))')
    out.append('          (number "23" (effects (font (size 1.27 1.27)))))')
    out.append('        (pin bidirectional line (at 22.86 55.88 180) (length 5.08)')
    out.append('          (name "PA2" (effects (font (size 1.27 1.27))))')
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
    out.append('          (number "92" (effects (font (size 1.27 1.27)))))')
    out.append('        (pin bidirectional line (at 22.86 0.0 180) (length 5.08)')
    out.append('          (name "PB7" (effects (font (size 1.27 1.27))))')
    out.append('          (number "93" (effects (font (size 1.27 1.27)))))')
    out.append('        (pin input line (at -22.86 55.88 0) (length 5.08)')
    out.append('          (name "BOOT0" (effects (font (size 1.27 1.27))))')
    out.append('          (number "94" (effects (font (size 1.27 1.27)))))')
    out.append('        (pin bidirectional line (at 22.86 -2.54 180) (length 5.08)')
    out.append('          (name "PB8" (effects (font (size 1.27 1.27))))')
    out.append('          (number "95" (effects (font (size 1.27 1.27)))))')
    out.append('        (pin bidirectional line (at 22.86 -5.08 180) (length 5.08)')
    out.append('          (name "PB9" (effects (font (size 1.27 1.27))))')
    out.append('          (number "96" (effects (font (size 1.27 1.27)))))')
    out.append('        (pin bidirectional line (at -22.86 17.78 0) (length 5.08)')
    out.append('          (name "PE0" (effects (font (size 1.27 1.27))))')
    out.append('          (number "97" (effects (font (size 1.27 1.27)))))')
    out.append('        (pin bidirectional line (at -22.86 15.24 0) (length 5.08)')
    out.append('          (name "PE1" (effects (font (size 1.27 1.27))))')
    out.append('          (number "98" (effects (font (size 1.27 1.27)))))')
    out.append('        (pin power_in line (at 2.54 -71.12 90) (length 5.08)')
    out.append('          (name "VSS" (effects (font (size 1.27 1.27))))')
    out.append('          (number "99" (effects (font (size 1.27 1.27)))))')
    out.append('        (pin power_in line (at 5.08 68.58 270) (length 5.08)')
    out.append('          (name "VDD" (effects (font (size 1.27 1.27))))')
    out.append('          (number "100" (effects (font (size 1.27 1.27)))))')
    out.append('      )')
    out.append('    )')
    return '\n'.join(out)


# Pin-Kontaktpunkte des STM32H743VIT6-Symbols in Symbol-Lokalkoordinaten (mm,
# Y-UP wie lib_symbols). Verdrahtung im Sheet rechnet via pin_abs() um.
# orient: 0=Pin zeigt nach rechts (linke Symbolseite), 180=links (rechte Seite),
# 90=nach oben (Unterseite), 270=nach unten (Oberseite).
STM32_PIN_LOC = {
    1: (-22.86, 12.7, 0),  # PE2
    2: (-22.86, 10.16, 0),  # PE3
    3: (-22.86, 7.62, 0),  # PE4
    4: (-22.86, 5.08, 0),  # PE5
    5: (-22.86, 2.54, 0),  # PE6
    6: (-7.62, 68.58, 270),  # VBAT
    7: (22.86, -58.42, 180),  # PC13
    8: (22.86, -60.96, 180),  # PC14
    9: (22.86, -63.5, 180),  # PC15
    10: (-7.62, -71.12, 90),  # VSS
    11: (-5.08, 68.58, 270),  # VDD
    12: (-22.86, 25.4, 0),  # PH0
    13: (-22.86, 22.86, 0),  # PH1
    14: (-22.86, 60.96, 0),  # NRST
    15: (22.86, -25.4, 180),  # PC0
    16: (22.86, -27.94, 180),  # PC1
    17: (22.86, -30.48, 180),  # PC2_C
    18: (22.86, -33.02, 180),  # PC3_C
    19: (5.08, -71.12, 90),  # VSSA
    20: (-22.86, 45.72, 0),  # VREF+
    21: (7.62, 68.58, 270),  # VDDA
    22: (22.86, 60.96, 180),  # PA0
    23: (22.86, 58.42, 180),  # PA1
    24: (22.86, 55.88, 180),  # PA2
    25: (22.86, 53.34, 180),  # PA3
    26: (-5.08, -71.12, 90),  # VSS
    27: (-2.54, 68.58, 270),  # VDD
    28: (22.86, 50.8, 180),  # PA4
    29: (22.86, 48.26, 180),  # PA5
    30: (22.86, 45.72, 180),  # PA6
    31: (22.86, 43.18, 180),  # PA7
    32: (22.86, -35.56, 180),  # PC4
    33: (22.86, -38.1, 180),  # PC5
    34: (22.86, 17.78, 180),  # PB0
    35: (22.86, 15.24, 180),  # PB1
    36: (22.86, 12.7, 180),  # PB2
    37: (-22.86, 0.0, 0),  # PE7
    38: (-22.86, -2.54, 0),  # PE8
    39: (-22.86, -5.08, 0),  # PE9
    40: (-22.86, -7.62, 0),  # PE10
    41: (-22.86, -10.16, 0),  # PE11
    42: (-22.86, -12.7, 0),  # PE12
    43: (-22.86, -15.24, 0),  # PE13
    44: (-22.86, -17.78, 0),  # PE14
    45: (-22.86, -20.32, 0),  # PE15
    46: (22.86, -7.62, 180),  # PB10
    47: (22.86, -10.16, 180),  # PB11
    48: (-22.86, 50.8, 0),  # VCAP1
    49: (-2.54, -71.12, 90),  # VSS
    50: (0.0, 68.58, 270),  # VDD
    51: (22.86, -12.7, 180),  # PB12
    52: (22.86, -15.24, 180),  # PB13
    53: (22.86, -17.78, 180),  # PB14
    54: (22.86, -20.32, 180),  # PB15
    55: (-22.86, -45.72, 0),  # PD8
    56: (-22.86, -48.26, 0),  # PD9
    57: (-22.86, -50.8, 0),  # PD10
    58: (-22.86, -53.34, 0),  # PD11
    59: (-22.86, -55.88, 0),  # PD12
    60: (-22.86, -58.42, 0),  # PD13
    61: (-22.86, -60.96, 0),  # PD14
    62: (-22.86, -63.5, 0),  # PD15
    63: (22.86, -40.64, 180),  # PC6
    64: (22.86, -43.18, 180),  # PC7
    65: (22.86, -45.72, 180),  # PC8
    66: (22.86, -48.26, 180),  # PC9
    67: (22.86, 40.64, 180),  # PA8
    68: (22.86, 38.1, 180),  # PA9
    69: (22.86, 35.56, 180),  # PA10
    70: (22.86, 33.02, 180),  # PA11
    71: (22.86, 30.48, 180),  # PA12
    72: (22.86, 27.94, 180),  # PA13
    73: (-22.86, 48.26, 0),  # VCAP2
    74: (0.0, -71.12, 90),  # VSS
    75: (2.54, 68.58, 270),  # VDD
    76: (22.86, 25.4, 180),  # PA14
    77: (22.86, 22.86, 180),  # PA15
    78: (22.86, -50.8, 180),  # PC10
    79: (22.86, -53.34, 180),  # PC11
    80: (22.86, -55.88, 180),  # PC12
    81: (-22.86, -25.4, 0),  # PD0
    82: (-22.86, -27.94, 0),  # PD1
    83: (-22.86, -30.48, 0),  # PD2
    84: (-22.86, -33.02, 0),  # PD3
    85: (-22.86, -35.56, 0),  # PD4
    86: (-22.86, -38.1, 0),  # PD5
    87: (-22.86, -40.64, 0),  # PD6
    88: (-22.86, -43.18, 0),  # PD7
    89: (22.86, 10.16, 180),  # PB3
    90: (22.86, 7.62, 180),  # PB4
    91: (22.86, 5.08, 180),  # PB5
    92: (22.86, 2.54, 180),  # PB6
    93: (22.86, 0.0, 180),  # PB7
    94: (-22.86, 55.88, 0),  # BOOT0
    95: (22.86, -2.54, 180),  # PB8
    96: (22.86, -5.08, 180),  # PB9
    97: (-22.86, 17.78, 0),  # PE0
    98: (-22.86, 15.24, 0),  # PE1
    99: (2.54, -71.12, 90),  # VSS
    100: (5.08, 68.58, 270),  # VDD
}


# ============================================================================
# r18 (H7-Migration Phase 3): Hilfs-Symbole + Sheets für STM32H743
# ============================================================================


def no_connect(x: float, y: float) -> str:
    return (
        f'  (no_connect (at {x} {y})\n'
        f"    (uuid \"{det_uuid(f'nc/{x},{y}')}\"))\n"
    )


def _crystal_lib_symbol() -> str:
    """Device:Crystal-äquivalent (2-Pin, kein GND-Body) für Y1 HSE."""
    out = []
    out.append('    (symbol "Device:Crystal" (pin_numbers hide) (pin_names (offset 1.016) hide) (in_bom yes) (on_board yes)')
    out.append('      (property "Reference" "Y" (at 0 3.81 0) (effects (font (size 1.27 1.27))))')
    out.append('      (property "Value" "Crystal" (at 0 -3.81 0) (effects (font (size 1.27 1.27)) hide))')
    out.append('      (symbol "Device:Crystal_0_1"')
    out.append('        (rectangle (start -1.143 2.54) (end 1.143 -2.54) (stroke (width 0.3048) (type default)) (fill (type none)))')
    out.append('        (polyline (pts (xy -2.032 1.27) (xy -2.032 -1.27)) (stroke (width 0.508) (type default)) (fill (type none)))')
    out.append('        (polyline (pts (xy 2.032 1.27) (xy 2.032 -1.27)) (stroke (width 0.508) (type default)) (fill (type none)))')
    out.append('      )')
    out.append('      (symbol "Device:Crystal_1_1"')
    out.append('        (pin passive line (at -5.08 0 0) (length 3.048)')
    out.append('          (name "1" (effects (font (size 1.27 1.27))))')
    out.append('          (number "1" (effects (font (size 1.27 1.27)))))')
    out.append('        (pin passive line (at 5.08 0 180) (length 3.048)')
    out.append('          (name "2" (effects (font (size 1.27 1.27))))')
    out.append('          (number "2" (effects (font (size 1.27 1.27)))))')
    out.append('      )')
    out.append('    )')
    return "\n".join(out)


def _ap7361c_lib_symbol() -> str:
    """AP7361C 1A LDO, SOT-89-5 (Diodes Inc.).

    r18.6: Symbol auf AP7361C umgestellt. AP7361 ist laut Diodes-Datasheet
    NRND („Not Recommended For New Designs — Use AP7361C"). AP7361C nutzt für
    SOT-89-5 dasselbe Pin-Mapping.

    OFFIZIELLES PINOUT SOT-89-5 (Diodes AP7361 / AP7361C Datasheet,
    via Mouser-CDN, vom User verifiziert und im PR verlinkt):

        Pin 1 = EN
        Pin 2 = GND
        Pin 3 = ADJ/NC
        Pin 4 = IN
        Pin 5 = OUT

    Frühere r18.5-Annahme (1=ADJ/NC,2=OUT,3=IN,4=GND,5=EN) war FALSCH und
    hätte IN/OUT/EN vertauscht. Quelle: mouser.de/datasheet/3/175/1/AP7361.pdf

    Footprint: Package_TO_SOT_SMD:SOT-89-5. KEIN SOT-223 (AP7361-33E-13 /
    C150719 ist SOT-223 und passt NICHT zu diesem Symbol).
    """
    out = []
    out.append('    (symbol "Regulator_Linear:AP7361C" (pin_names (offset 0.508)) (in_bom yes) (on_board yes)')
    out.append('      (property "Reference" "U" (at 0 6.35 0) (effects (font (size 1.27 1.27))))')
    out.append('      (property "Value" "AP7361C" (at 0 -8.89 0) (effects (font (size 1.27 1.27)) hide))')
    out.append('      (symbol "Regulator_Linear:AP7361C_0_1"')
    out.append('        (rectangle (start -6.35 5.08) (end 6.35 -6.35) (stroke (width 0.254) (type default)) (fill (type background)))')
    out.append('      )')
    out.append('      (symbol "Regulator_Linear:AP7361C_1_1"')
    # Linke Seite (Eingänge): EN oben, IN unten
    out.append('        (pin input line (at -8.89 2.54 0) (length 2.54)')
    out.append('          (name "EN" (effects (font (size 1.27 1.27))))')
    out.append('          (number "1" (effects (font (size 1.27 1.27)))))')
    out.append('        (pin power_in line (at -8.89 -2.54 0) (length 2.54)')
    out.append('          (name "IN" (effects (font (size 1.27 1.27))))')
    out.append('          (number "4" (effects (font (size 1.27 1.27)))))')
    # Rechte Seite (Ausgänge): OUT oben, ADJ/NC unten
    out.append('        (pin power_out line (at 8.89 2.54 180) (length 2.54)')
    out.append('          (name "OUT" (effects (font (size 1.27 1.27))))')
    out.append('          (number "5" (effects (font (size 1.27 1.27)))))')
    out.append('        (pin no_connect line (at 8.89 -2.54 180) (length 2.54)')
    out.append('          (name "ADJ/NC" (effects (font (size 1.27 1.27))))')
    out.append('          (number "3" (effects (font (size 1.27 1.27)))))')
    # Untere Seite: GND
    out.append('        (pin power_in line (at 0 -8.89 90) (length 2.54)')
    out.append('          (name "GND" (effects (font (size 1.27 1.27))))')
    out.append('          (number "2" (effects (font (size 1.27 1.27)))))')
    out.append('      )')
    out.append('    )')
    return "\n".join(out)


def _nmos_sot23_lib_symbol() -> str:
    """N-Kanal-MOSFET SOT-23 (2N7002) für LCD-Backlight-Low-Side-Switch.
    Pin-Zuordnung 1=G, 2=S, 3=D = JEDEC-TO-236-Standardbelegung des 2N7002
    (FP_VERIFY: gegen Hersteller-Datasheet der bestückten Marke prüfen)."""
    out = []
    out.append('    (symbol "Transistor_FET:Q_NMOS_GSD" (pin_names (offset 0.254) hide) (in_bom yes) (on_board yes)')
    out.append('      (property "Reference" "Q" (at 5.08 1.27 0) (effects (font (size 1.27 1.27))))')
    out.append('      (property "Value" "Q_NMOS_GSD" (at 5.08 -1.27 0) (effects (font (size 1.27 1.27)) hide))')
    out.append('      (symbol "Transistor_FET:Q_NMOS_GSD_0_1"')
    out.append('        (polyline (pts (xy 0.254 1.778) (xy 0.254 -1.778)) (stroke (width 0.254) (type default)) (fill (type none)))')
    out.append('        (polyline (pts (xy 0.762 1.27) (xy 0.762 -1.27)) (stroke (width 0.254) (type default)) (fill (type none)))')
    out.append('        (polyline (pts (xy 0.762 0) (xy 2.54 0)) (stroke (width 0) (type default)) (fill (type none)))')
    out.append('        (polyline (pts (xy 2.54 1.27) (xy 0.762 1.27)) (stroke (width 0) (type default)) (fill (type none)))')
    out.append('        (polyline (pts (xy 2.54 -1.27) (xy 0.762 -1.27)) (stroke (width 0) (type default)) (fill (type none)))')
    out.append('      )')
    out.append('      (symbol "Transistor_FET:Q_NMOS_GSD_1_1"')
    out.append('        (pin input line (at -2.54 0 0) (length 2.794)')
    out.append('          (name "G" (effects (font (size 1.27 1.27))))')
    out.append('          (number "1" (effects (font (size 1.27 1.27)))))')
    out.append('        (pin passive line (at 2.54 -3.81 90) (length 2.54)')
    out.append('          (name "S" (effects (font (size 1.27 1.27))))')
    out.append('          (number "2" (effects (font (size 1.27 1.27)))))')
    out.append('        (pin passive line (at 2.54 3.81 270) (length 2.54)')
    out.append('          (name "D" (effects (font (size 1.27 1.27))))')
    out.append('          (number "3" (effects (font (size 1.27 1.27)))))')
    out.append('      )')
    out.append('    )')
    return "\n".join(out)


def _conn_01xN_lib_symbol(n: int) -> str:
    """Generic N-pin 1-row header symbol (pin 1 at top in lib Y-UP).

    Pin local positions: x=+3.81, y=+top..-bottom (KiCad Y-UP). Pin angle 180.
    Pins display from top (pin 1) to bottom (pin N) with 2.54mm spacing.
    """
    y_top = (n - 1) * 1.27  # half of (n-1)*2.54
    rect_top = y_top + 2.54
    rect_bot = -y_top - 2.54
    out = [f'    (symbol "Connector:Conn_01x{n:02d}" (pin_names (offset 1.016) hide) (in_bom yes) (on_board yes)']
    out.append(f'      (property "Reference" "J" (at 0 {rect_top + 1.27} 0) (effects (font (size 1.27 1.27))))')
    out.append(f'      (property "Value" "Conn_01x{n:02d}" (at 0 {rect_bot - 1.27} 0) (effects (font (size 1.27 1.27))))')
    out.append('      (property "Footprint" "" (at 0 0 0) (effects (font (size 1.27 1.27)) hide))')
    out.append('      (property "Datasheet" "~" (at 0 0 0) (effects (font (size 1.27 1.27)) hide))')
    out.append(f'      (symbol "Connector:Conn_01x{n:02d}_0_1"')
    out.append(f'        (rectangle (start -1.27 {rect_top}) (end 1.27 {rect_bot})')
    out.append('          (stroke (width 0.254) (type default)) (fill (type none))))')
    out.append(f'      (symbol "Connector:Conn_01x{n:02d}_1_1"')
    for idx in range(n):
        ly = y_top - idx * 2.54
        pin_num = idx + 1
        out.append(
            f'        (pin passive line (at 3.81 {ly:.3f} 180) (length 2.54)\n'
            f'          (name "Pin_{pin_num}" (effects (font (size 1.27 1.27))))\n'
            f'          (number "{pin_num}" (effects (font (size 1.27 1.27)))))'
        )
    out.append('        )')
    out.append('      )')
    return "\n".join(out)


def _mcp23017_lib_symbol() -> str:
    """MCP23017 SSOP-28 I/O-Expander. 14 Pins pro Seite. Chip-Pinout-Layout:
    Left (top→bottom): GPB0-7, VDD, VSS, NC, SCL, SDA, NC = pins 1..14
    Right (top→bottom): GPA7..GPA0, INTA, INTB, ~RESET, A2, A1, A0 = pins 28..15
    """
    pins_left = [
        (1, "GPB0", "bidirectional"),
        (2, "GPB1", "bidirectional"),
        (3, "GPB2", "bidirectional"),
        (4, "GPB3", "bidirectional"),
        (5, "GPB4", "bidirectional"),
        (6, "GPB5", "bidirectional"),
        (7, "GPB6", "bidirectional"),
        (8, "GPB7", "bidirectional"),
        (9, "VDD", "power_in"),
        (10, "VSS", "power_in"),
        (11, "NC", "no_connect"),
        (12, "SCL", "input"),
        (13, "SDA", "bidirectional"),
        (14, "NC", "no_connect"),
    ]
    pins_right = [
        (28, "GPA7", "bidirectional"),
        (27, "GPA6", "bidirectional"),
        (26, "GPA5", "bidirectional"),
        (25, "GPA4", "bidirectional"),
        (24, "GPA3", "bidirectional"),
        (23, "GPA2", "bidirectional"),
        (22, "GPA1", "bidirectional"),
        (21, "GPA0", "bidirectional"),
        (20, "INTA", "output"),
        (19, "INTB", "output"),
        (18, "~RESET", "input"),
        (17, "A2", "input"),
        (16, "A1", "input"),
        (15, "A0", "input"),
    ]
    y_top = 16.51  # (14-1)*2.54/2 = 16.51
    rect_top = y_top + 2.54
    rect_bot = -y_top - 2.54
    out = ['    (symbol "MCU:MCP23017" (in_bom yes) (on_board yes)']
    out.append(f'      (property "Reference" "U" (at 0 {rect_top + 1.27} 0) (effects (font (size 1.27 1.27))))')
    out.append(f'      (property "Value" "MCP23017-E_SS" (at 0 {rect_bot - 1.27} 0) (effects (font (size 1.27 1.27))))')
    out.append('      (property "Footprint" "" (at 0 0 0) (effects (font (size 1.27 1.27)) hide))')
    out.append('      (property "Datasheet" "https://ww1.microchip.com/downloads/en/DeviceDoc/20001952C.pdf" (at 0 0 0) (effects (font (size 1.27 1.27)) hide))')
    out.append('      (symbol "MCU:MCP23017_0_1"')
    out.append(f'        (rectangle (start -10.16 {rect_top}) (end 10.16 {rect_bot})')
    out.append('          (stroke (width 0.254) (type default)) (fill (type none))))')
    out.append('      (symbol "MCU:MCP23017_1_1"')
    for idx, (num, name, ptype) in enumerate(pins_left):
        ly = y_top - idx * 2.54
        out.append(
            f'        (pin {ptype} line (at -12.7 {ly:.3f} 0) (length 2.54)\n'
            f'          (name "{name}" (effects (font (size 1.27 1.27))))\n'
            f'          (number "{num}" (effects (font (size 1.27 1.27)))))'
        )
    for idx, (num, name, ptype) in enumerate(pins_right):
        ly = y_top - idx * 2.54
        out.append(
            f'        (pin {ptype} line (at 12.7 {ly:.3f} 180) (length 2.54)\n'
            f'          (name "{name}" (effects (font (size 1.27 1.27))))\n'
            f'          (number "{num}" (effects (font (size 1.27 1.27)))))'
        )
    out.append('        )')
    out.append('      )')
    return "\n".join(out)


def _pca9685pw_lib_symbol() -> str:
    """PCA9685PW TSSOP-28 16-channel I²C PWM LED-driver (NXP).

    Pin-Map per NXP Datasheet Rev 4 (16-April-2015) Table 3 + Fig. 2:
    Left (top→bottom, pins 1..14):
        1=A0  2=A1  3=A2  4=A3  5=A4  6=LED0  7=LED1  8=LED2  9=LED3 10=LED4
        11=LED5 12=LED6 13=LED7 14=VSS
    Right (top→bottom, pins 28..15):
        28=VDD 27=SDA 26=SCL 25=EXTCLK 24=A5 23=~OE 22=LED15 21=LED14
        20=LED13 19=LED12 18=LED11 17=LED10 16=LED9 15=LED8

    Pin-Body-Geometry mirrors MCP23017 (also 28-pin TSSOP/SSOP), 2.54 mm pitch.
    """
    pins_left = [
        (1, "A0", "input"),
        (2, "A1", "input"),
        (3, "A2", "input"),
        (4, "A3", "input"),
        (5, "A4", "input"),
        (6, "LED0", "output"),
        (7, "LED1", "output"),
        (8, "LED2", "output"),
        (9, "LED3", "output"),
        (10, "LED4", "output"),
        (11, "LED5", "output"),
        (12, "LED6", "output"),
        (13, "LED7", "output"),
        (14, "VSS", "power_in"),
    ]
    pins_right = [
        (28, "VDD", "power_in"),
        (27, "SDA", "bidirectional"),
        (26, "SCL", "input"),
        (25, "EXTCLK", "input"),
        (24, "A5", "input"),
        (23, "~OE", "input"),
        (22, "LED15", "output"),
        (21, "LED14", "output"),
        (20, "LED13", "output"),
        (19, "LED12", "output"),
        (18, "LED11", "output"),
        (17, "LED10", "output"),
        (16, "LED9", "output"),
        (15, "LED8", "output"),
    ]
    y_top = 16.51  # 14-Pin column → ((14-1)*2.54)/2 = 16.51
    rect_top = y_top + 2.54
    rect_bot = -y_top - 2.54
    out = ['    (symbol "Driver_LED:PCA9685PW" (in_bom yes) (on_board yes)']
    out.append(f'      (property "Reference" "U" (at 0 {rect_top + 1.27} 0) (effects (font (size 1.27 1.27))))')
    out.append(f'      (property "Value" "PCA9685PW" (at 0 {rect_bot - 1.27} 0) (effects (font (size 1.27 1.27))))')
    out.append('      (property "Footprint" "" (at 0 0 0) (effects (font (size 1.27 1.27)) hide))')
    out.append('      (property "Datasheet" "https://www.nxp.com/docs/en/data-sheet/PCA9685.pdf" (at 0 0 0) (effects (font (size 1.27 1.27)) hide))')
    out.append('      (symbol "Driver_LED:PCA9685PW_0_1"')
    out.append(f'        (rectangle (start -10.16 {rect_top}) (end 10.16 {rect_bot})')
    out.append('          (stroke (width 0.254) (type default)) (fill (type none))))')
    out.append('      (symbol "Driver_LED:PCA9685PW_1_1"')
    for idx, (num, name, ptype) in enumerate(pins_left):
        ly = y_top - idx * 2.54
        out.append(
            f'        (pin {ptype} line (at -12.7 {ly:.3f} 0) (length 2.54)\n'
            f'          (name "{name}" (effects (font (size 1.27 1.27))))\n'
            f'          (number "{num}" (effects (font (size 1.27 1.27)))))'
        )
    for idx, (num, name, ptype) in enumerate(pins_right):
        ly = y_top - idx * 2.54
        out.append(
            f'        (pin {ptype} line (at 12.7 {ly:.3f} 180) (length 2.54)\n'
            f'          (name "{name}" (effects (font (size 1.27 1.27))))\n'
            f'          (number "{num}" (effects (font (size 1.27 1.27)))))'
        )
    out.append('        )')
    out.append('      )')
    return "\n".join(out)


def _bq24074_lib_symbol() -> str:
    """BQ24074RGTR — 1.5A Single-Cell Li-Ion Charger mit Power-Path (DPPM),
    VQFN-16 RGT (3x3mm, 0.5mm Pitch, EP 1.7x1.7). r19.18 (ADR-0023): ersetzt
    MCP73831 + D3B-Dioden-OR (Audit P0-1..P0-7).

    Pin-Map VERIFIED gegen TI SLUS810N (Okt 2021), Table 7-1 "Pin Functions",
    Spalte '74 (BQ24074 = RGT0016B, Figure 7-2):
      1=TS  2=BAT  3=BAT  4=CE(aktiv-low)  5=EN2  6=EN1  7=PGOOD(OD)  8=VSS
      9=CHG(OD)  10=OUT  11=OUT  12=ILIM  13=IN  14=TMR  15=ITERM  16=ISET
      17=EP (Thermal Pad, muss auf VSS-Potential)
    """
    pins_left = [
        (13, "IN",     "power_in", 10.16),
        (6,  "EN1",    "input",     7.62),
        (5,  "EN2",    "input",     5.08),
        (4,  "CE_N",   "input",     2.54),
        (12, "ILIM",   "input",     0.0),
        (16, "ISET",   "input",    -2.54),
        (15, "ITERM",  "input",    -5.08),
        (14, "TMR",    "input",    -7.62),
        (1,  "TS",     "input",   -10.16),
    ]
    pins_right = [
        (10, "OUT",     "power_out",      10.16),
        (11, "OUT",     "power_out",       7.62),
        (2,  "BAT",     "passive",         5.08),
        (3,  "BAT",     "passive",         2.54),
        (9,  "CHG_N",   "open_collector", -2.54),
        (7,  "PGOOD_N", "open_collector", -5.08),
        (8,  "VSS",     "power_in",      -10.16),
        (17, "EP",      "passive",       -12.70),
    ]
    out = ['    (symbol "Battery:BQ24074" (in_bom yes) (on_board yes)']
    out.append('      (property "Reference" "U" (at 0 13.97 0) (effects (font (size 1.27 1.27))))')
    out.append('      (property "Value" "BQ24074RGTR" (at 0 -16.51 0) (effects (font (size 1.27 1.27))))')
    out.append('      (property "Footprint" "" (at 0 0 0) (effects (font (size 1.27 1.27)) hide))')
    out.append('      (property "Datasheet" "https://www.ti.com/lit/ds/symlink/bq24074.pdf" (at 0 0 0) (effects (font (size 1.27 1.27)) hide))')
    out.append('      (symbol "Battery:BQ24074_0_1"')
    out.append('        (rectangle (start -7.62 12.7) (end 7.62 -14.605)')
    out.append('          (stroke (width 0.254) (type default)) (fill (type none))))')
    out.append('      (symbol "Battery:BQ24074_1_1"')
    for num, name, ptype, py in pins_left:
        out.append(
            f'        (pin {ptype} line (at -10.16 {py:.3f} 0) (length 2.54)\n'
            f'          (name "{name}" (effects (font (size 1.27 1.27))))\n'
            f'          (number "{num}" (effects (font (size 1.27 1.27)))))'
        )
    for num, name, ptype, py in pins_right:
        out.append(
            f'        (pin {ptype} line (at 10.16 {py:.3f} 180) (length 2.54)\n'
            f'          (name "{name}" (effects (font (size 1.27 1.27))))\n'
            f'          (number "{num}" (effects (font (size 1.27 1.27)))))'
        )
    out.append('        )')
    out.append('      )')
    return "\n".join(out)


def _tpa6132a2_lib_symbol() -> str:
    """TPA6132A2RTER — 25mW DirectPath Stereo-Kopfhoererverstaerker,
    WQFN-16 RTE (3x3mm, 0.5mm Pitch, EP 1.68). r19.19 (ADR-0024).

    Pin-Map VERIFIED gegen TI SLOS597B (Juli 2017), Pin Functions Tabelle:
      1=INL- 2=INL+ 3=INR+ 4=INR- 5=OUTR 6=G0 7=G1 8=HPVSS 9=CPN 10=PGND
      11=CPP 12=HPVDD 13=EN 14=VDD 15=SGND 16=OUTL 17=EP (GND oder floatend)
    Gain via G0/G1 (Table 1): LL=-6dB LH(G1)=+3dB HL(G0)=0dB HH=+6dB.
    EN: high=an (VIH 1.3V), low=Shutdown (0.7-1.2µA).
    DirectPath: interne Ladungspumpe (CPP/CPN-Flying-Cap + HPVSS-Cap)
    erzeugt die negative Rail — Ausgaenge ground-zentriert, KEINE
    Auskoppel-Elkos. HPVDD NIE an VDD anschliessen (DS-WARNING).
    """
    pins_left = [
        (1,  "INL-", "input", 10.16),
        (2,  "INL+", "input",  7.62),
        (3,  "INR+", "input",  5.08),
        (4,  "INR-", "input",  2.54),
        (13, "EN",   "input",  0.0),
        (6,  "G0",   "input", -2.54),
        (7,  "G1",   "input", -5.08),
    ]
    pins_right = [
        (16, "OUTL",  "output",   10.16),
        (5,  "OUTR",  "output",    7.62),
        (14, "VDD",   "power_in",  5.08),
        (12, "HPVDD", "passive",   2.54),
        (11, "CPP",   "passive",   0.0),
        (9,  "CPN",   "passive",  -2.54),
        (8,  "HPVSS", "passive",  -5.08),
        (15, "SGND",  "power_in", -7.62),
        (10, "PGND",  "power_in", -10.16),
        (17, "EP",    "passive",  -12.70),
    ]
    out = ['    (symbol "Audio:TPA6132A2" (in_bom yes) (on_board yes)']
    out.append('      (property "Reference" "U" (at 0 13.97 0) (effects (font (size 1.27 1.27))))')
    out.append('      (property "Value" "TPA6132A2RTER" (at 0 -16.51 0) (effects (font (size 1.27 1.27))))')
    out.append('      (property "Footprint" "" (at 0 0 0) (effects (font (size 1.27 1.27)) hide))')
    out.append('      (property "Datasheet" "https://www.ti.com/lit/ds/symlink/tpa6132a2.pdf" (at 0 0 0) (effects (font (size 1.27 1.27)) hide))')
    out.append('      (symbol "Audio:TPA6132A2_0_1"')
    out.append('        (rectangle (start -7.62 12.7) (end 7.62 -14.605)')
    out.append('          (stroke (width 0.254) (type default)) (fill (type none))))')
    out.append('      (symbol "Audio:TPA6132A2_1_1"')
    for num, name, ptype, py in pins_left:
        out.append(
            f'        (pin {ptype} line (at -10.16 {py:.3f} 0) (length 2.54)\n'
            f'          (name "{name}" (effects (font (size 1.27 1.27))))\n'
            f'          (number "{num}" (effects (font (size 1.27 1.27)))))'
        )
    for num, name, ptype, py in pins_right:
        out.append(
            f'        (pin {ptype} line (at 10.16 {py:.3f} 180) (length 2.54)\n'
            f'          (name "{name}" (effects (font (size 1.27 1.27))))\n'
            f'          (number "{num}" (effects (font (size 1.27 1.27)))))'
        )
    out.append('        )')
    out.append('      )')
    return "\n".join(out)


def _tps61089_lib_symbol() -> str:
    """TPS61089RNR — Boost Converter LiPo→5V, VQFN-11 HotRod 2×2.5mm + Thermal Pad.
    Per TI Datasheet SLVSD38C Table 6-1 (LCSC C165129):
    Pin 1: FSW    — switching-frequency programming resistor (to SW pin)
    Pin 2: VCC    — internal LDO output, requires ≥1µF cap to GND
    Pin 3: FB     — output voltage feedback
    Pin 4: COMP   — error amplifier output, compensation network to GND
    Pin 5: GND    — power-in / quiet ground
    Pin 6: VOUT   — boost converter output
    Pin 7: EN     — enable input (HIGH = on)
    Pin 8: ILIM   — current-limit programming resistor (to GND)
    Pin 9: VIN    — IC power supply input
    Pin 10: BOOT  — high-side gate driver bootstrap (cap to SW)
    Pin 11: SW    — switch node (to inductor)
    Plus thermal pad (treated as pin 12 = GND).

    HINWEIS r12-B11: SPEC-Wechsel von TPS61089RNSR (QFN-12 3×3) auf
    TPS61089RNR (VQFN-11 HotRod 2×2.5) wegen JLC-Stock-Verfügbarkeit
    (RNSR nicht bei LCSC). RNR-Variante braucht 5 zusätzliche externe
    Bauteile (C_VCC, R_FSW, R_ILIM, C_BOOT, R_COMP+C_COMP).
    """
    pins_left = [
        (1, "FSW", "input"),
        (2, "VCC", "power_out"),
        (3, "FB", "input"),
        (4, "COMP", "output"),
        (5, "GND", "power_in"),
        (6, "VOUT", "power_out"),
    ]
    pins_right = [
        (11, "SW", "passive"),
        (10, "BOOT", "output"),
        (9, "VIN", "power_in"),
        (8, "ILIM", "output"),
        (7, "EN", "input"),
    ]
    y_top = 6.35  # 6 pins per side max
    rect_top = y_top + 2.54
    rect_bot = -y_top - 2.54
    out = ['    (symbol "Regulator_Switching:TPS61089" (in_bom yes) (on_board yes)']
    out.append(f'      (property "Reference" "U" (at 0 {rect_top + 1.27} 0) (effects (font (size 1.27 1.27))))')
    out.append(f'      (property "Value" "TPS61089RNR" (at 0 {rect_bot - 1.27} 0) (effects (font (size 1.27 1.27))))')
    out.append('      (property "Footprint" "" (at 0 0 0) (effects (font (size 1.27 1.27)) hide))')
    out.append('      (property "Datasheet" "https://www.ti.com/lit/ds/symlink/tps61089.pdf" (at 0 0 0) (effects (font (size 1.27 1.27)) hide))')
    out.append('      (symbol "Regulator_Switching:TPS61089_0_1"')
    out.append(f'        (rectangle (start -7.62 {rect_top}) (end 7.62 {rect_bot})')
    out.append('          (stroke (width 0.254) (type default)) (fill (type none))))')
    out.append('      (symbol "Regulator_Switching:TPS61089_1_1"')
    for idx, (num, name, ptype) in enumerate(pins_left):
        ly = y_top - idx * 2.54
        out.append(
            f'        (pin {ptype} line (at -10.16 {ly:.3f} 0) (length 2.54)\n'
            f'          (name "{name}" (effects (font (size 1.27 1.27))))\n'
            f'          (number "{num}" (effects (font (size 1.27 1.27)))))'
        )
    for idx, (num, name, ptype) in enumerate(pins_right):
        ly = y_top - idx * 2.54
        out.append(
            f'        (pin {ptype} line (at 10.16 {ly:.3f} 180) (length 2.54)\n'
            f'          (name "{name}" (effects (font (size 1.27 1.27))))\n'
            f'          (number "{num}" (effects (font (size 1.27 1.27)))))'
        )
    # r18.7 CORRECTION: RNR0011A has NO separate exposed thermal pad.
    # The central large pad IS pin 11 (SW), per TI datasheet Pin Configuration
    # diagram. The old generator created a fake "pin 12 = ePAD = GND" — but
    # that pad doesn't exist in the package. SW (pin 11) carries both the
    # switching current and the thermal duty. GND is taken via pin 5 (one of
    # the enlarged side pads).
    out.append('        )')
    out.append('      )')
    return "\n".join(out)


def _dmg2305ux_lib_symbol() -> str:
    """DMG2305UX — P-Channel MOSFET, SOT-23, 3 Pins.
    Per Diodes Inc DS39061 Page 1:
    Pin 1: G (Gate, input)
    Pin 2: S (Source, passive)
    Pin 3: D (Drain, passive)
    """
    pins = [
        (1, "G", "input", -7.62, 0.0, 0),
        (2, "S", "passive", 7.62, 2.54, 180),
        (3, "D", "passive", 7.62, -2.54, 180),
    ]
    out = ['    (symbol "Transistor_FET:DMG2305UX" (in_bom yes) (on_board yes)']
    out.append('      (property "Reference" "Q" (at 0 5.08 0) (effects (font (size 1.27 1.27))))')
    out.append('      (property "Value" "DMG2305UX" (at 0 -5.08 0) (effects (font (size 1.27 1.27))))')
    out.append('      (property "Footprint" "" (at 0 0 0) (effects (font (size 1.27 1.27)) hide))')
    out.append('      (property "Datasheet" "https://www.diodes.com/assets/Datasheets/DMG2305UX.pdf" (at 0 0 0) (effects (font (size 1.27 1.27)) hide))')
    out.append('      (symbol "Transistor_FET:DMG2305UX_0_1"')
    out.append('        (rectangle (start -5.08 3.81) (end 5.08 -3.81)')
    out.append('          (stroke (width 0.254) (type default)) (fill (type none))))')
    out.append('      (symbol "Transistor_FET:DMG2305UX_1_1"')
    for num, name, ptype, px, py, rot in pins:
        out.append(
            f'        (pin {ptype} line (at {px} {py:.3f} {rot}) (length 2.54)\n'
            f'          (name "{name}" (effects (font (size 1.27 1.27))))\n'
            f'          (number "{num}" (effects (font (size 1.27 1.27)))))'
        )
    out.append('        )')
    out.append('      )')
    return "\n".join(out)


def _inductor_lib_symbol() -> str:
    """Simple 2-pin inductor symbol (Device:L)."""
    return r"""    (symbol "Device:L" (pin_numbers hide) (pin_names (offset 1.016)) (in_bom yes) (on_board yes)
      (property "Reference" "L" (at -2.032 0 90) (effects (font (size 1.27 1.27))))
      (property "Value" "L" (at 1.778 0 90) (effects (font (size 1.27 1.27))))
      (property "Footprint" "" (at 0 0 0) (effects (font (size 1.27 1.27)) hide))
      (property "Datasheet" "~" (at 0 0 0) (effects (font (size 1.27 1.27)) hide))
      (symbol "Device:L_0_1"
        (arc (start 0 -2.54) (mid 0.6323 -1.905) (end 0 -1.27) (stroke (width 0) (type default)) (fill (type none)))
        (arc (start 0 -1.27) (mid 0.6323 -0.635) (end 0 0) (stroke (width 0) (type default)) (fill (type none)))
        (arc (start 0 0) (mid 0.6323 0.635) (end 0 1.27) (stroke (width 0) (type default)) (fill (type none)))
        (arc (start 0 1.27) (mid 0.6323 1.905) (end 0 2.54) (stroke (width 0) (type default)) (fill (type none))))
      (symbol "Device:L_1_1"
        (pin passive line (at 0 3.81 270) (length 1.27)
          (name "~" (effects (font (size 1.27 1.27))))
          (number "1" (effects (font (size 1.27 1.27)))))
        (pin passive line (at 0 -3.81 90) (length 1.27)
          (name "~" (effects (font (size 1.27 1.27))))
          (number "2" (effects (font (size 1.27 1.27)))))))
""".strip()


def _schottky_diode_lib_symbol() -> str:
    """Simple Schottky diode symbol (Device:D_Schottky). Pin 1 = K (Kathode), Pin 2 = A (Anode)."""
    return r"""    (symbol "Device:D_Schottky" (pin_numbers hide) (pin_names (offset 1.016) hide) (in_bom yes) (on_board yes)
      (property "Reference" "D" (at 0 2.54 0) (effects (font (size 1.27 1.27))))
      (property "Value" "D_Schottky" (at 0 -2.54 0) (effects (font (size 1.27 1.27))))
      (property "Footprint" "" (at 0 0 0) (effects (font (size 1.27 1.27)) hide))
      (property "Datasheet" "~" (at 0 0 0) (effects (font (size 1.27 1.27)) hide))
      (symbol "Device:D_Schottky_0_1"
        (polyline (pts (xy -1.016 1.27) (xy -1.016 -1.27)) (stroke (width 0.2032) (type default)) (fill (type none)))
        (polyline (pts (xy 1.016 1.27) (xy 1.016 0.508) (xy 1.524 0.508)) (stroke (width 0.2032) (type default)) (fill (type none)))
        (polyline (pts (xy 1.016 -1.27) (xy 1.016 -0.508) (xy 0.508 -0.508)) (stroke (width 0.2032) (type default)) (fill (type none)))
        (polyline (pts (xy 1.016 1.27) (xy -1.016 0) (xy 1.016 -1.27) (xy 1.016 1.27)) (stroke (width 0.254) (type default)) (fill (type none))))
      (symbol "Device:D_Schottky_1_1"
        (pin passive line (at -3.81 0 0) (length 2.794)
          (name "K" (effects (font (size 1.27 1.27))))
          (number "1" (effects (font (size 1.27 1.27)))))
        (pin passive line (at 3.81 0 180) (length 2.794)
          (name "A" (effects (font (size 1.27 1.27))))
          (number "2" (effects (font (size 1.27 1.27)))))))
""".strip()


def _rotary_encoder_switch_lib_symbol() -> str:
    """EC11 Rotary Encoder mit integriertem Push-Switch (5-Pin).

    Pin-Layout:
        Pin 1 (A)   links oben    local (-5.08, +5.08)
        Pin 2 (B)   links mitte   local (-5.08, 0)
        Pin 3 (C)   links unten   local (-5.08, -5.08) — Common, to GND
        Pin 4 (SW1) rechts oben   local (+5.08, +2.54)
        Pin 5 (SW2) rechts unten  local (+5.08, -2.54) — to GND
    """
    return r"""
    (symbol "Encoder:Rotary_Encoder_Switch" (pin_names (offset 0.508)) (in_bom yes) (on_board yes)
      (property "Reference" "EN" (at 0 9.144 0) (effects (font (size 1.27 1.27))))
      (property "Value" "Rotary_Encoder_Switch" (at 0 -9.144 0) (effects (font (size 1.27 1.27))))
      (property "Footprint" "" (at 0 0 0) (effects (font (size 1.27 1.27)) hide))
      (property "Datasheet" "https://jlcpcb.com/partdetail/C209762" (at 0 0 0) (effects (font (size 1.27 1.27)) hide))
      (symbol "Encoder:Rotary_Encoder_Switch_0_1"
        (rectangle (start -2.54 7.62) (end 2.54 -7.62)
          (stroke (width 0.254) (type default)) (fill (type none))))
      (symbol "Encoder:Rotary_Encoder_Switch_1_1"
        (pin passive line (at -5.08 5.08 0) (length 2.54)
          (name "A" (effects (font (size 1.27 1.27))))
          (number "A" (effects (font (size 1.27 1.27)))))
        (pin passive line (at -5.08 0 0) (length 2.54)
          (name "B" (effects (font (size 1.27 1.27))))
          (number "B" (effects (font (size 1.27 1.27)))))
        (pin passive line (at -5.08 -5.08 0) (length 2.54)
          (name "C" (effects (font (size 1.27 1.27))))
          (number "C" (effects (font (size 1.27 1.27)))))
        (pin passive line (at 5.08 2.54 180) (length 2.54)
          (name "SW1" (effects (font (size 1.27 1.27))))
          (number "S1" (effects (font (size 1.27 1.27)))))
        (pin passive line (at 5.08 -2.54 180) (length 2.54)
          (name "SW2" (effects (font (size 1.27 1.27))))
          (number "S2" (effects (font (size 1.27 1.27)))))))
""".strip()


def _pcm5102a_lib_symbol() -> str:
    """PCM5102A I²S DAC (TSSOP-20). Offizielles TI-Datasheet-Pinout SLAS859C.

    Pins links (top→bottom): 1-10
        1: CPVDD   (charge pump power supply)
        2: CAPP    (charge pump fly cap +)
        3: CPGND   (charge pump ground)
        4: CAPM    (charge pump fly cap -)
        5: VNEG    (negative voltage, 1µF to GND)
        6: OUTL    (left audio output)
        7: OUTR    (right audio output)
        8: AVDD    (analog power)
        9: AGND    (analog ground)
        10: DEMP   (de-emphasis, GND=off)

    Pins rechts (top→bottom, pin 20 oben):
        20: DVDD   (digital power)
        19: DGND   (digital ground)
        18: LDOO   (1.8V LDO output, leave open or 0.1µF)
        17: XSMT   (soft mute, pull-up to DVDD)
        16: FMT    (format, GND=I²S)
        15: LRCK   (left/right clock)
        14: DIN    (audio data input)
        13: BCK    (bit clock)
        12: SCK    (system clock, GND=3-wire mode)
        11: FLT    (filter select, GND=normal)
    """
    pins_left = [
        (1, "CPVDD", "power_in"),
        (2, "CAPP", "output"),
        (3, "CPGND", "power_in"),
        (4, "CAPM", "output"),
        (5, "VNEG", "output"),
        (6, "OUTL", "output"),
        (7, "OUTR", "output"),
        (8, "AVDD", "power_in"),
        (9, "AGND", "power_in"),
        (10, "DEMP", "input"),
    ]
    pins_right = [
        (20, "DVDD", "power_in"),
        (19, "DGND", "power_in"),
        (18, "LDOO", "output"),
        (17, "XSMT", "input"),
        (16, "FMT", "input"),
        (15, "LRCK", "input"),
        (14, "DIN", "input"),
        (13, "BCK", "input"),
        (12, "SCK", "input"),
        (11, "FLT", "input"),
    ]
    y_top = 11.43  # (10-1)*2.54/2
    rect_top = y_top + 2.54
    rect_bot = -y_top - 2.54
    out = ['    (symbol "Audio:PCM5102A" (in_bom yes) (on_board yes)']
    out.append(f'      (property "Reference" "U" (at 0 {rect_top + 1.27} 0) (effects (font (size 1.27 1.27))))')
    out.append(f'      (property "Value" "PCM5102A" (at 0 {rect_bot - 1.27} 0) (effects (font (size 1.27 1.27))))')
    out.append('      (property "Footprint" "" (at 0 0 0) (effects (font (size 1.27 1.27)) hide))')
    out.append('      (property "Datasheet" "https://www.ti.com/lit/ds/symlink/pcm5102a.pdf" (at 0 0 0) (effects (font (size 1.27 1.27)) hide))')
    out.append('      (symbol "Audio:PCM5102A_0_1"')
    out.append(f'        (rectangle (start -10.16 {rect_top}) (end 10.16 {rect_bot})')
    out.append('          (stroke (width 0.254) (type default)) (fill (type none))))')
    out.append('      (symbol "Audio:PCM5102A_1_1"')
    for idx, (num, name, ptype) in enumerate(pins_left):
        ly = y_top - idx * 2.54
        out.append(
            f'        (pin {ptype} line (at -12.7 {ly:.3f} 0) (length 2.54)\n'
            f'          (name "{name}" (effects (font (size 1.27 1.27))))\n'
            f'          (number "{num}" (effects (font (size 1.27 1.27)))))'
        )
    for idx, (num, name, ptype) in enumerate(pins_right):
        ly = y_top - idx * 2.54
        out.append(
            f'        (pin {ptype} line (at 12.7 {ly:.3f} 180) (length 2.54)\n'
            f'          (name "{name}" (effects (font (size 1.27 1.27))))\n'
            f'          (number "{num}" (effects (font (size 1.27 1.27)))))'
        )
    out.append('        )')
    out.append('      )')
    return "\n".join(out)


def _pam8406_lib_symbol() -> str:
    """PAM8406 Class-D/AB Stereo Amp (SOP-16) — r19.37 (ADR-0025).

    Replaces the NRND PAM8403H. Pinout VERIFIED against the Diodes Inc
    PAM8406 datasheet, document DSxxxxx Rev. 1-0, March 2013, "Pin
    Descriptions" (p.2). LCSC C86270 = PAM8406DR (lifecycle: Active).

    Near-identical to the PAM8403H footprint (same 16-SOIC) — the ONE
    functional pin difference is pin 9: PAM8403 = NC, PAM8406 = MODE
    (High: Class-D / Low: Class-AB). We tie MODE HIGH (+5V) for Class-D.
    The output-polarity pin labels also differ from the 8403 (pin 1 is
    +OUT_L on the 8406, not -OUT_L) — corrected here per the datasheet.

    Pin-Belegung per Datasheet Page 2 "Pin Descriptions":
        1:  +OUT_L  (Left Channel Positive Output, BTL)
        2:  PGNDL   (Power Ground, left)
        3:  -OUT_L  (Left Channel Negative Output, BTL)
        4:  PVDDL   (Power VDD, left)
        5:  MUTE    (Mute Control Input, ACTIVE LOW)
        6:  VDD     (Analog VDD)
        7:  INL     (Left Channel Input)
        8:  VREF    (Internal analog reference — bypass cap to GND REQUIRED)
        9:  MODE    (High: Class-D, Low: Class-AB — tied +5V here = Class-D)
        10: INR     (Right Channel Input)
        11: GND     (Analog GND)
        12: SHDN    (Shutdown Control Input, ACTIVE LOW)
        13: PVDDR   (Power VDD, right)
        14: -OUT_R  (Right Channel Negative Output, BTL)
        15: PGNDR   (Power Ground, right)
        16: +OUT_R  (Right Channel Positive Output, BTL)
    """
    pins_left = [
        (1, "OUTL+", "output"),
        (2, "PGND", "power_in"),
        (3, "OUTL-", "output"),
        (4, "PVDD", "power_in"),
        (5, "/MUTE", "input"),
        (6, "VDD", "power_in"),
        (7, "INL", "input"),
        (8, "VREF", "output"),
    ]
    pins_right = [
        (16, "OUTR+", "output"),
        (15, "PGND", "power_in"),
        (14, "OUTR-", "output"),
        (13, "PVDD", "power_in"),
        (12, "/SHDN", "input"),
        (11, "GND", "power_in"),
        (10, "INR", "input"),
        (9, "MODE", "input"),
    ]
    y_top = 8.89
    rect_top = y_top + 2.54
    rect_bot = -y_top - 2.54
    out = ['    (symbol "Audio:PAM8406" (in_bom yes) (on_board yes)']
    out.append(f'      (property "Reference" "U" (at 0 {rect_top + 1.27} 0) (effects (font (size 1.27 1.27))))')
    out.append(f'      (property "Value" "PAM8406" (at 0 {rect_bot - 1.27} 0) (effects (font (size 1.27 1.27))))')
    out.append('      (property "Footprint" "" (at 0 0 0) (effects (font (size 1.27 1.27)) hide))')
    out.append('      (property "Datasheet" "PAM8406 (Diodes Inc Rev 1-0, Mar 2013)" (at 0 0 0) (effects (font (size 1.27 1.27)) hide))')
    out.append('      (symbol "Audio:PAM8406_0_1"')
    out.append(f'        (rectangle (start -10.16 {rect_top}) (end 10.16 {rect_bot})')
    out.append('          (stroke (width 0.254) (type default)) (fill (type none))))')
    out.append('      (symbol "Audio:PAM8406_1_1"')
    for idx, (num, name, ptype) in enumerate(pins_left):
        ly = y_top - idx * 2.54
        out.append(
            f'        (pin {ptype} line (at -12.7 {ly:.3f} 0) (length 2.54)\n'
            f'          (name "{name}" (effects (font (size 1.27 1.27))))\n'
            f'          (number "{num}" (effects (font (size 1.27 1.27)))))'
        )
    for idx, (num, name, ptype) in enumerate(pins_right):
        ly = y_top - idx * 2.54
        out.append(
            f'        (pin {ptype} line (at 12.7 {ly:.3f} 180) (length 2.54)\n'
            f'          (name "{name}" (effects (font (size 1.27 1.27))))\n'
            f'          (number "{num}" (effects (font (size 1.27 1.27)))))'
        )
    out.append('        )')
    out.append('      )')
    return "\n".join(out)


def _ferrite_bead_lib_symbol() -> str:
    """Ferrite bead 2-pin symbol (BLM18AG601 600Ω@100MHz)."""
    return r"""
    (symbol "Device:Ferrite_Bead" (pin_numbers hide) (pin_names (offset 0.254) hide) (in_bom yes) (on_board yes)
      (property "Reference" "FB" (at 0 2.794 0) (effects (font (size 1.27 1.27))))
      (property "Value" "Ferrite_Bead" (at 0 -2.794 0) (effects (font (size 1.27 1.27))))
      (property "Footprint" "" (at 0 0 0) (effects (font (size 1.27 1.27)) hide))
      (property "Datasheet" "~" (at 0 0 0) (effects (font (size 1.27 1.27)) hide))
      (symbol "Device:Ferrite_Bead_0_1"
        (rectangle (start -2.54 -0.762) (end 2.54 0.762)
          (stroke (width 0.254) (type default)) (fill (type none)))
        (polyline (pts (xy -2.032 0.762) (xy 2.032 -0.762))
          (stroke (width 0.254) (type default)) (fill (type none))))
      (symbol "Device:Ferrite_Bead_1_1"
        (pin passive line (at -3.81 0 0) (length 1.27)
          (name "~" (effects (font (size 1.27 1.27))))
          (number "1" (effects (font (size 1.27 1.27)))))
        (pin passive line (at 3.81 0 180) (length 1.27)
          (name "~" (effects (font (size 1.27 1.27))))
          (number "2" (effects (font (size 1.27 1.27)))))))
""".strip()


def _conn_02xN_lib_symbol(n: int) -> str:
    """Generic 2×N-row dual-column header symbol (Pi GPIO style).

    Pin local positions: left column (odd numbers) at x=-5.08, right column
    (even numbers) at x=+5.08. Row R (1..n) at local y = +(n-1)*1.27 - (R-1)*2.54
    in KiCad Y-UP lib coords. Pin 1 is top-left.
    """
    y_top = (n - 1) * 1.27
    rect_top = y_top + 2.54
    rect_bot = -y_top - 2.54
    out = [f'    (symbol "Connector:Conn_02x{n:02d}" (pin_names (offset 1.016) hide) (in_bom yes) (on_board yes)']
    out.append(f'      (property "Reference" "J" (at 0 {rect_top + 1.27} 0) (effects (font (size 1.27 1.27))))')
    out.append(f'      (property "Value" "Conn_02x{n:02d}" (at 0 {rect_bot - 1.27} 0) (effects (font (size 1.27 1.27))))')
    out.append('      (property "Footprint" "" (at 0 0 0) (effects (font (size 1.27 1.27)) hide))')
    out.append('      (property "Datasheet" "~" (at 0 0 0) (effects (font (size 1.27 1.27)) hide))')
    out.append(f'      (symbol "Connector:Conn_02x{n:02d}_0_1"')
    out.append(f'        (rectangle (start -2.54 {rect_top}) (end 2.54 {rect_bot})')
    out.append('          (stroke (width 0.254) (type default)) (fill (type none))))')
    out.append(f'      (symbol "Connector:Conn_02x{n:02d}_1_1"')
    for row in range(n):
        ly = y_top - row * 2.54
        # Left pin = odd number 2*row+1, right pin = even number 2*row+2
        pl_num = 2 * row + 1
        pr_num = 2 * row + 2
        out.append(
            f'        (pin passive line (at -5.08 {ly:.3f} 0) (length 2.54)\n'
            f'          (name "Pin_{pl_num}" (effects (font (size 1.27 1.27))))\n'
            f'          (number "{pl_num}" (effects (font (size 1.27 1.27)))))'
        )
        out.append(
            f'        (pin passive line (at 5.08 {ly:.3f} 180) (length 2.54)\n'
            f'          (name "Pin_{pr_num}" (effects (font (size 1.27 1.27))))\n'
            f'          (number "{pr_num}" (effects (font (size 1.27 1.27)))))'
        )
    out.append('        )')
    out.append('      )')
    return "\n".join(out)


def _audiojack_lib_symbol() -> str:
    """3.5mm TRS stereo jack with insertion-detect switch (PJ-320D, SHOU HAN).

    r18.82 AUDIT-FIX (KRITISCH): Pin-NUMMERN gegen das PJ-320D-Datenblatt
    (LCSC-PDF 50aca6c1..., Zeichnung S. 1: P.C.B-LAYOUT mit Pads D/C/B/A +
    Schaltbild OA/OD/OC/OB) korrigiert. Der vendored Footprint mappt
    Pad 1=A, 2=D, 3=C, 4=B (Pad-Pitch 3,0/4,0 mm und Ø1,0-Locator @7,0 mm
    stimmen exakt mit der Zeichnung ueberein). Funktional laut Schaltbild:
    A=Sleeve (Koerperkontakt, ohne Feder), D=Ring, C=Tip-Switch (DETECT,
    ruht ohne Stecker am Tip-Kontakt), B=Tip. Die alte Nummerierung
    (T=1, R=2, S=3, DET=4) haette gelegt: Audio-L auf den SLEEVE (=Barrel!),
    GND auf den Detect-Kontakt, JACK_DETECT auf den TIP → Line-Out/MIDI-Out
    beide falsch verdrahtet. Neu: T=4(B), R=2(D), S=1(A), DET=3(C).

    Pins (Name → Pad):
      T   (Pad 4 = B) Tip    = Left audio out
      R   (Pad 2 = D) Ring   = Right audio out
      S   (Pad 1 = A) Sleeve = GND
      DET (Pad 3 = C) detect switch contact — ruht ohne Stecker am TIP-
              Kontakt (nicht an S!): mit S(GND)-beschaltetem Netz + MCP-
              Pull-up: idle = ueber R_LO_L/DAC-Ausgang schwach definiert →
              Firmware-Auswertung siehe audio_sheet-Kommentar; Polaritaet
              beim Bring-up pruefen (Datenblatt-Schaltbild: C-B normally
              closed, oeffnet beim Einstecken).
    """
    return r"""
    (symbol "Connector:AudioJack3_Switch" (in_bom yes) (on_board yes)
      (property "Reference" "J" (at 0 7.62 0) (effects (font (size 1.27 1.27))))
      (property "Value" "AudioJack3_Switch" (at 0 5.08 0) (effects (font (size 1.27 1.27))))
      (property "Footprint" "" (at 0 0 0) (effects (font (size 1.27 1.27)) hide))
      (property "Datasheet" "~" (at 0 0 0) (effects (font (size 1.27 1.27)) hide))
      (symbol "Connector:AudioJack3_Switch_0_1"
        (rectangle (start -5.08 3.81) (end 5.08 -5.08)
          (stroke (width 0.254) (type default)) (fill (type none))))
      (symbol "Connector:AudioJack3_Switch_1_1"
        (pin passive line (at 7.62 2.54 180) (length 2.54)
          (name "T" (effects (font (size 1.27 1.27))))
          (number "4" (effects (font (size 1.27 1.27)))))
        (pin passive line (at 7.62 0 180) (length 2.54)
          (name "R" (effects (font (size 1.27 1.27))))
          (number "2" (effects (font (size 1.27 1.27)))))
        (pin passive line (at 7.62 -2.54 180) (length 2.54)
          (name "S" (effects (font (size 1.27 1.27))))
          (number "1" (effects (font (size 1.27 1.27)))))
        (pin passive line (at -7.62 0 0) (length 2.54)
          (name "DET" (effects (font (size 1.27 1.27))))
          (number "3" (effects (font (size 1.27 1.27)))))))
""".strip()


def _mounting_hole_lib_symbol() -> str:
    """Plattiertes Mounting-Hole mit GND-Pad (r18.84 — mech. Spec §6:
    4x M2.5, Bohrung 2,7 mm, Pad O 6 mm, plattiert; Positionen MH1-MH4 =
    (12,6)/(240,6)/(12,96)/(240,96) auf der 252x102-Outline)."""
    out = []
    out.append('    (symbol "Mechanical:MountingHole_Pad" (pin_names (offset 0) hide) (in_bom no) (on_board yes)')
    out.append('      (property "Reference" "H" (at 0 5.08 0) (effects (font (size 1.27 1.27))))')
    out.append('      (property "Value" "MountingHole_Pad" (at 0 -3.81 0) (effects (font (size 1.27 1.27)) hide))')
    out.append('      (symbol "Mechanical:MountingHole_Pad_0_1"')
    out.append('        (circle (center 0 1.27) (radius 1.27) (stroke (width 0.508) (type default)) (fill (type none)))')
    out.append('      )')
    out.append('      (symbol "Mechanical:MountingHole_Pad_1_1"')
    out.append('        (pin passive line (at 0 -2.54 90) (length 2.54)')
    out.append('          (name "1" (effects (font (size 1.27 1.27))))')
    out.append('          (number "1" (effects (font (size 1.27 1.27)))))')
    out.append('      )')
    out.append('    )')
    return "\n".join(out)


def _testpoint_lib_symbol() -> str:
    """Testpunkt (r18.84 — AI_READY_SCHEMATIC_STANDARD: TP_* Test-/Debug-
    Zugang fuer Schluessel-Netze; SMD-Pad D1.5mm, nichts zu bestuecken)."""
    out = []
    out.append('    (symbol "Connector:TestPoint" (pin_names (offset 0) hide) (in_bom no) (on_board yes)')
    out.append('      (property "Reference" "TP" (at 0 5.08 0) (effects (font (size 1.27 1.27))))')
    out.append('      (property "Value" "TestPoint" (at 0 -3.81 0) (effects (font (size 1.27 1.27)) hide))')
    out.append('      (symbol "Connector:TestPoint_0_1"')
    out.append('        (circle (center 0 1.27) (radius 0.762) (stroke (width 0.254) (type default)) (fill (type none)))')
    out.append('      )')
    out.append('      (symbol "Connector:TestPoint_1_1"')
    out.append('        (pin passive line (at 0 -2.54 90) (length 2.54)')
    out.append('          (name "1" (effects (font (size 1.27 1.27))))')
    out.append('          (number "1" (effects (font (size 1.27 1.27)))))')
    out.append('      )')
    out.append('    )')
    return "\n".join(out)


def _tps22918_lib_symbol() -> str:
    """TPS22918DBVR High-Side-Load-Switch, SOT-23-6 (TI) — r18.81 / ADR-0016.

    OFFIZIELLES PINOUT (TI-Datenblatt SLVSD76C, Section 5 "Pin Configuration
    and Functions", DBV Top View — Seite als PNG gerendert und gelesen):

        Pin 1 = VIN  (input; "Place ceramic bypass capacitor(s)... and GND")
        Pin 2 = GND
        Pin 3 = ON   (active high, "Do not leave floating")
        Pin 4 = CT   (slew-rate control, "Can be left floating" → no_connect;
                      optionaler CT-Cap = Soft-Start, bei Bedarf nachruesten)
        Pin 5 = QOD  (Quick Output Discharge — DS-Option 2: "Tying QOD
                      directly to VOUT and using the internal resistor")
        Pin 6 = VOUT

    HINWEIS: ADR-0016 nannte Pin 4 "NC" und Pin 5 "no-connect (interne
    Quick-Discharge)" — beides leicht daneben: Pin 4 heisst CT (floaten
    erlaubt = schnellster Anstieg), und QOD FLOATEN würde die Quick-Discharge
    DEAKTIVIEREN. Fuer die ADR-Intention (definiertes Aus, LCD/3V3-Domäne
    entlädt aktiv) wird QOD extern an VOUT gebunden.
    """
    out = []
    out.append('    (symbol "Power_Switch:TPS22918" (pin_names (offset 0.508)) (in_bom yes) (on_board yes)')
    out.append('      (property "Reference" "U" (at 0 6.35 0) (effects (font (size 1.27 1.27))))')
    out.append('      (property "Value" "TPS22918" (at 0 -8.89 0) (effects (font (size 1.27 1.27)) hide))')
    out.append('      (symbol "Power_Switch:TPS22918_0_1"')
    out.append('        (rectangle (start -6.35 5.08) (end 6.35 -6.35) (stroke (width 0.254) (type default)) (fill (type background)))')
    out.append('      )')
    out.append('      (symbol "Power_Switch:TPS22918_1_1"')
    out.append('        (pin power_in line (at -8.89 2.54 0) (length 2.54)')
    out.append('          (name "VIN" (effects (font (size 1.27 1.27))))')
    out.append('          (number "1" (effects (font (size 1.27 1.27)))))')
    out.append('        (pin input line (at -8.89 -2.54 0) (length 2.54)')
    out.append('          (name "ON" (effects (font (size 1.27 1.27))))')
    out.append('          (number "3" (effects (font (size 1.27 1.27)))))')
    out.append('        (pin power_out line (at 8.89 2.54 180) (length 2.54)')
    out.append('          (name "VOUT" (effects (font (size 1.27 1.27))))')
    out.append('          (number "6" (effects (font (size 1.27 1.27)))))')
    out.append('        (pin no_connect line (at 8.89 0 180) (length 2.54)')
    out.append('          (name "CT" (effects (font (size 1.27 1.27))))')
    out.append('          (number "4" (effects (font (size 1.27 1.27)))))')
    out.append('        (pin passive line (at 8.89 -2.54 180) (length 2.54)')
    out.append('          (name "QOD" (effects (font (size 1.27 1.27))))')
    out.append('          (number "5" (effects (font (size 1.27 1.27)))))')
    out.append('        (pin power_in line (at 0 -8.89 90) (length 2.54)')
    out.append('          (name "GND" (effects (font (size 1.27 1.27))))')
    out.append('          (number "2" (effects (font (size 1.27 1.27)))))')
    out.append('      )')
    out.append('    )')
    return "\n".join(out)


def _sw_spdt_lib_symbol() -> str:
    """SPDT slide switch (SW_PWR ALPS SSSS811101) — r18.85 / ADR-0016.

    Pin numbers = footprint pads of field_ambience:SW_ALPS-SSSS811101_SlideSwitch_SMD
    (3 signal pads, asymmetric 3.0/1.5 mm spacing): pin 2 = COMMON. Unlike the
    previous MST-12D18G3 (terminals unlabeled in its datasheet), the ALPS
    datasheet's circuit diagram DOES label the common: C = terminal (2) — the
    moving contact bridges C to (1) or (3). Verified from the official ALPS
    SSSS811101 catalog page (wmsc.lcsc.com .../1808041445_ALPSALPINE-
    SSSS811101_C109335.pdf, p.3 "Circuit Diagram"). A quick continuity check on
    the physical part before fab is still cheap insurance.
    Footprint pads 4-7 = ground-frame terminals (not in this 3-pin symbol; they
    solder-anchor the metal frame — optionally tie to GND in layout for EMC).
    """
    out = []
    out.append('    (symbol "Switch:SW_SPDT" (pin_names (offset 0) hide) (in_bom yes) (on_board yes)')
    out.append('      (property "Reference" "SW" (at 0 4.318 0) (effects (font (size 1.27 1.27))))')
    out.append('      (property "Value" "SW_SPDT" (at 0 -5.08 0) (effects (font (size 1.27 1.27)) hide))')
    out.append('      (symbol "Switch:SW_SPDT_0_1"')
    out.append('        (circle (center -2.032 0) (radius 0.508) (stroke (width 0) (type default)) (fill (type none)))')
    out.append('        (polyline (pts (xy -1.524 0.254) (xy 1.524 2.286)) (stroke (width 0) (type default)) (fill (type none)))')
    out.append('        (circle (center 2.032 2.54) (radius 0.508) (stroke (width 0) (type default)) (fill (type none)))')
    out.append('        (circle (center 2.032 -2.54) (radius 0.508) (stroke (width 0) (type default)) (fill (type none)))')
    out.append('      )')
    out.append('      (symbol "Switch:SW_SPDT_1_1"')
    out.append('        (pin passive line (at 5.08 2.54 180) (length 2.54)')
    out.append('          (name "A" (effects (font (size 1.27 1.27))))')
    out.append('          (number "1" (effects (font (size 1.27 1.27)))))')
    out.append('        (pin passive line (at -5.08 0 0) (length 2.54)')
    out.append('          (name "COM" (effects (font (size 1.27 1.27))))')
    out.append('          (number "2" (effects (font (size 1.27 1.27)))))')
    out.append('        (pin passive line (at 5.08 -2.54 180) (length 2.54)')
    out.append('          (name "B" (effects (font (size 1.27 1.27))))')
    out.append('          (number "3" (effects (font (size 1.27 1.27)))))')
    out.append('      )')
    out.append('    )')
    return "\n".join(out)



def _psram_lib_symbol() -> str:
    """APS6404L-3SQN-SN — 8 MB QSPI PSRAM, SOP-8 (LCSC C3028887, ADR-0022).
    Pinout VERIFIED against the AP Memory datasheet Rev. 2.1 (Oct 2019),
    §3.1 "Package Types SOP/USON, Top view":
        /CE 1 - 8 VDD ; SO/SIO[1] 2 - 7 SIO[3] ; SIO[2] 3 - 6 SCLK ;
        VSS 4 - 5 SI/SIO[0]
    Footprint dims: SOP-8L(150) = 3.9 mm body / 1.27 mm pitch = the generic
    Package_SO:SOIC-8_3.9x4.9mm_P1.27mm (standard SOIC pad numbering 1-8).
    Belt-and-suspenders before fab: pull the exact LCSC land pattern via
    `easyeda2kicad --full --lcsc_id=C3028887`.
    Pin 1: CE   (/CE — chip select, active-low)
    Pin 2: SIO1 (SO/SIO[1])
    Pin 3: SIO2 (SIO[2] / WP# in SPI mode)
    Pin 4: VSS  (ground)
    Pin 5: SIO0 (SI/SIO[0])
    Pin 6: SCLK (serial clock)
    Pin 7: SIO3 (SIO[3] / HOLD# in SPI mode)
    Pin 8: VDD  (2.7-3.6 V)
    """
    pins = [
        (1, "CE",   "input",         -7.62,  5.08),
        (6, "SCLK", "input",         -7.62,  2.54),
        (5, "SIO0", "bidirectional", -7.62,  0.0),
        (2, "SIO1", "bidirectional", -7.62, -2.54),
        (8, "VDD",  "power_in",       7.62,  5.08),
        (4, "VSS",  "power_in",       7.62,  2.54),
        (3, "SIO2", "bidirectional",  7.62,  0.0),
        (7, "SIO3", "bidirectional",  7.62, -2.54),
    ]
    out = ['    (symbol "Memory_RAM:APS6404L" (in_bom yes) (on_board yes)']
    out.append('      (property "Reference" "U" (at 0 8.89 0) (effects (font (size 1.27 1.27))))')
    out.append('      (property "Value" "APS6404L-3SQN-SN" (at 0 -8.89 0) (effects (font (size 1.27 1.27))))')
    out.append('      (property "Footprint" "" (at 0 0 0) (effects (font (size 1.27 1.27)) hide))')
    out.append('      (property "Datasheet" "https://www.lcsc.com/product-detail/C3028887.html" (at 0 0 0) (effects (font (size 1.27 1.27)) hide))')
    out.append('      (symbol "Memory_RAM:APS6404L_0_1"')
    out.append('        (rectangle (start -5.08 7.62) (end 5.08 -7.62)')
    out.append('          (stroke (width 0.254) (type default)) (fill (type none))))')
    out.append('      (symbol "Memory_RAM:APS6404L_1_1"')
    for num, name, ptype, px, py in pins:
        rot = 0 if px < 0 else 180
        out.append(
            f'        (pin {ptype} line (at {px} {py:.3f} {rot}) (length 2.54)\n'
            f'          (name "{name}" (effects (font (size 1.27 1.27))))\n'
            f'          (number "{num}" (effects (font (size 1.27 1.27)))))'
        )
    out.append('        )')
    out.append('      )')
    return "\n".join(out)


LIB_SYMBOLS = (
    LIB_SYMBOLS
    + "\n" + _psram_lib_symbol()          # r19.10 (ADR-0022): QSPI PSRAM
    + "\n" + _pico2_lib_symbol()
    + "\n" + _conn_01xN_lib_symbol(16)
    + "\n" + _mcp23017_lib_symbol()
    + "\n" + _pca9685pw_lib_symbol()
    + "\n" + _bq24074_lib_symbol()       # r19.18 (ADR-0023): Power-Path-Charger
    + "\n" + _tpa6132a2_lib_symbol()     # r19.19 (ADR-0024): Kopfhoererverstaerker
    + "\n" + _tps61089_lib_symbol()
    + "\n" + _dmg2305ux_lib_symbol()
    + "\n" + _inductor_lib_symbol()
    + "\n" + _schottky_diode_lib_symbol()
    + "\n" + _rotary_encoder_switch_lib_symbol()
    + "\n" + _pcm5102a_lib_symbol()
    + "\n" + _pam8406_lib_symbol()
    + "\n" + _ferrite_bead_lib_symbol()
    + "\n" + _conn_01xN_lib_symbol(2)
    + "\n" + _conn_02xN_lib_symbol(20)
    + "\n" + _audiojack_lib_symbol()
    # r18 (H7-Migration):
    + "\n" + _stm32h743_lib_symbol()
    + "\n" + _crystal_lib_symbol()
    + "\n" + _ap7361c_lib_symbol()
    + "\n" + _nmos_sot23_lib_symbol()
    + "\n" + _conn_01xN_lib_symbol(8)
    # r18.81 (ADR-0016 Power-Off-Block):
    + "\n" + _tps22918_lib_symbol()
    + "\n" + _sw_spdt_lib_symbol()
    # r18.84 (Mounting-Holes + Testpunkte):
    + "\n" + _mounting_hole_lib_symbol()
    + "\n" + _testpoint_lib_symbol()
)


def fmt_property(name: str, value: str, x: float, y: float, hide: bool = False) -> str:
    h = " hide" if hide else ""
    return (
        f'      (property "{name}" "{value}" (at {x} {y} 0)\n'
        f"        (effects (font (size 1.27 1.27)){h}))"
    )


def place_symbol(
    *,
    lib_id: str,
    ref: str,
    value: str,
    x: float,
    y: float,
    footprint: str = "",
    datasheet: str = "~",
    rotation: int = 0,
    seed_suffix: str = "",
    extra_props: dict[str, str] | None = None,
    sheet_uuid_seed: str = "sheet_power_tree",
) -> str:
    """Render a placed instance of a symbol on the sheet."""
    sym_uuid = det_uuid(f"sym/{ref}/{seed_suffix}")
    props = [
        fmt_property("Reference", ref, x + 2.54, y - 2.54),
        fmt_property("Value", value, x + 2.54, y + 1.27),
        fmt_property("Footprint", footprint, x, y, hide=True),
        fmt_property("Datasheet", datasheet, x, y, hide=True),
    ]
    if extra_props:
        offset = 3.81
        for k, v in extra_props.items():
            props.append(fmt_property(k, v, x + 2.54, y + offset, hide=True))
            offset += 1.27
    return (
        f"  (symbol (lib_id \"{lib_id}\") (at {x} {y} {rotation}) (unit 1)\n"
        f"    (in_bom yes) (on_board yes) (dnp no)\n"
        f"    (uuid \"{sym_uuid}\")\n"
        + "\n".join(props)
        + f"\n    (instances\n      (project \"{PROJECT_NAME}\"\n"
        f"        (path \"/{det_uuid(sheet_uuid_seed)}\" (reference \"{ref}\") (unit 1)))))\n"
    )


def wire(x1: float, y1: float, x2: float, y2: float, seed_suffix: str = "") -> str:
    return (
        f'  (wire (pts (xy {x1} {y1}) (xy {x2} {y2}))\n'
        f"    (stroke (width 0) (type default))\n"
        f"    (uuid \"{det_uuid(f'wire/{x1},{y1}-{x2},{y2}/{seed_suffix}')}\"))\n"
    )


def junction(x: float, y: float) -> str:
    return (
        f"  (junction (at {x} {y}) (diameter 0) (color 0 0 0 0)\n"
        f"    (uuid \"{det_uuid(f'jct/{x},{y}')}\"))\n"
    )


def label(x: float, y: float, name: str, rotation: int = 0) -> str:
    return (
        f"  (label \"{name}\" (at {x} {y} {rotation}) (fields_autoplaced)\n"
        f"    (effects (font (size 1.27 1.27)) (justify left bottom))\n"
        f"    (uuid \"{det_uuid(f'lbl/{x},{y}/{name}')}\"))\n"
    )


def hier_label(x: float, y: float, name: str, shape: str = "passive", rotation: int = 0) -> str:
    return (
        f'  (hierarchical_label "{name}" (shape {shape}) (at {x} {y} {rotation})\n'
        f"    (effects (font (size 1.524 1.524)) (justify right))\n"
        f"    (uuid \"{det_uuid(f'hlbl/{x},{y}/{name}')}\"))\n"
    )


# ----------------------------------------------------------------------------
# KiCad-Achsen-Konvention Helper:
# lib_symbol-Pins nutzen Y-UP (math), Schematic-Placement nutzt Y-DOWN (screen).
# Beim Platzieren: abs_pin_y = sym_y - local_pin_y (bei rotation=0).
# Beim Rotation: erst Local-Pin rotieren, dann (Y-Komponente negieren, dann sym addieren).
# Wir kapseln die Konversion in pin_abs() um Bug-Quellen zu eliminieren.
# ----------------------------------------------------------------------------


def pin_abs(sym_x: float, sym_y: float, local_x: float, local_y: float, rotation: int = 0) -> tuple[float, float]:
    """Berechne absolute Pin-Position für einen Pin mit local (lx, ly) am Symbol (sx, sy, rot)."""
    import math
    rad = math.radians(rotation)
    cos_r, sin_r = math.cos(rad), math.sin(rad)
    # KiCad symbol rotation is CCW in lib-coord (Y-up). Rotated local:
    rx = local_x * cos_r - local_y * sin_r
    ry = local_x * sin_r + local_y * cos_r
    return (sym_x + rx, sym_y - ry)


# ----------------------------------------------------------------------------
# Sheet 1 — Power Tree
# Komponenten + Verdrahtung lt. SPEC v0.6 §1, §3:
#   USB-C(VBUS) -> F1 (polyfuse 3A/6A) -> VBUS_FUSED -> BQ24074-IN (battery_sheet)
#   (+5V-Rail wird NUR vom Boost gespeist: VSYS -> U8 -> D3 -> +5V_OUT, r19.18)
#   USB-C(D±)   -> D1 (USBLC6-2SC6 ESD)   -> USB hier-label to stm32 sheet
#   USB-C(CC1)  -> R2 (5.1k)              -> GND
#   USB-C(CC2)  -> R3 (5.1k)              -> GND
#   VBUS_FUSED  -> D2 (SMAJ5.0A TVS)      -> GND
# ----------------------------------------------------------------------------
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
