Sancte3D/AMBIENT/field-ambience-current/firmware-c-next/src/controls.c

/*
 * controls.c — modifier + cell hold-latch state machine (ADR-0008 r2).
 * See controls.h for the behavioural contract.
 *
 * Hardware-independent: calls the engine_* / brain_* API only, so the host
 * test (test/test_controls.c) exercises the full latch logic, and the STM32
 * button/encoder handlers (src/hal_h743/main_h743.c) just feed edges in.
 */

#include "controls.h"
#include "engine.h"
#include "brain.h"
#include "dsp.h"
#include "tuning.h"

#define SHIFT_SRC(c) ((uint8_t)((c) + 9))   /* shift-octave pad source */

static bool s_mod[MOD_COUNT];
/* r19.20: which cell keys are PHYSICALLY down right now (press/release
 * edges, independent of latch mode). This — not "any active voice" — is
 * what pauses the generator: a hold-latched voice is part of the ambient
 * texture and must NOT freeze autoplay (the old HOLD+GENERATE deadlock). */
static uint8_t s_cells_down;
static bool s_hold_base [CTRL_CELL_COUNT];
static bool s_hold_shift[CTRL_CELL_COUNT];
/* Latch velocity, remembered so a key/world change can re-pitch the held
 * voices at their original loudness (controls_refresh_held_pitches). */
static float s_amp_base [CTRL_CELL_COUNT];
static float s_amp_shift[CTRL_CELL_COUNT];

/* Momentary (non-hold) note tracking: which source is sounding for a cell
 * that was tapped without Hold latched. -1 = none. */
static int8_t s_moment_src[CTRL_CELL_COUNT];

void controls_init(void) {
    for (int i = 0; i < MOD_COUNT; ++i) s_mod[i] = false;
    s_cells_down = 0;
    engine_set_user_presence(false);
    for (int c = 0; c < CTRL_CELL_COUNT; ++c) {
        s_hold_base[c]  = false;
        s_hold_shift[c] = false;
        s_amp_base[c]   = 0.0f;
        s_amp_shift[c]  = 0.0f;
        s_moment_src[c] = -1;
    }
}

static void clear_all_holds(void) {
    for (int c = 0; c < CTRL_CELL_COUNT; ++c) {
        if (s_hold_base[c])  { engine_note_off((uint8_t)c);          s_hold_base[c]  = false; }
        if (s_hold_shift[c]) { engine_note_off(SHIFT_SRC(c));        s_hold_shift[c] = false; }
        if (s_moment_src[c] >= 0) { engine_note_off((uint8_t)s_moment_src[c]); s_moment_src[c] = -1; }
    }
}

void controls_modifier(mod_id_t mod, bool pressed) {
    if (mod >= MOD_COUNT) return;
    switch (mod) {
        case MOD_SHIFT:
            s_mod[MOD_SHIFT] = pressed;   /* r19.20: momentary, both edges */
            break;
        case MOD_HOLD:
            if (pressed) s_mod[mod] = !s_mod[mod];   /* latch toggle on press */
            break;
        case MOD_DRONE:
            if (pressed) { s_mod[MOD_DRONE] = !s_mod[MOD_DRONE]; engine_set_drone(s_mod[MOD_DRONE]); }
            break;
        case MOD_GENERATE:
            if (pressed) { s_mod[MOD_GENERATE] = !s_mod[MOD_GENERATE];
                           engine_set_generative(s_mod[MOD_GENERATE], -1); }  /* -1 = Markov auto */
            break;
        case MOD_CLEAR:
            if (!pressed) break;
            if (s_mod[MOD_SHIFT]) {
                /* r19.20 SHIFT+CLEAR — FLUSH: silence everything that is
                 * sounding, but leave the modes running. The drone module
                 * is not touched by engine_all_off (own envelope), so it
                 * keeps sounding; the generator re-blooms on its next bar. */
                clear_all_holds();
                engine_all_off();
            } else {
                /* r19.20 CLEAR — FULL STOP: before this it only wiped the
                 * hold latches; drone + generator played on and the panel
                 * had no true "silence now" gesture. Order matters: modes
                 * off first (no new notes), then the all-off (voices end
                 * via their natural releases — the soft fade is the
                 * envelope, no hard cut, no click). */
                clear_all_holds();
                s_mod[MOD_HOLD] = false;
                if (s_mod[MOD_DRONE])    { s_mod[MOD_DRONE]    = false; engine_set_drone(false); }
                if (s_mod[MOD_GENERATE]) { s_mod[MOD_GENERATE] = false; engine_set_generative(false, -1); }
                engine_all_off();
            }
            break;
        default: break;
    }
}

void controls_cell_press(uint8_t cell, float velocity_amp) {
    if (cell >= CTRL_CELL_COUNT) return;
    s_cells_down |= (uint8_t)(1u << cell);      /* r19.20: physical key down */
    engine_set_user_presence(true);
    int   root = brain_cell_root(cell);
    float hz   = tuning_hz((float)root);
    float hz_s = tuning_hz((float)(root + 12));

    if (s_mod[MOD_HOLD]) {
        /* Latching: toggle the branch the Shift state selects. The OTHER
         * branch is untouched (ADR-0008 r2 independent latches). */
        if (s_mod[MOD_SHIFT]) {
            s_hold_shift[cell] = !s_hold_shift[cell];
            s_amp_shift[cell]  = s_hold_shift[cell] ? velocity_amp : 0.0f;
            if (s_hold_shift[cell]) engine_note_on(SHIFT_SRC(cell), hz_s, velocity_amp);
            else                    engine_note_off(SHIFT_SRC(cell));
        } else {
            s_hold_base[cell] = !s_hold_base[cell];
            s_amp_base[cell]  = s_hold_base[cell] ? velocity_amp : 0.0f;
            if (s_hold_base[cell]) engine_note_on((uint8_t)cell, hz, velocity_amp);
            else                   engine_note_off((uint8_t)cell);
        }
    } else {
        /* Momentary: sounds until release. Shift selects which octave. */
        uint8_t src = s_mod[MOD_SHIFT] ? SHIFT_SRC(cell) : (uint8_t)cell;
        float   f   = s_mod[MOD_SHIFT] ? hz_s : hz;
        engine_note_on(src, f, velocity_amp);
        s_moment_src[cell] = (int8_t)src;
    }
}

void controls_cell_release(uint8_t cell) {
    if (cell >= CTRL_CELL_COUNT) return;
    s_cells_down &= (uint8_t)~(1u << cell);     /* r19.20: physical key up */
    engine_set_user_presence(s_cells_down != 0);
    /* Only momentary notes release on key-up; held latches persist. */
    if (s_moment_src[cell] < 0) return;
    uint8_t src = (uint8_t)s_moment_src[cell];
    s_moment_src[cell] = -1;
    /* r18.88 AUDIT-FIX: a momentary tap shares its pad source with the
     * latch branch of the same cell. If that branch is LATCHED (e.g. cell
     * was hold-latched earlier, Hold has since been toggled off, user taps
     * the cell again), releasing the tap used to note_off the source and
     * SILENTLY KILL the latched voice while its latch bit stayed true —
     * latch state and sound were out of sync until the next Clear. A
     * latched source must survive the tap release (the tap re-bloomed it,
     * which is musically fine). */
    bool latched = (src == cell           && s_hold_base[cell]) ||
                   (src == SHIFT_SRC(cell) && s_hold_shift[cell]);
    if (!latched) engine_note_off(src);
}

/* r18.88 AUDIT-FIX: a world/key/mode change used to leave latched voices
 * ringing at their OLD pitches — clashing with the new key's drone root and
 * generative bed until the user cleared. Re-pitch every latched voice from
 * the current brain state (re-bloom on the same source = a fresh attack,
 * which reads as the new world blooming in). Call after engine_set_world /
 * engine_set_key. Momentary notes are left alone (they end in a moment
 * anyway, and re-pitching under a held finger feels wrong). */
void controls_refresh_held_pitches(void) {
    for (uint8_t c = 0; c < CTRL_CELL_COUNT; ++c) {
        if (!s_hold_base[c] && !s_hold_shift[c]) continue;
        int root = brain_cell_root(c);
        if (s_hold_base[c])
            engine_note_on(c, tuning_hz((float)root), s_amp_base[c]);
        if (s_hold_shift[c])
            engine_note_on(SHIFT_SRC(c), tuning_hz((float)(root + 12)),
                           s_amp_shift[c]);
    }
}

bool controls_any_cell_down(void) { return s_cells_down != 0; }
bool controls_hold_base (uint8_t cell) { return cell < CTRL_CELL_COUNT && s_hold_base[cell]; }
bool controls_hold_shift(uint8_t cell) { return cell < CTRL_CELL_COUNT && s_hold_shift[cell]; }
bool controls_modifier_active(mod_id_t mod) { return mod < MOD_COUNT && s_mod[mod]; }
