Sancte3D/AMBIENT/field-ambience-current/firmware-c-next/include/controls.h

#ifndef FAM_CONTROLS_H
#define FAM_CONTROLS_H

/*
 * controls.c — modifier + cell hold-latch state machine.
 *
 * The Cell-LED Independent-Latches behaviour from ADR-0008 r2, implemented
 * as a hardware-independent C module so the host tests cover it and the
 * STM32 + Pico builds share one source of truth.
 *
 * State per cell:
 *   hold_base[c]   — cell c sustains its base-octave root
 *   hold_shift[c]  — cell c sustains its shifted (+12) root
 * Both bits are independent: both lit at once = octave-stack (the rich
 * ambient drone effect from ADR-0008 r2).
 *
 * Modifier states (r19.20 semantics):
 *   shift      — MOMENTARY: active only while physically held (was a hidden
 *                toggle until r19.20 — a held modifier reads far more
 *                naturally on a panel with no dedicated shift LED lock)
 *   hold       — toggle-on-press; without it cell taps are momentary
 *   drone      — toggle; engine_set_drone(); root drone follows brain key
 *   generate   — toggle; engine_set_generative(true,…)
 *   clear      — momentary FULL STOP: wipes all hold bits, silences all
 *                voices (engine_all_off — natural releases, no hard cut),
 *                and turns HOLD/DRONE/GENERATE off
 *   shift+clear— FLUSH: silence the voices only; HOLD/DRONE/GENERATE keep
 *                running (drone re-swells, the generator plays on)
 *
 * Tap semantics (Hold latched + cell c tapped):
 *   shift OFF → toggle hold_base[c]:  if turning ON  → engine_note_on(c, root)
 *                                     if turning OFF → engine_note_off(c)
 *   shift ON  → toggle hold_shift[c]: if turning ON  → engine_note_on(c+9, root+12)
 *                                     if turning OFF → engine_note_off(c+9)
 *
 * Source-ID scheme (matches render_performance.c):
 *   base cell c   → source c       (0..4)
 *   shift cell c  → source c + 9   (9..13)
 *
 * Without Hold latched, a cell tap is a momentary note: down-edge → note_on,
 * up-edge → note_off. The Hall-velocity model in cells.c determines amp.
 */

#include <stdint.h>
#include <stdbool.h>

#define CTRL_CELL_COUNT 5

typedef enum {
    MOD_SHIFT = 0,
    MOD_HOLD,
    MOD_DRONE,
    MOD_GENERATE,
    MOD_CLEAR,
    MOD_COUNT,
} mod_id_t;

/* Reset all modifier + hold-latch state. Call once at boot. */
void controls_init(void);

/* Modifier press edge (pressed=true) / release edge (pressed=false).
 * SHIFT is momentary (r19.20) — feed BOTH edges. HOLD/DRONE/GENERATE latch
 * on press (next press toggles off). CLEAR acts on press: full stop, or
 * voice-flush when SHIFT is held. */
void controls_modifier(mod_id_t mod, bool pressed);

/* Cell tap (momentary press edge with velocity amp 0..1, ADR-0013). Velocity
 * comes from cells.c. If Hold is latched the bit toggles; otherwise it's a
 * momentary note. */
void controls_cell_press(uint8_t cell, float velocity_amp);

/* Cell release (momentary up-edge). Only meaningful when Hold is NOT latched
 * — releases the momentary note. Held cells are unaffected. */
void controls_cell_release(uint8_t cell);

/* Observability — used by LED renderer + UI. */
bool controls_any_cell_down(void);   /* r19.20: any cell key physically held */
bool controls_hold_base (uint8_t cell);
bool controls_hold_shift(uint8_t cell);
bool controls_modifier_active(mod_id_t mod);

/* r18.88: re-pitch all latched voices from the current brain key/mode/vibe
 * at their remembered latch velocity. Call after a world/key change so held
 * notes follow the new harmony instead of clashing with the new drone/bed. */
void controls_refresh_held_pitches(void);

#endif
