Sancte3D/AMBIENT/field-ambience-current/firmware-c-next/src/engine.c

/*
 * Audio engine — Step 11 mix-bus owner.
 *
 * Static float scratch buffers (BLOCK frames) keep allocation out of the
 * audio path. BLOCK matches AUDIO_BUFFER_FRAMES (256) — audio.c calls in
 * chunks of that size, so we always process a whole audio block in one pass.
 *
 * `send` and `wet_amp` are smoothed per block (~120 ms) to avoid zipper
 * when the user knobs them; size/damp/drive are smoothed inside the reverb
 * itself.
 */

#include "engine.h"
#include "pad.h"
#include "reverb.h"
#include "fx_master.h"
#include "texture.h"
#include "ambience.h"
#include "bass.h"
#include "drone.h"
#include "reverb_presets.h"
#include "brain.h"
#include "worlds.h"
#include "generative.h"
#include "cells.h"
#include "pluck.h"
#include "glass.h"
#include "ember.h"
#include "padsynth.h"
#include "body.h"
#include "composer.h"
#include "harmony.h"
#include "tuning.h"
#include "dsp.h"
#include "audio.h"                    /* AUDIO_BUFFER_FRAMES */
#include <math.h>
#include <string.h>

/* Per-layer reverb sends (match the webapp's per-voice verbSend values).
 * Pad uses the user-tunable engine_set_send; texture has its own fixed send;
 * the bass applies its two per-layer sends internally. */
#define TEXTURE_SEND  0.55f
#define AMBIENCE_SEND 0.35f           /* slightly less wet than texture — ADR-0017 */

/* Active note tracking so the bass can follow the lowest held pitch. Sources
 * are cell indices today (0..4), with headroom for MIDI later. freq 0 = idle. */
#define MAX_SOURCES   16
#define GEN_SOURCE    8           /* reserved pad-voice source for the bed */
#define GEN_VOICE_AMP 0.10f
static float active_freq[MAX_SOURCES];

/* Optional note-event tap (MIDI out lives behind this so the engine keeps no
 * link dependency on midi.c — the product wires it in main_h743). on: 1=on,
 * 0=off, -1=all-off. */
static engine_note_hook_t s_note_hook = 0;
void engine_set_note_hook(engine_note_hook_t h) { s_note_hook = h; }

/* r19.16 SYNTH-mode state (logic lives beside engine_render below). */
static const engine_synth_backend_t *s_synth_be = 0;
static volatile int s_synth_tgt = 0;       /* set at control rate            */
static int   melody_voice;          /* r18.98 VOICE: 0 PAD, 1 STRING, 2 GLASS */

/* r18.99 ENO LOOPS — the Music-for-Airports principle (studied via the
 * teropa "loop" essay on Reich's It's Gonna Rain and Eno's airport loops;
 * technique reconstructed, nothing to copy): several long loops, ONE note
 * per loop, with INCOMMENSURATE periods that never re-align — the bed
 * stops being one held chord root and becomes a slowly recombining choir.
 * Three loops on pad sources 5..7, periods chosen pairwise non-multiple
 * (13.7 / 21.3 / 33.1 s — no common divisor within hours). Each cycle the
 * loop re-picks ITS chord member (root/third/fifth) from the CURRENT
 * harmony, so the recombination always lands inside the key. Autoplay
 * only — a playing human owns the bed. */
#define ENO_LOOPS 3
static const uint32_t ENO_PERIOD_MS[ENO_LOOPS] = { 13700u, 21300u, 33100u };
static const float    ENO_AMP[ENO_LOOPS]       = { 0.050f, 0.044f, 0.038f };
static uint32_t eno_next_ms[ENO_LOOPS];
static uint32_t eno_off_ms[ENO_LOOPS];
static uint8_t  eno_on[ENO_LOOPS];
static int      eno_timing_valid;
/* r19.41: reverse swell for SCHEDULED notes only (task rule — a live key
 * press cannot be preceded without look-ahead latency). The Eno loops are
 * the composer's genuinely pre-known events: after each fire the next fire
 * time is exact, so the swell triggers SWELL_LEAD_MS before it with the
 * same lead. One-shot per cycle. */
#define ENO_SWELL_LEAD_MS 1500u
static uint8_t  eno_swell_armed[ENO_LOOPS];
#define ENO_SRC(i) ((uint8_t)(5 + (i)))

/* Generative state (r19.0: rebuilt on the HARMONIC SAFETY CORE, see
 * harmony.h — pitch world → register rules → state mutation → collision
 * filter → long melody → probability LAST). The old per-bar chord walk +
 * sparkle scheduler is gone: the bed follows the harmonic STATE, the
 * melody is one LONG voice with real silences. */
static bool     gen_on = false;
static bool     gen_timing_valid = false;
static uint32_t gen_tick_rng     = 0x5EEDBA55u;
static int      gen_state_seen   = -1;   /* bed re-strikes on state change */
/* r19.33 player-priority state (declared here so engine_init can reset it). */
#define GEN_RETURN_MS   8000u            /* auto-content returns ~8 s after play */
static uint32_t s_last_active_ms = 0;
static bool     s_ever_active     = false;
static bool     s_gen_suppressed  = false;
/* r19.34 — the two sparse single-tone autoplay layers, each toggleable so the
 * player can keep the evolving bed/pad without the lonely melodic events. */
static bool     s_mel_enabled = true;    /* long lead melody voice           */
static bool     s_eno_enabled = true;    /* three one-note Eno tape loops     */
static bool     s_gentle_return = false; /* r19.34: first melody note after the
                                          * player-priority silence swells in
                                          * softly (no bright ding, low register) */
void engine_set_autoplay_melody(int on) { s_mel_enabled = on ? true : false; }
void engine_set_autoplay_eno   (int on) { s_eno_enabled = on ? true : false; }
int  engine_autoplay_melody(void)        { return s_mel_enabled ? 1 : 0; }
int  engine_autoplay_eno(void)           { return s_eno_enabled ? 1 : 0; }

/* Long melody voice: pad source 15 sustains 4-16 s, the selected VOICE
 * (string/glass) strikes the onset. */
#define MEL_SRC 15
static uint32_t mel_next_ms;          /* next decision time              */
static uint32_t mel_off_ms;           /* scheduled note-off              */
static int      mel_sounding;
static int      mel_phrase_left;      /* notes left in current phrase    */
static int      mel_last_midi;        /* voice-leading memory (0 = none) */
static int      mel_note_count;       /* observability (tests/UI)        */

/* déjà-vu phrase memory (Marbles concept, kept from r18.93): the last
 * completed phrase replays with p=0.35 — but EVERY remembered tone must
 * still pass the current pitch world + collision filter, else the picker
 * falls through to a fresh safe choice. The motif survives, the safety
 * rules always win. */
#define MEL_PHRASE_MAX 6
static int mel_hist[MEL_PHRASE_MAX]; static int mel_hist_len = 0;
static int mel_cur [MEL_PHRASE_MAX]; static int mel_cur_len  = 0;
static int mel_replay = 0, mel_replay_idx = 0;
static int mel_dejavu_count = 0;

/* sounding-note registry for the collision filter (0 = silent) */
static int snd_bed_midi = 0;
static int snd_eno_midi[ENO_LOOPS];

/* r19.0 spectral undulation (Blendwave principle from the Liven Ambient
 * Ø study): a held tone must LIVE. Correlated random walk on the pad's
 * brightness tilt — small persistent steps, never a jump — so the bed
 * undulates without a single new note event. */
static float    vmix_walk = 0.0f;
static uint32_t vmix_next_ms = 0;

/* Lowest currently-held frequency, or 0 if nothing is held. */
static float lowest_held(void) {
    float lo = 0.0f;
    for (int i = 0; i < MAX_SOURCES; ++i) {
        if (i >= 5 && i <= 7) continue;   /* r18.99: Eno loops are colour,
                                           * not fundament — bass ignores them */
        float f = active_freq[i];
        if (f > 0.0f && (lo == 0.0f || f < lo)) lo = f;
    }
    return lo;
}

/* Re-point the bass at the current lowest note, or release it if none held. */
/* r19.31: when a cell mode owns the bass explicitly (HARMONY bass modes), the
 * engine stops auto-following the lowest held note. NOTE/LAND keep following. */
static bool s_bass_follow = true;
void engine_bass_follow(bool on) { s_bass_follow = on; }
void engine_bass_set(float freq_hz) { if (freq_hz > 1.0f) bass_note(freq_hz); }
void engine_bass_off(void)          { bass_release(); }
void engine_bass_glide(float tau_s) { bass_set_glide(tau_s); }
bool engine_bass_active(void)       { return bass_active(); }

static void refresh_bass(void) {
    if (!s_bass_follow) return;                /* a cell mode drives it itself */
    float lo = lowest_held();
    if (lo > 0.0f) bass_note(lo);
    else           bass_release();
}

#define BLOCK     AUDIO_BUFFER_FRAMES

static float dryL [BLOCK];
static float dryR [BLOCK];
static float sendL[BLOCK];
static float sendR[BLOCK];

static float send_amount_cur, send_amount_tgt;
static float wet_amp_cur,     wet_amp_tgt;
static float reverb_size, reverb_damp;        /* cached, so the two setters
                                                  can change one independently */
/* r18.90: BRIGHTNESS is a macro, not a filter knob — it also tilts the
 * hall damping (dark = duller tail) and the pluck damping. This trim rides
 * ON TOP of the preset/manual damp so preset changes keep working. */
static float bright_damp_trim = 0.0f;

static void reverb_apply(void) {
    reverb_set(reverb_size,
               dsp_clampf(reverb_damp + bright_damp_trim, 0.0f, 1.0f));
}
static const float SMOOTH_COEF = 0.05f;       /* per-block, ~120 ms time-const */

/* Master stage (fixes the listening-test "earrape / brummt"):
 *   1. one-pole DC blocker (~35 Hz highpass) removes DC + subsonic rumble that
 *      otherwise builds up from the brown-noise bed, the bass and the reverb
 *      feedback — this is the "LeakDC" the Step-11 plan called for.
 *   2. master volume gives headroom (no on-device volume knob yet).
 *   3. a soft limiter that is PERFECTLY LINEAR below the knee and only rounds
 *      true peaks — replaces the old tanf() that distorted everything above
 *      ~0.5 (that continuous saturation was the harshness). */
#define DC_R 0.995f                           /* one-pole HP, ≈35 Hz at 44.1 k */
static float dc_x1L, dc_y1L, dc_x1R, dc_y1R;
static float master_vol_cur, master_vol_tgt;

/* r18.89 — master DRIVE stage. The DRIVE encoder used to reach only the
 * reverb-input saturation, so on a dry-ish patch the knob did almost
 * nothing. Now it drives the WHOLE mix through an asymmetric soft
 * saturator (dsp_drive_shape: tanh with a bias skew → even harmonics)
 * with small-signal makeup, placed BEFORE the DC blocker (the bias makes
 * a touch of DC — the blocker eats it) and before the tape stage, so
 * drive pushes INTO the tape knee like a real chain. 0 = bit-transparent
 * bypass. */
static float drive_cur, drive_tgt;

static inline float soft_limit(float x) {
    const float k = 0.75f;                    /* clean below this */
    float a = x < 0.0f ? -x : x;
    if (a <= k) return x;                     /* transparent for normal levels */
    float over = a - k;                       /* smoothly map (k..∞) → (k..1) */
    float comp = k + (1.0f - k) * (over / (over + (1.0f - k)));
    return x < 0.0f ? -comp : comp;
}

/* Step 12b #1 — musical state driving the preset-based reverb mapping. */
static int   musical_mode  = 0;     /* ionian */
static int   musical_vibe  = 0;     /* warm */
static float musical_space = 0.5f;
static float musical_mood  = 0.5f;

/* Recompute Freeverb settings from current mode/vibe/space/mood and push to
 * the reverb. Cached size/damp keep manual reverb setters orthogonal. */
static void recompute_reverb_from_presets(void) {
    reverb_settings_t s = reverb_presets_compute(musical_mode, musical_vibe,
                                                 musical_space, musical_mood);
    reverb_size = s.size;
    reverb_damp = s.damp;
    reverb_apply();
    reverb_set_drive(s.drive);
    wet_amp_tgt = s.wet_amp;        /* still smoothed per block in render */
}

void engine_init(void) {
    pad_init();
    reverb_init();      /* tank still owned by the V2 synth hosts (SYNTH mode) */
    texture_init();
    ambience_init();
    /* r19.41: the legacy master processors (tape/echo/blur/shimmer + master
     * reverb render) are replaced by the ambient effects engine. Init runs
     * here — outside the audio callback — and FAILS CLOSED to dry audio. */
    fx_master_init();
    bass_init();
    drone_init();

    /* Musical state defaults: C ionian / warm / space=mood=0.5. The reverb
     * parameters fall out of the preset table — same shape as the webapp's
     * mid-mode landing point. */
    musical_mode  = 0;
    musical_vibe  = 0;
    musical_space = 0.5f;
    musical_mood  = 0.5f;
    send_amount_cur = send_amount_tgt = 0.45f;
    wet_amp_cur     = wet_amp_tgt     = 0.40f;
    recompute_reverb_from_presets();
    wet_amp_cur = wet_amp_tgt;       /* snap at boot, no glide-from-silence */

    /* Texture bed boots at 0 (silent power-up); raise via engine_set_texture
     * or the brain in Step 12. */
    texture_set_amount(0.0f);
    bass_set_depth(0.5f);
    memset(active_freq, 0, sizeof active_freq);
    generative_init();
    cells_init();                    /* ADR-0013 cell-velocity state */
    gen_on = false;
    gen_timing_valid = false;        /* r18.88 autoplay scheduler reset */
    s_gen_suppressed = false;        /* r19.33 player-priority state reset */
    s_ever_active    = false;
    s_last_active_ms = 0;
    s_mel_enabled    = true;         /* r19.34 autoplay layers on by default */
    s_eno_enabled    = true;
    s_gentle_return  = false;
    composer_init();                 /* r18.96 top-level intent reset   */
    harmony_init();                  /* r19.0 harmonic safety core */
    gen_state_seen = -1;
    mel_next_ms = 0; mel_off_ms = 0; mel_sounding = 0;
    mel_phrase_left = 0; mel_last_midi = 0; mel_note_count = 0;
    mel_hist_len = mel_cur_len = 0;
    mel_replay = 0; mel_replay_idx = 0;
    mel_dejavu_count = 0;
    snd_bed_midi = 0;
    memset(snd_eno_midi, 0, sizeof snd_eno_midi);
    vmix_walk = 0.0f; vmix_next_ms = 0;

    /* Master stage: DC-block cleared, moderate default volume (no on-device
     * volume knob bound yet — keeps headphones from being slammed). */
    dc_x1L = dc_y1L = dc_x1R = dc_y1R = 0.0f;
    master_vol_cur = master_vol_tgt = 0.6f;
    drive_cur = drive_tgt = 0.0f;
    pluck_init();                    /* r18.89 sparkle plucks */
    glass_init();                    /* r18.98 FM glass voice */
    ember_init();                    /* r19.28 warm subtractive analog voice */
    memset(eno_next_ms, 0, sizeof eno_next_ms);
    memset(eno_off_ms,  0, sizeof eno_off_ms);
    memset(eno_on,      0, sizeof eno_on);
    memset(eno_swell_armed, 0, sizeof eno_swell_armed);
    eno_timing_valid = 0;
    melody_voice = 0;                /* PAD — the bench-tuned reference */
    body_init();                     /* r18.94 modal body (per-world material) */

    /* Boot world 0 (Tokyo) — align the harmonic identity with the displayed
     * world so the first cell tap already plays in A-major, not the bare
     * C-ionian default. Sets brain key/mode/vibe + ambience world + reverb
     * preset; produces no sound (no notes held). */
    engine_set_world(0);
}

/* r18.98 VOICE — the melody-instrument selector (user: "das Instrument
 * kann nicht genug"). 0 = PAD (reference sound, cells swell as before),
 * 1 = STRING, 2 = GLASS: every cell press ADDITIONALLY strikes the chosen
 * melody voice, so playing gets an articulate attack in front of the pad
 * swell — piano-into-pad feel. The generative sparkles follow the same
 * choice (GLASS replaces the KS string; PAD keeps the string — the bed
 * needs SOME second colour, that was the whole r18.89 point). */
void engine_set_voice(int voice_idx) {
    if (voice_idx < 0) voice_idx = 0;
    if (voice_idx > 3) voice_idx = 3;    /* r19.28: 3 = Ember (optional)   */
    melody_voice = voice_idx;
}

/* Fire the selected melody voice (used by cell presses + sparkles). */
static void melody_strike(float freq_hz, float amp) {
    if      (melody_voice == 3) ember_note(freq_hz, amp);   /* r19.28 analog */
    else if (melody_voice == 2) glass_note(freq_hz, amp);
    else                        pluck_note(freq_hz, amp);
}

/* r19.28 — Landscape "Motif" layer: a warm subtractive ANALOG voice (ember.c:
 * detuned saws + sub, a resonant filter with its own decay envelope, and a
 * delayed vibrato LFO). The FM bell (r19.27.1) read as dead/static; this is a
 * moving, nostalgic tone — independent of the global VOICE menu. */
void engine_motif_strike(float freq_hz, float amp) {
    ember_note(freq_hz, dsp_clampf(amp, 0.0f, 0.30f));
}

/* r19.30 — a bare glass/bell bloom for the HARMONY "extension" role: the FM
 * shimmer that lets a chord's top sparkle over the sustained pad body, and
 * decays into the shared hall. No pad, no bass. */
void engine_sparkle_strike(float freq_hz, float amp) {
    glass_note(freq_hz, dsp_clampf(amp, 0.0f, 0.30f));
}

/* Tier A #2: tiny LCG for micro-humanisation. Inside JND so it doesn't drift
 * audibly, but enough that two consecutive identical cell taps aren't
 * bit-identical → no "mechanical" feel on repeats. */
static uint32_t humanize_rng = 0xA5C3F19Du;
static inline float humanize_rand_unit(void){      /* in [-1, +1] */
    humanize_rng = humanize_rng * 1664525u + 1013904223u;
    return ((int32_t)humanize_rng) * (1.0f / 2147483648.0f);
}

void engine_note_on(uint8_t source, float freq_hz, float amp) {
    /* ±0.5 cent pitch jitter, ±0.3 % amp jitter. Bass / drone get the same
     * freq downstream (refresh_bass) so the jitter is consistent per press. */
    float pitch_jitter = humanize_rand_unit() * (0.5f / 1200.0f);   /* cents */
    float amp_jitter   = humanize_rand_unit() * 0.003f;
    freq_hz *= 1.0f + pitch_jitter;                    /* 2^(jit) ≈ 1+jit at tiny jit */
    amp     *= 1.0f + amp_jitter;
    if (s_note_hook) s_note_hook(1, source, freq_hz, amp);
    /* r19.16 SYNTH mode: played cells drive the V2 sound-core instead of the
     * pad. Generative/drone sources never reach V2 (it's a played mono synth). */
    if (s_synth_tgt > 0 && s_synth_be &&
        (source <= 4 || (source >= 9 && source <= 13))) {
        int n = (int)lrintf(69.0f + 12.0f * log2f(freq_hz / 440.0f));
        if (n < 0)   n = 0;
        if (n > 127) n = 127;
        s_synth_be->note_on(n, dsp_clampf(amp, 0.0f, 1.0f));
        if (source < MAX_SOURCES) active_freq[source] = freq_hz;
        return;
    }
    pad_note_on(source, freq_hz, amp);
    if (source < MAX_SOURCES) active_freq[source] = freq_hz;
    /* r18.98 VOICE: cell sources (base 0..4 + shift 9..13) also strike the
     * selected melody voice — an articulate attack in front of the pad
     * swell. The generative bed (8) and sparkles (14/15) are excluded:
     * the bed must stay a bed. Amp is scaled to sit like the sparkles. */
    if (melody_voice != 0 &&
        (source <= 4 || (source >= 9 && source <= 13)))
        melody_strike(freq_hz, dsp_clampf(amp * 1.4f, 0.0f, 0.30f));
    refresh_bass();
}
void engine_note_off(uint8_t source) {
    if (s_note_hook && source < MAX_SOURCES)
        s_note_hook(0, source, active_freq[source], 0.0f);
    if (s_synth_tgt > 0 && s_synth_be &&
        (source <= 4 || (source >= 9 && source <= 13))) {
        s_synth_be->note_off();                        /* V2 core is mono */
        if (source < MAX_SOURCES) active_freq[source] = 0.0f;
        return;
    }
    pad_note_off(source);
    if (source < MAX_SOURCES) active_freq[source] = 0.0f;
    refresh_bass();
}
void engine_all_off(void) {
    if (s_note_hook) s_note_hook(-1, 0, 0.0f, 0.0f);   /* all-off sentinel */
    if (s_synth_tgt > 0 && s_synth_be) s_synth_be->panic();
    pad_all_off();
    memset(active_freq, 0, sizeof active_freq);
    bass_release();
}

/* ADR-0013 — Hall cell sample → velocity note. The cell index doubles as the
 * pad-voice source (0..4), matching the digital-cell path, so re-pressing a
 * cell re-blooms its own voice rather than stacking. */
bool engine_cell_sample(uint8_t cell, float pos_0_1, uint32_t now_ms) {
    cell_event_t ev = cells_update(cell, pos_0_1, now_ms);
    if (ev.kind == CELL_EVENT_PRESS) {
        int midi = brain_cell_root(ev.cell);
        engine_note_on(ev.cell, tuning_hz((float)midi), ev.amp);
        return true;
    }
    if (ev.kind == CELL_EVENT_RELEASE) {
        engine_note_off(ev.cell);
        return true;
    }
    return false;
}

void engine_set_reverb_size(float v) {
    reverb_size = dsp_clampf(v, 0.0f, 1.0f);
    reverb_apply();
}
void engine_set_reverb_damp(float v) {
    reverb_damp = dsp_clampf(v, 0.0f, 1.0f);
    reverb_apply();
}
void engine_set_reverb_drive(float v) { reverb_set_drive(dsp_clampf(v, 0.0f, 1.0f)); }
void engine_set_wet_amp(float v)      { wet_amp_tgt    = dsp_clampf(v, 0.0f, 1.0f); }
void engine_set_send(float v)         { send_amount_tgt = dsp_clampf(v, 0.0f, 1.0f); }
void engine_set_master_volume(float v){ master_vol_tgt  = dsp_clampf(v, 0.0f, 1.0f); }
void engine_boot_mute(void)           { master_vol_cur  = master_vol_tgt = 0.0f; }
void engine_set_drive(float v)        { drive_tgt       = dsp_clampf(v, 0.0f, 1.0f); }
/* r18.90 macro: one emotional dimension, three destinations. hz is the
 * legacy pad-cutoff offset (-600..+800); the hall and the plucks follow.
 * At hz=0 all trims are exactly 0 — the bench-tuned default is untouched. */
void engine_set_brightness(float hz)  {
    pad_set_brightness(hz);
    bright_damp_trim = dsp_clampf(-hz * (0.18f / 800.0f), -0.135f, 0.18f);
    reverb_apply();
    pluck_set_damp(dsp_clampf(0.42f - hz * (0.12f / 800.0f), 0.28f, 0.55f));
    /* r19.41: the master-effects tone follows the same macro (hz -600..+800
     * → 0..1, centre unchanged at the world default until the user moves it). */
    fx_master_set_tone((hz + 600.0f) / 1400.0f);
}
void engine_set_texture(float v)      { texture_set_amount(dsp_clampf(v, 0.0f, 1.0f)); }
void engine_set_atmosphere(float v)   {
    v = dsp_clampf(v, 0.0f, 1.0f);
    ambience_set_level(v);               /* per-world atmospheric sound layer */
    fx_master_set_atmosphere(v);         /* r19.41: global spatial send       */
}
/* World change applies BOTH the texture layer (ambience) AND the harmonic
 * identity (key/mode/vibe) so each world sounds musically distinct, not just
 * texturally. The cell taps then play in the world's key/mode (brain), the
 * drone follows the root, and the reverb character shifts via the per-mode/
 * vibe preset table. Values live in worlds.c (audition-derived). */
void engine_set_world(int idx) {
    ambience_set_world(idx);
    /* r18.93: (re)build the PADsynth bed table for the world's timbre
     * profile. Blocking a few ms — worlds change from the UI loop, never
     * the audio IRQ; the pad keeps reading the old table until the final
     * copy, and the world-change re-bloom masks the swap. */
    padsynth_build(idx, 0);
    body_set_world(idx);             /* r18.94: the pluck's resonant material */
    const world_t *w = worlds_get(idx);
    engine_set_key ((int)w->key_midi);   /* brain key + drone root          */
    engine_set_mode((int)w->mode);       /* brain mode + reverb recompute   */
    engine_set_vibe((int)w->vibe);       /* brain vibe + reverb recompute   */
    /* r19.41: master-effects world voicing (Tokyo/Coast/Drive/Hours map 1:1
     * onto the engine worlds). The menu pushes its macro values right after
     * this call, overwriting the user-facing fields — the engine keeps its
     * curated width/tone/level/delay for the world. */
    fx_master_set_world(idx);
}
void engine_set_bass_depth(float v)   { bass_set_depth(dsp_clampf(v, 0.0f, 1.0f)); }

/* Perform-macros: combine multiple internal params under one user knob. */
void engine_set_motion(float v) {
    v = dsp_clampf(v, 0.0f, 1.0f);
    /* user 0..1 → pad-LFO depth 0..2 (centre 0.5 = default movement). */
    pad_set_motion(v * 2.0f);
    fx_master_set_motion(v);             /* r19.41: chorus/slow modulation */
}
void engine_set_age(float v) {
    /* r19.41: wow, flutter, bandwidth loss, saturation, hiss and hum all
     * live in the master-effects engine now (its `age` parameter) — the
     * legacy tape module left the audio path with the engine swap. */
    fx_master_set_age(dsp_clampf(v, 0.0f, 1.0f));
}

/* SHIMMER macro (menu slot). r19.41: restrained octave regeneration inside
 * the master-effects engine (replaces the legacy shimmer wrap-loop). */
void engine_set_shimmer(float v) {
    fx_master_set_shimmer(dsp_clampf(v, 0.0f, 1.0f));
}

/* Echo macro. r19.41: filtered ping-pong delay inside the master-effects
 * engine (replaces the legacy echo.c tape-style delay). */
void engine_set_echo(float v) {
    fx_master_set_echo(dsp_clampf(v, 0.0f, 1.0f));
}

/* Blur macro. r19.41: deterministic temporal blur inside the master-effects
 * engine (replaces the legacy blur.c granular cloud). */
void engine_set_blur(float v) {
    fx_master_set_blur(dsp_clampf(v, 0.0f, 1.0f));
}

/* r19.41 FX effect page: 0=Bypass..8=Dream Chain (menu slot; Dream Chain is
 * the boot default, single modes stay selectable for A/B listening). */
void engine_set_fx_mode(int idx)       { fx_master_set_mode(idx); }
int  engine_fx_mode(void)              { return fx_master_mode(); }
int  engine_fx_mode_count(void)        { return fx_master_mode_count(); }
const char *engine_fx_mode_name(int i) { return fx_master_mode_name(i); }

/* Step 12b #1 — musical-state setters. Each triggers a preset recompute so
 * the reverb shifts character with the mode/vibe/macro change. The reverb
 * itself smooths internally (~120 ms), so the transition is glide-not-step
 * — matches the "sound darf nicht konkurrieren" rule for global params.
 * Also keeps the harmonic brain's view of mode/vibe in sync so cells played
 * after the change pick up the new harmony. */
/* r19.0: the harmony core needs TONALITY, not the full mode. Dorian /
 * phrygian / aeolian read as minor pitch worlds; ionian / lydian /
 * mixolydian as major. */
static int mode_is_minor(int mode_idx) {
    return mode_idx == 1 || mode_idx == 2 || mode_idx == 5;
}

void engine_set_mode(int mode_idx) {
    if (mode_idx < 0)               mode_idx = 0;
    if (mode_idx >= RP_MODE_COUNT)  mode_idx = RP_MODE_COUNT - 1;
    musical_mode = mode_idx;
    brain_set_mode(mode_idx);
    harmony_set_world(brain_get_key(), mode_is_minor(mode_idx));   /* r19.0 */
    recompute_reverb_from_presets();
}
void engine_set_vibe(int vibe_idx) {
    if (vibe_idx < 0)               vibe_idx = 0;
    if (vibe_idx >= RP_VIBE_COUNT)  vibe_idx = RP_VIBE_COUNT - 1;
    musical_vibe = vibe_idx;
    brain_set_vibe(vibe_idx);
    recompute_reverb_from_presets();
}
void engine_set_space(float v) {
    musical_space = dsp_clampf(v, 0.0f, 1.0f);
    recompute_reverb_from_presets();     /* V2 synth hosts still use the tank */
    fx_master_set_space(musical_space);  /* r19.41: master-effects room scale */
}
void engine_set_mood(float v) {
    musical_mood = dsp_clampf(v, 0.0f, 1.0f);
    recompute_reverb_from_presets();
}
/* r18.98 KEY as a menu slot: the menu speaks PITCH CLASS (0=C..11=B); the
 * engine anchors it in the register the four world tonics live in
 * (F#3..F4, MIDI 54..65) so a key change transposes, never jumps octaves:
 * pc 6..11 → 54..59, pc 0..5 → 60..65. Tokyo A=57, Coast D=62,
 * Drive F#=54, Hours C=60 all round-trip exactly. */
void engine_set_key_pc(int pc) {
    pc %= 12; if (pc < 0) pc += 12;
    engine_set_key(pc >= 6 ? 48 + pc : 60 + pc);
}

void engine_set_key(int tonic_midi) {
    brain_set_key(tonic_midi);
    harmony_set_world(tonic_midi, mode_is_minor(musical_mode));    /* r19.0 */
    tuning_set_key(tonic_midi);        /* r19.6 anchor just intonation      */
    drone_set_root_midi(tonic_midi);   /* glides live if the drone is sounding */
}
void engine_set_drone(bool on) { drone_enable(on); }

/* r19.6 — tuning: 0 = equal temperament (reference), 1 = just intonation. */
void engine_set_tuning(int just) { tuning_set_mode(just); }

/* PAD_VOICE_MIXES from the webapp: warm / strings / brass. */
void engine_set_pad_voice(int voice_idx) {
    static const float MIX[] = { 0.0f, 0.6f, 1.2f };
    if (voice_idx < 0) voice_idx = 0;
    if (voice_idx > 2) voice_idx = 2;
    pad_set_voice_mix(MIX[voice_idx]);
}

/* r19.20 — the generative gate is PHYSICAL now. History: r18.88 gated on
 * "any active cell voice" (sources 0..4 + 9..13) so the bed would not play
 * over held notes. That fixed momentary playing but created the
 * HOLD+GENERATE deadlock: a hold-LATCHED voice keeps its source active
 * forever, so one latched drone note froze autoplay permanently. The gate
 * is now the physical key state fed by controls.c (press/release edges):
 * while a finger is down the composer yields; latched voices are standing
 * texture the generator plays AROUND (their sources stay protected simply
 * because the generator only ever writes its own sources 8/14/15). */
static bool s_user_present = false;
void engine_set_user_presence(bool any_key_down) { s_user_present = any_key_down; }

/* r19.33 — player takes priority (musical "listening"): the bed + melody hold
 * off while the user plays AND for GEN_RETURN_MS after the last release, then
 * return gently. State lives up top so engine_init can reset it. */
int engine_generative_suppressed(void) { return s_gen_suppressed ? 1 : 0; }

/* --- Generative autoplay (r18.88) -----------------------------------------
 * The GENERATE modifier was always meant to make the instrument PLAY BY
 * ITSELF (passive mode = music without hands). The old wiring gave one
 * chord-root swell per fixed 8 s bar, with up to 8 s of silence after
 * enabling. engine_generative_tick() replaces the caller-side bar timer:
 *
 *   - the FIRST bed note sounds on the first tick after enabling (no wait),
 *   - bar length is humanized (±10 % per bar, LCG — never metronomic),
 *   - each bar scatters 0-2 "sparkle" chord tones an octave up (sources
 *     14/15, ~3 s ring, quiet), so the bed breathes as actual music,
 *   - live playing still overrides everything: while any user note is held
 *     (base or shift) no new bed/sparkle notes start; ringing sparkles are
 *     still released on schedule. When the user lets go, the bed resumes on
 *     the next tick.
 *
 * All timing derives from the passed now_ms — hardware-independent and
 * host-testable. The old engine_generative_advance() stays as the manual
 * step API (offline renderers, tests). State lives up by gen_on. */

uint32_t engine_gen_seed(void)          { return gen_tick_rng; }
void     engine_set_gen_seed(uint32_t s) { gen_tick_rng = s ? s : 0x5EEDBA55u; }

static float gen_rand01(void) {
    gen_tick_rng = gen_tick_rng * 1664525u + 1013904223u;
    return (float)(gen_tick_rng >> 8) / 16777216.0f;
}

void engine_set_generative(bool on, int program) {
    generative_set_program(program);
    if (on && !gen_on) gen_timing_valid = false;   /* first tick plays NOW */
    gen_on = on;
    if (!on) {
        engine_note_off(GEN_SOURCE);    /* release the bed voice */
        snd_bed_midi = 0;
        engine_note_off((uint8_t)MEL_SRC);   /* r19.0: melody voice too */
        mel_sounding = 0;
        for (int i = 0; i < ENO_LOOPS; ++i) {   /* r18.99: loops out too */
            if (eno_on[i]) engine_note_off(ENO_SRC(i));
            eno_on[i] = 0;
            snd_eno_midi[i] = 0;
        }
        eno_timing_valid = 0;
    }
}

/* r19.0: manual step = one harmonic-state MUTATION (≥3 common pitch
 * classes, ≤2 voices move — harmony.c enforces the contract). The pad
 * bed voice sits an octave over the bass register; bass.c derives the
 * low fundament from it (lowest_held). Returns state index + 1 (1..4). */
/* r19.24 — the five cells as composer intents (see engine.h). Deliberately
 * a MAPPING of gestures to the existing composer states, not a claim that
 * harmony pitch-picks encode tension: the directional FEEL comes from the
 * composer table (density/depth/rest), and harmony_advance() moves the
 * actual voicing so the answer is heard. */
static const composer_state_t CELL_INTENT[5] = {
    COMPOSER_RETURN,   /* 0 Home / Resolve — warmth back            */
    COMPOSER_OPEN,     /* 1 Lift           — more light, denser      */
    COMPOSER_DEEP,     /* 2 Dark           — floor rises, melody recedes */
    COMPOSER_CALM,     /* 3 Open           — spacious resting rate    */
    COMPOSER_EMPTY,    /* 4 Tension        — the held breath          */
};

void engine_generative_nudge(int cell, uint32_t now_ms) {
    if (!gen_on || cell < 0 || cell > 4) return;
    composer_nudge(CELL_INTENT[cell], now_ms);
    harmony_advance();               /* move the harmonic state NOW */
    gen_state_seen = -1;             /* re-sound the bed on the next tick */
}

void engine_generative_new_field(uint32_t seed) {
    engine_set_gen_seed(seed);
    composer_reseed(seed ^ 0x9E3779B9u);
    harmony_reseed(seed ^ 0x85EBCA6Bu);
    /* restart the field at state 0 in the SAME pitch world (key/mode) */
    harmony_set_world(brain_get_key(), mode_is_minor(musical_mode));
    composer_init();                 /* fresh intent clock; reseed below   */
    composer_reseed(seed ^ 0x9E3779B9u);
    gen_timing_valid = false;        /* strike fresh on the next tick */
    gen_state_seen   = -1;
}

int engine_generative_advance(void) {
    if (!gen_on) return -1;
    if (s_user_present || s_gen_suppressed) return -1;   /* r19.33: player + return-delay */
    harmony_advance();
    int midi = harmony_bass_midi() + 12;
    snd_bed_midi = midi;
    gen_state_seen = harmony_state_changes();
    engine_note_on((uint8_t)GEN_SOURCE, tuning_hz((float)midi),
                   GEN_VOICE_AMP * composer_params()->bed_amp);
    return harmony_state_index() + 1;
}

int engine_generative_last_melody_midi(void) { return mel_last_midi; }
int engine_generative_melody_count(void)     { return mel_note_count; }
int engine_generative_dejavu_count(void)     { return mel_dejavu_count; }

void engine_generative_tick(uint32_t now_ms) {
    if (!gen_on) return;
    /* r18.96 — the COMPOSER above the grammar (Atmoscapia/Eno principle:
     * a slow top-level intent that only re-weights probabilities; see
     * composer.h). Ticks on the same clock as everything else. */
    composer_tick(now_ms);

    /* r19.33 — player-priority "listening": suppressed while a key is down AND
     * for GEN_RETURN_MS after the last release, so the machine steps back and
     * lets the player breathe, then returns gently (the re-arm below strikes
     * the bed and schedules the first melody note 1.5–4 s later). */
    if (s_user_present) { s_last_active_ms = now_ms; s_ever_active = true; }
    bool suppressed = s_user_present ||
        (s_ever_active && (uint32_t)(now_ms - s_last_active_ms) < GEN_RETURN_MS);
    if (suppressed != s_gen_suppressed) {
        s_gen_suppressed = suppressed;
        if (suppressed) {
            if (mel_sounding) {             /* hush the auto melody as the player takes over */
                engine_note_off((uint8_t)MEL_SRC);
                mel_sounding = 0;
            }
        } else {
            s_gentle_return = true;         /* the piece comes back softly, not with a ding */
        }
    }
    if (suppressed) {
        gen_timing_valid = false;
        return;
    }

    if (!gen_timing_valid) {           /* just enabled / just released */
        gen_timing_valid = true;
        gen_state_seen = -1;           /* strike the bed on THIS tick   */
        mel_next_ms = now_ms + 1500u + (uint32_t)(gen_rand01() * 2500.0f);
        if (mel_sounding && (int32_t)(now_ms - mel_off_ms) >= 0) {
            engine_note_off((uint8_t)MEL_SRC);   /* stale note from before
                                                  * a long user hold      */
            mel_sounding = 0;
        }
    }

    /* --- r18.99 ENO LOOPS (see the block comment at the top) ------------
     * Three one-note tape loops with incommensurate periods. Staggered
     * first entries (0.4 / 0.62 / 0.81 of a period) so the choir fades in
     * voice by voice instead of striking a chord. Each cycle: release the
     * old tone, sound THIS loop's chord member of the CURRENT harmony,
     * hold for 62 % of the period, rest for the remainder — the gaps are
     * where the recombination shows. */
    if (!s_eno_enabled) {                /* r19.34: layer off → hush + re-arm */
        for (int i = 0; i < ENO_LOOPS; ++i)
            if (eno_on[i]) { engine_note_off(ENO_SRC(i)); eno_on[i] = 0; snd_eno_midi[i] = 0; }
        eno_timing_valid = 0;
    } else {
    if (!eno_timing_valid) {
        eno_next_ms[0] = now_ms + (uint32_t)(ENO_PERIOD_MS[0] * 0.40f);
        eno_next_ms[1] = now_ms + (uint32_t)(ENO_PERIOD_MS[1] * 0.62f);
        eno_next_ms[2] = now_ms + (uint32_t)(ENO_PERIOD_MS[2] * 0.81f);
        for (int i = 0; i < ENO_LOOPS; ++i) { eno_on[i] = 0; eno_off_ms[i] = 0; }
        eno_timing_valid = 1;
    }
    for (int i = 0; i < ENO_LOOPS; ++i) {
        if (eno_on[i] && (int32_t)(now_ms - eno_off_ms[i]) >= 0) {
            engine_note_off(ENO_SRC(i));
            eno_on[i] = 0;
            snd_eno_midi[i] = 0;
        }
        /* r19.41: the next fire time is exact — arm the reverse swell
         * exactly ENO_SWELL_LEAD_MS ahead of it, once per cycle. */
        if (!eno_swell_armed[i] &&
            (int32_t)(eno_next_ms[i] - now_ms) > 0 &&
            (uint32_t)(eno_next_ms[i] - now_ms) <= ENO_SWELL_LEAD_MS) {
            /* Predict the scheduled note from the CURRENT harmony with the
             * same register rule the fire branch applies. A state mutation
             * inside the lead window can shift it — the pre-tail is a
             * spectral gesture, not a pitch guarantee. */
            int hv[HARMONY_VOICES];
            harmony_voices(hv, HARMONY_VOICES);
            int midi = hv[i];
            while (midi > 74) midi -= 12;
            while (midi < 50) midi += 12;
            fx_master_trigger_swell(tuning_hz((float)midi),
                                    ENO_AMP[i] * composer_params()->bed_amp,
                                    (float)ENO_SWELL_LEAD_MS / 1000.0f);
            eno_swell_armed[i] = 1;
        }
        if ((int32_t)(now_ms - eno_next_ms[i]) >= 0) {
            /* r19.0: each loop owns ONE voice of the harmonic STATE (the
             * voiced, collision-safe upper harmony) — the recombination
             * always lands inside the pitch world. */
            int hv[HARMONY_VOICES];
            harmony_voices(hv, HARMONY_VOICES);
            {
                int midi = hv[i];
                while (midi > 74) midi -= 12;    /* keep the choir mid-low */
                while (midi < 50) midi += 12;
                if (eno_on[i]) engine_note_off(ENO_SRC(i));
                engine_note_on(ENO_SRC(i), tuning_hz((float)midi),
                               ENO_AMP[i] * composer_params()->bed_amp);
                eno_on[i]       = 1;
                snd_eno_midi[i] = midi;
                eno_off_ms[i] = now_ms + (uint32_t)(ENO_PERIOD_MS[i] * 0.62f);
            }
            /* phase NEVER resets — the drift is the composition. The while
             * catches up after a long user hold (ticks pause under a
             * playing human) without machine-gunning retriggers. */
            while ((int32_t)(now_ms - eno_next_ms[i]) >= 0)
                eno_next_ms[i] += ENO_PERIOD_MS[i];
            eno_swell_armed[i] = 0;      /* re-arm for the next known fire */
        }
    }
    }   /* r19.34: end of s_eno_enabled branch */

    /* --- r19.0 HARMONIC STATE (harmony.h) -------------------------------
     * The state machine dwells 24-48 s, then MUTATES: ≥3 common pitch
     * classes, ≤2 voices move, common tones frozen at pitch. The bed
     * re-sounds only when the state actually changed — held notes get
     * REINTERPRETED by the new bass, not re-struck (the user's research
     * brief: "Wir sollten Akkorde nicht auswählen, sondern den nächsten
     * harmonischen Zustand aus dem vorherigen mutieren"). */
    harmony_tick(now_ms);
    bass_set_depth(composer_params()->bass_depth);
    if (harmony_state_changes() != gen_state_seen) {
        gen_state_seen = harmony_state_changes();
        int midi = harmony_bass_midi() + 12;   /* pad bed over the bass reg;
                                                * bass.c derives the low
                                                * fundament via lowest_held */
        snd_bed_midi = midi;
        engine_note_on((uint8_t)GEN_SOURCE, tuning_hz((float)midi),
                       GEN_VOICE_AMP * composer_params()->bed_amp);
    }

    /* --- r19.0 LONG MELODY VOICE -----------------------------------------
     * One voice. Long tones (4-16 s), real silences (1-8 s, stretched by
     * the composer's rest_add), phrases of 2-5 notes with a longer breath
     * after each phrase. EVERY tone runs the full safety chain in
     * harmony_melody_next: pitch world → register mask → interval table →
     * collision filter against everything sustaining → next-best
     * fallback. Probability is the LAST stage, not the first. The onset
     * is doubled by the selected VOICE strike (string/glass) so the tone
     * has an attack in front of the pad swell — not an arpeggiator, a
     * slow cinematic line. */
    if (!s_mel_enabled) {                /* r19.34: melody layer off */
        if (mel_sounding) { engine_note_off((uint8_t)MEL_SRC); mel_sounding = 0; }
    } else {
    if (mel_sounding && (int32_t)(now_ms - mel_off_ms) >= 0) {
        engine_note_off((uint8_t)MEL_SRC);
        mel_sounding = 0;
        float rest = 1.0f + gen_rand01() * 7.0f;              /* 1-8 s   */
        rest *= 1.0f + composer_params()->rest_add * 2.0f;    /* composer */
        if (mel_phrase_left <= 0)
            rest += 3.0f + gen_rand01() * 5.0f;               /* breath  */
        mel_next_ms = now_ms + (uint32_t)(rest * 1000.0f);
    }
    if (!mel_sounding && (int32_t)(now_ms - mel_next_ms) >= 0) {
        if (mel_phrase_left <= 0) {
            if (mel_cur_len >= 2) {              /* archive the phrase   */
                for (int i = 0; i < mel_cur_len; ++i) mel_hist[i] = mel_cur[i];
                mel_hist_len = mel_cur_len;
            }
            mel_cur_len = 0;
            mel_phrase_left = 2 + (int)(gen_rand01() * 4.0f);   /* 2..5  */
            mel_replay = (mel_hist_len >= 2 && gen_rand01() < 0.35f);
            mel_replay_idx = 0;
            if (mel_replay) ++mel_dejavu_count;
            /* mel_last_midi is NOT reset: the new phrase steps off from
             * where the old one ended, so voice-leading survives the
             * breath (a reset caused over-octave leaps between phrases —
             * caught by the grammar audit). */
        }
        if (gen_rand01() < dsp_clampf(0.80f * composer_params()->mel_density,
                                      0.05f, 0.95f)) {
            /* everything currently sustaining, for the collision filter */
            int sus[2 + ENO_LOOPS]; int nsus = 0;
            if (snd_bed_midi) sus[nsus++] = snd_bed_midi;
            for (int i = 0; i < ENO_LOOPS; ++i)
                if (snd_eno_midi[i]) sus[nsus++] = snd_eno_midi[i];

            int tone = -1;
            if (mel_replay && mel_replay_idx < mel_hist_len) {
                int want = mel_hist[mel_replay_idx++];
                if (harmony_in_world(want) &&
                    harmony_collision_ok(want, sus, nsus))
                    tone = want;                 /* the motif survives   */
            }
            if (tone < 0) {
                /* r19.34: the first note coming back after the player-priority
                 * silence stays low (no high_p reach) so it re-enters calmly. */
                float hp = s_gentle_return ? 0.0f
                                           : (0.05f + composer_params()->high_p);
                tone = harmony_melody_next(mel_last_midi, sus, nsus, hp);
            }
            if (tone > 0) {
                float hz  = tuning_hz((float)tone);
                float amp = 0.062f + gen_rand01() * 0.014f;
                if (s_gentle_return) {
                    /* swell the piece back in: softer, and NO bright strike —
                     * a pad swell, not the exposed "ding" the r19.33 silence
                     * gap used to make of the first returning note. */
                    engine_note_on((uint8_t)MEL_SRC, hz, amp * 0.5f);
                    s_gentle_return = false;
                } else {
                    engine_note_on((uint8_t)MEL_SRC, hz, amp);
                    melody_strike(hz, amp * 2.0f);   /* articulate the onset */
                }
                mel_sounding  = 1;
                mel_last_midi = tone;
                ++mel_note_count;
                if (mel_cur_len < MEL_PHRASE_MAX) mel_cur[mel_cur_len++] = tone;
                --mel_phrase_left;
                mel_off_ms = now_ms + 4000u +
                             (uint32_t)(gen_rand01() * 12000.0f);   /* 4-16 s */
            } else {
                /* nothing SAFE right now — silence is the correct note */
                mel_next_ms = now_ms + 2000u +
                              (uint32_t)(gen_rand01() * 3000.0f);
            }
        } else {
            mel_next_ms = now_ms + 2000u + (uint32_t)(gen_rand01() * 4000.0f);
        }
    }
    }   /* r19.34: end of s_mel_enabled branch */

    /* --- r19.0 spectral undulation (Blendwave principle) ------------------
     * "Same note, evolve timbre": every 400 ms the pad brightness tilt
     * takes one small CORRELATED step (bounded random walk: 20 21 23 26,
     * never 20 97 4) — the bed undulates without new events. */
    if ((int32_t)(now_ms - vmix_next_ms) >= 0) {
        vmix_walk += (gen_rand01() - 0.5f) * 0.10f;
        if (vmix_walk < -0.30f) vmix_walk = -0.30f;
        if (vmix_walk >  0.50f) vmix_walk =  0.50f;
        pad_set_voice_mix(0.45f + vmix_walk);
        vmix_next_ms = now_ms + 400u;
    }
}

static void render_ambient(int16_t *buf, int frames) {
    /* audio.c always calls with frames == AUDIO_BUFFER_FRAMES, but be safe. */
    if (frames > BLOCK) frames = BLOCK;

    /* Smooth per-block engine controls. */
    send_amount_cur += SMOOTH_COEF * (send_amount_tgt - send_amount_cur);
    wet_amp_cur     += SMOOTH_COEF * (wet_amp_tgt     - wet_amp_cur);

    /* Clear the dry + send accumulators (pad ADDS into them). */
    memset(dryL,  0, sizeof(float) * frames);
    memset(dryR,  0, sizeof(float) * frames);
    memset(sendL, 0, sizeof(float) * frames);
    memset(sendR, 0, sizeof(float) * frames);

    pad_render_mix(dryL, dryR, sendL, sendR, frames, send_amount_cur);
    texture_render_mix(dryL, dryR, sendL, sendR, frames, TEXTURE_SEND);
    ambience_render_mix(dryL, dryR, sendL, sendR, frames, AMBIENCE_SEND);
    bass_render_mix(dryL, dryR, sendL, sendR, frames);
    drone_render_mix(dryL, dryR, sendL, sendR, frames);
    /* r18.94: plucks render onto their own bus, run through the MODAL
     * BODY (fixed per-world resonances — the string varies, the body does
     * not; Rings/Elements concept, see body.h), then join dry + hall send.
     * Only the melody voice gets a body: the bed stays clean. */
    {
        static float plkL[BLOCK], plkR[BLOCK];
        static float plkJL[BLOCK], plkJR[BLOCK];   /* pluck's own send: unused */
        memset(plkL, 0, sizeof(float) * (size_t)frames);
        memset(plkR, 0, sizeof(float) * (size_t)frames);
        memset(plkJL, 0, sizeof(float) * (size_t)frames);
        memset(plkJR, 0, sizeof(float) * (size_t)frames);
        pluck_render_mix(plkL, plkR, plkJL, plkJR, frames);
        glass_render_mix(plkL, plkR, plkJL, plkJR, frames);   /* r18.98 */
        body_process(plkL, plkR, frames);
        for (int n = 0; n < frames; ++n) {
            dryL[n]  += plkL[n];
            dryR[n]  += plkR[n];
            sendL[n] += plkL[n] * 0.5f;            /* pluck VERB_SEND kept */
            sendR[n] += plkR[n] * 0.5f;
        }
    }
    /* r19.28: the warm analog voice runs its OWN clean bus (its filter is the
     * character) straight into dry + hall send — no modal body coloring. */
    ember_render_mix(dryL, dryR, sendL, sendR, frames);

    /* r19.41 MASTER-EFFECTS SWAP: echo, blur, tape hiss/crackle, the master
     * reverb render and the shimmer wrap-loop all left this path — the
     * ambient effects engine (fx_master_process below) replaces them with
     * one coherent chain (dark FDN reverb, filtered ping-pong delay, chorus,
     * tape age, shimmer, temporal blur — DREAM CHAIN by default). The send
     * bus is still filled by the generators but no longer consumed here: the
     * engine derives its global spatial send from the Atmosphere macro. The
     * shared reverb tank stays initialised for the V2 synth hosts only. */

    /* Master: dry sum + DC-block + volume → outL/outR; then the effects
     * engine; then the single soft-limit safety net → int16. */
    master_vol_cur += SMOOTH_COEF * (master_vol_tgt - master_vol_cur);
    drive_cur      += SMOOTH_COEF * (drive_tgt      - drive_cur);
    const float mv = master_vol_cur;

    /* r18.89 master drive (per block: curve params + makeup are constant
     * inside a 5.8 ms block; the amount itself is smoothed above). */
    const bool  drv_on   = drive_cur > 1.0e-3f;
    const float drv_g    = 1.0f + 3.5f * drive_cur;          /* 1 .. 4.5  */
    const float drv_bias = 0.28f * drive_cur;                /* asymmetry */
    const float drv_mk   = dsp_drive_makeup(drv_g, drv_bias);
    const float drv_mix  = drive_cur < 0.25f ? drive_cur * 4.0f : 1.0f;

    static float outL[BLOCK], outR[BLOCK];
    for (int n = 0; n < frames; ++n) {
        float L = dryL[n];
        float R = dryR[n];

        if (drv_on) {
            /* dry/wet fade over the first quarter of the knob so tiny
             * settings colour instead of switch. */
            float dL = dsp_drive_shape(L, drv_g, drv_bias) * drv_mk;
            float dR = dsp_drive_shape(R, drv_g, drv_bias) * drv_mk;
            L += drv_mix * (dL - L);
            R += drv_mix * (dR - R);
        }

        /* one-pole DC blocker per channel: y = x - x1 + R·y1 (also eats the
         * small DC offset the drive bias introduces) */
        float yL = L - dc_x1L + DC_R * dc_y1L; dc_x1L = L; dc_y1L = yL;
        float yR = R - dc_x1R + DC_R * dc_y1R; dc_x1R = R; dc_y1R = yR;

        outL[n] = yL * mv;
        outR[n] = yR * mv;
    }
    /* r19.41: the complete master-effects chain on the final float mix —
     * hot-path safe (no heap, bounded, LUT-only transcendentals; verified by
     * the engine property suite). If init failed this is a bit-exact dry
     * pass-through (fail closed). The soft_limit below stays the ONE final
     * limiter in the path. */
    fx_master_process(outL, outR, frames);
    for (int n = 0; n < frames; ++n) {
        /* soft_limit is now a safety net for the rare residual peak above
         * 0.75 — saturation usually already keeps us in range. */
        float yL = soft_limit(outL[n]);
        float yR = soft_limit(outR[n]);
        buf[n * 2 + 0] = (int16_t)(yL * 32767.0f);
        buf[n * 2 + 1] = (int16_t)(yR * 32767.0f);
    }
}

/* ===== r19.16 — SYNTH mode: V2 sound-cores behind the ambient engine =====
 *
 * mode 0 = the ambient engine (identity, default). 1..SYNTH-count = a V2
 * sound-core rendered by the backend (synth_host, registered by the product
 * main — the engine keeps NO link dependency on src/v2, so every existing
 * host test still links). Switching crossfades ~15 ms equal-power between
 * the two rendered paths (REALTIME_AUDIO_RULES §4: algorithm changes need a
 * crossfade, never a hard swap). During the fade both paths render (bounded,
 * a handful of blocks); in steady state only the active one runs. */
#define SYNTH_XFADE_SAMPLES 662            /* ~15 ms at 44.1 kHz */

static int  s_synth_cur   = 0;             /* what the render currently is   */
static int  s_xfade_pos   = -1;            /* -1 = no fade in progress       */
static int16_t s_v2buf[BLOCK * 2];         /* V2 render scratch (interleaved) */

void engine_set_synth_backend(const engine_synth_backend_t *be) { s_synth_be = be; }

void engine_set_synth(int idx) {
    if (idx < 0) idx = 0;
    if (idx > 0 && !s_synth_be) return;    /* no backend (bench/host) = ambient only */
    if (idx == s_synth_tgt) return;
    if (idx > 0) {
        s_synth_be->select(idx - 1);       /* control rate — safe             */
        s_synth_be->panic();
        engine_all_off();                  /* V1 tails decay during fade-out  */
    } else {
        /* Back to ambient: V2 shares the single reverb.c tank and set its
         * own params — restore V1's cached musical reverb (size/damp/drive/
         * wet) so the ambient identity returns exactly as the user left it. */
        recompute_reverb_from_presets();
    }
    s_synth_tgt = idx;                     /* render picks the fade up        */
}

int engine_synth(void) { return s_synth_tgt; }

void engine_render(int16_t *buf, int frames) {
    if (frames > BLOCK) frames = BLOCK;

    int tgt = s_synth_tgt;
    if (tgt != s_synth_cur && s_xfade_pos < 0) s_xfade_pos = 0;

    const bool need_v1 = (s_synth_cur == 0) || (tgt == 0);
    const bool need_v2 = (s_synth_cur >  0) || (tgt >  0);

    if (!need_v2) { render_ambient(buf, frames); return; }
    if (!need_v1 && s_xfade_pos < 0 && s_synth_be) {
        s_synth_be->render(buf, frames);
        return;
    }

    /* fade (or v2↔v2 switch, which select() already made seamless) */
    render_ambient(buf, frames);
    if (s_synth_be) s_synth_be->render(s_v2buf, frames);
    else            memset(s_v2buf, 0, (size_t)frames * 2 * sizeof(int16_t));

    for (int n = 0; n < frames; ++n) {
        float t = 1.0f;                              /* 0 = v1, 1 = v2 side  */
        if (s_xfade_pos >= 0) {
            float p = (float)(s_xfade_pos + n) / (float)SYNTH_XFADE_SAMPLES;
            if (p > 1.0f) p = 1.0f;
            t = (tgt > 0) ? p : 1.0f - p;            /* fade toward target   */
        } else {
            t = (s_synth_cur > 0) ? 1.0f : 0.0f;
        }
        /* linear complementary blend (a+b=1). Both paths are already
         * soft-limited, and at 15 ms the centre dip of a linear fade is
         * inaudible — no per-sample sqrt in the hot path. */
        float a = 1.0f - t, b = t;
        int L = (int)(a * (float)buf[2*n]   + b * (float)s_v2buf[2*n]);
        int R = (int)(a * (float)buf[2*n+1] + b * (float)s_v2buf[2*n+1]);
        if (L >  32767) L =  32767;
        if (L < -32768) L = -32768;
        if (R >  32767) R =  32767;
        if (R < -32768) R = -32768;
        buf[2*n]   = (int16_t)L;
        buf[2*n+1] = (int16_t)R;
    }
    if (s_xfade_pos >= 0) {
        s_xfade_pos += frames;
        if (s_xfade_pos >= SYNTH_XFADE_SAMPLES) {
            s_synth_cur = tgt;
            s_xfade_pos = -1;
        }
    }
}

int engine_active_voices(void) { return pad_active_count(); }
