Sancte3D/AMBIENT/field-ambience-current/firmware-c-next/src/pad.c

/*
 * famPadCore — Step 9. Ported from the Web-Audio `_makePadVoice`.
 *
 * Faithful to the reference structure: two detuned sides, each a 3-saw +
 * 2-square stack into a resonant lowpass swept by LFO + filter-ADSR +
 * brightness, then Haas-delayed and opposing-panned for width, summed under
 * one bloom/decay amp envelope. Default voiceMix = 0 → pure saw character
 * (the squares are weighted in only when the voice param is raised later).
 *
 * Audio-rate work per sample: 10 polyBLEP oscillators + 2 SVF + 2 Haas reads
 * per voice. Filter cutoff is recomputed at control rate (every CTL_DECIMATE
 * samples) — the LFO and envelopes are far slower than audio rate, so this is
 * inaudible and keeps the tanf out of the inner loop.
 */

#include "pad.h"
#include "dsp.h"
#include "padsynth.h"

/* r18.93 — oscillator core selector. 0 = legacy 10-osc polyBLEP stack,
 * 1 = PADsynth spectral-table reads (default). The envelopes, SVF,
 * brightness/motion macros, ensemble drift, Haas and panning are IDENTICAL
 * in both cores — only the tone source changes. Why the swap: the stack
 * makes width from static detune (beating); the PADsynth table IS a living
 * band per partial (Nasca model, see padsynth.h) — wider, deeper, and one
 * table read replaces 10 oscillators (CPU drops hard). */
#ifndef FAM_PAD_CORE
#define FAM_PAD_CORE 1
#endif
#include <math.h>
#include <string.h>

#define DSP_PI       3.14159265358979f
#define SR           ((float)DSP_SAMPLE_RATE_HZ)
#define CTL_DECIMATE 16                         /* control-rate = SR/16 ≈ 2.76 kHz */

/* Amp envelope (seconds). Slow bloom + long tail per the Sound Constitution. */
/* Amp envelope (seconds). Webapp cellOn uses attack 0.8 / release 3.0 — the
 * 1.5 s value from _makePadVoice defaults is for chord-spawn use, not cell
 * taps. Using the spawn value here made cells feel bloomy instead of tap-y. */
#define PAD_ATTACK_S   0.8f
#define PAD_RELEASE_S  3.0f

/* Per-side oscillator stack: 3 saws (×1, ×freqMul, ×0.5) + 2 squares. */
#define OSC_N 5

#define HAAS_LEN 1024                           /* > 0.014 s · 44.1 kHz ≈ 618 */

typedef enum { ENV_IDLE = 0, ENV_ATTACK, ENV_SUSTAIN, ENV_RELEASE } env_state_t;

typedef struct {
    float phase[OSC_N];     /* turns [0,1) */
    float inc[OSC_N];       /* per-sample increment = f·mul / SR */

    /* r18.90 ensemble motion ("breathing detune"). Why the Juno ensemble
     * reads as alive: the movement is PHASE DRIFT between near-unison
     * layers (BBD chorus), not a big static detune — static beating is
     * exactly what makes stacked-saw pads sound like a preset. Principle
     * transferred, not the circuit: each side's detune wobbles ±~1.8 cents
     * on its own sub-0.1 Hz LFO, so the beat rate itself slowly changes.
     * Scaled by the Motion macro (motion_depth) — one emotional knob. */
    float f0;               /* undetuned base freq (Hz)              */
    float det_base;         /* static detune (cents, signed)         */
    float det_mul2;         /* 2nd-saw ratio (1.003 / 0.997)         */
    float wobPhase, wobInc; /* per-side drift LFO (turns)            */

    dsp_svf_t svf;
    float cutoffBase, cutoffMod, fenvAmount;
    float lfoPhase, lfoInc;

    /* r19.5 Blendwave spectral animator: a gentle wandering formant that
     * emphasises a slowly moving harmonic region, so a HELD tone morphs
     * ("same note, evolve timbre" — the Sonicware Ø principle). The centre
     * is driven by the VOICE's spec_w walk, mirrored between the two sides
     * (w vs 1-w) → the two internal oscillators morph in OPPOSITE directions
     * (Yin/Yang), which also makes the stereo image shimmer spectrally. */
    dsp_svf_t animBP;

    /* filter envelope (control rate): attack 0→1, then decay→sustain */
    float fenv, fenvAtkInc, fenvDecCoef, fenvSustain;
    int   fenvStage;        /* 0 attack, 1 decayed */

    float dline[HAAS_LEN];  /* Haas micro-delay */
    int   dpos, ddelay;

    float panL, panR;       /* equal-power pan, baked */
} pad_side_t;

typedef struct {
    bool        used;
    uint8_t     source;
    pad_side_t  side[2];

    float       env;        /* current amp level, peaks at `amp` */
    float       amp;        /* peak target */
    float       atkInc;     /* per-sample linear attack step */
    float       relCoef;    /* per-sample exponential release coef */
    env_state_t state;

    /* r19.5 spectral animator walk (per voice; both sides read it mirrored).
     * A CORRELATED random walk 0..1 — small persistent steps (20,21,23,26…
     * never 20,97,4), the "undulating" motion the Ø gets from morphing
     * through harmonic tables. Fixed-seeded → reproducible in host tests. */
    float       spec_w, spec_tgt;
    uint32_t    spec_rng;
    int         spec_ctr;
} pad_voice_t;

static pad_voice_t voices[PAD_MAX];
static int   ctl_phase;             /* shared control-rate counter */
static float bright_target;         /* brightness offset target (Hz) */
static float bright_cur;            /* smoothed brightness */
static float bright_coef;           /* per-control-block smoothing coef */
static float motion_depth = 1.0f;   /* LFO-depth multiplier (Motion macro) */
static float spec_depth   = 0.0f;   /* r19.5 spectral-animator depth (Motion) */

/* r19.5 animator constants. The formant wanders across the bed's living
 * partials (≈ f0·2 .. f0·14, 220..1550 Hz); moderate Q so it colours the
 * timbre without whistling; gentle gain so it MORPHS, never dominates.
 * SPEC_STEP control ticks ≈ how often a new walk target is picked. */
#define SPEC_LO      220.0f
#define SPEC_HI      1550.0f
#define SPEC_Q       2.2f
#define SPEC_GAIN    0.55f
#define SPEC_STEP    170               /* ~1.0 s between targets @ SR/16 */

/* Oscillator layout per side: 0,1,2 = saws (×1, ×freqMul, ×0.5),
 * 3,4 = squares (×1, ×freqMul). Frequency multipliers below; the second-saw
 * and second-square multipliers are the per-side freqMul, filled in at setup. */
static const float OSC_MUL_BASE[OSC_N]  = { 1.0f, 1.0f, 0.5f, 1.0f, 1.0f };

/* voiceMix is a GLOBAL, smoothed timbre control (0 = warm/pure-saw … ~1.2 =
 * brass). It is applied at render time to ALL voices at once, so changing the
 * pad voice glides the whole stack into the new timbre together instead of
 * leaving old and new timbres ringing side by side. */
static float vmix_target;           /* requested voiceMix */
static float saww_cur, pulsew_cur;  /* smoothed saw / pulse weights */
static float vmix_coef;             /* per-control-block smoothing coef */

void pad_init(void) {
    memset(voices, 0, sizeof voices);
    ctl_phase     = 0;
    bright_target = 0.0f;
    bright_cur    = 0.0f;
    /* brightness glide ~80 ms, evaluated once per control block */
    bright_coef = 1.0f - expf(-(float)CTL_DECIMATE / (0.08f * SR));

    vmix_target = 0.0f;             /* warm */
    saww_cur    = 1.0f;             /* pure saw at boot */
    pulsew_cur  = 0.0f;
    /* timbre glide ~150 ms */
    vmix_coef = 1.0f - expf(-(float)CTL_DECIMATE / (0.15f * SR));
}

void pad_set_brightness(float hz) { bright_target = hz; }
void pad_set_motion(float d)      {
    motion_depth = dsp_clampf(d, 0.0f, 2.0f);
    /* r19.5: MOTION also drives the spectral animator (same emotional
     * direction — "more alive"). 0 = OFF and bit-exact (the reference
     * sound is untouched when MOTION is centred at 0). */
    spec_depth   = dsp_clampf(d, 0.0f, 1.0f);
}

/* Global pad-voice timbre. 0 = warm (pure saw), ~0.6 = strings, ~1.2 = brass
 * (matches the webapp PAD_VOICE_MIXES). Smoothed across all voices. */
void pad_set_voice_mix(float vmix) { vmix_target = dsp_clampf(vmix, 0.0f, 1.5f); }

/* Equal-power pan: p in [-1,1] → (gl,gr). */
static void pan_gains(float p, float *gl, float *gr) {
    p = dsp_clampf(p, -1.0f, 1.0f);
    float a = (p + 1.0f) * 0.25f * DSP_PI;      /* 0 … π/2 */
    *gl = cosf(a);
    *gr = sinf(a);
}

/* Smoothing coefficient for an exponential approach over `tau_s`, evaluated
 * once per control block of CTL_DECIMATE samples. */
static float ctl_coef(float tau_s) {
    if (tau_s <= 0.0f) return 1.0f;
    return 1.0f - expf(-(float)CTL_DECIMATE / (tau_s * SR));
}

static int find_source(uint8_t source) {
    for (int i = 0; i < PAD_MAX; ++i)
        if (voices[i].used && voices[i].source == source) return i;
    return -1;
}

/* Pick a slot: idle first, else steal the quietest (lowest env). */
static int alloc_slot(void) {
    int best = -1; float best_env = 1e9f;
    for (int i = 0; i < PAD_MAX; ++i) {
        if (!voices[i].used) return i;
        if (voices[i].env < best_env) { best_env = voices[i].env; best = i; }
    }
    return best;
}

static void side_setup(pad_side_t *s, float base_freq, int sign, float voice_pan,
                       float detune_cents, float freq_mul, float cutoff_base,
                       float cutoff_rate, float fenv_attack_s, bool keep_phase) {
    float f = base_freq * powf(2.0f, (sign * detune_cents) / 1200.0f);

    const float mul[OSC_N] = { OSC_MUL_BASE[0], freq_mul, OSC_MUL_BASE[2],
                               OSC_MUL_BASE[3], freq_mul };
    for (int k = 0; k < OSC_N; ++k) {
        if (!keep_phase) s->phase[k] = 0.0f;
        s->inc[k]  = f * mul[k] / SR;
    }

    /* r18.90 ensemble motion state. Wobble rates deliberately different per
     * side (0.061/0.087 Hz) and NOT harmonically related to the filter LFO
     * — the drift never settles into a cycle the ear can lock onto. */
    s->f0       = base_freq;
    s->det_base = (float)sign * detune_cents;
    s->det_mul2 = freq_mul;
    s->wobInc   = ((sign > 0) ? 0.087f : 0.061f) / SR;
    if (!keep_phase) s->wobPhase = (sign > 0) ? 0.5f : 0.13f;

#if FAM_PAD_CORE == 1
    /* PADsynth core: phase[0] = main read head, phase[1] = sub-octave body
     * (rate ×0.5). Units are TABLE SAMPLES here, not turns. Deterministic
     * scattered start positions decorrelate voices/sides without rand(). */
    if (!keep_phase) {
        s->phase[0] = (float)(((int)(base_freq * 7.31f) * (sign > 0 ? 131 : 197))
                              & (PADSYNTH_N - 1));
        s->phase[1] = (float)(((int)(base_freq * 3.17f) * (sign > 0 ? 89 : 61))
                              & (PADSYNTH_N - 1));
    }
    s->inc[0] = f / PADSYNTH_F0;
    s->inc[1] = s->inc[0] * 0.5f;
#endif

    if (!keep_phase) { dsp_svf_reset(&s->svf); dsp_svf_reset(&s->animBP); }
    s->cutoffBase  = cutoff_base;
    s->cutoffMod   = 500.0f;
    /* Filter envelope amount: 0 for cell taps (webapp cellOn explicitly
     * disables this — "fenvAmount: 0.0"). The 0.5 value here would belong
     * to the chord-spawn / drone path with their slow filter sweeps; using
     * it on cell taps put a continuous filter-open sweep over every note
     * and made the pad sound matschig. */
    s->fenvAmount  = 0.0f;

    s->lfoInc   = cutoff_rate * (sign > 0 ? 1.13f : 1.0f) / SR;
    if (!keep_phase) s->lfoPhase = (sign > 0) ? 0.37f : 0.0f;

    s->fenv        = 0.0001f;
    s->fenvStage   = 0;
    s->fenvAtkInc  = (1.0f / (fenv_attack_s * SR)) * (float)CTL_DECIMATE;
    s->fenvDecCoef = ctl_coef(4.5f / 3.0f);     /* fenvDecay ≈ 4.5 s */
    s->fenvSustain = 0.65f;

    if (!keep_phase) { memset(s->dline, 0, sizeof s->dline); s->dpos = 0; }
    /* Haas: +side 14 ms, −side 8 ms. */
    s->ddelay = (int)((sign > 0 ? 0.014f : 0.008f) * SR);
    if (s->ddelay >= HAAS_LEN) s->ddelay = HAAS_LEN - 1;

    pan_gains(dsp_clampf(voice_pan + sign * 0.25f, -1.0f, 1.0f), &s->panL, &s->panR);
}
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
